milestogo/reform/historic-reform1/handbook/source/credits/index.rst

Credits
=======

:Concept, Electronics, Software, Manual, Assembly: Lukas F. Hartmann (mntmn)

:Industrial Design: Ana Beatriz Albertini Dantas

:Sleeve Design, Assembly: Greta Melnik

:Special Thanks: FabLab Berlin, Neuform, CCC Berlin/n-te, Fedevel/Voipac, etnaviv, Xorg, Mesa, wayland, Igalia, heise/Make Germany/Helga Hansen, Philip Steffan, Maker Faire Berlin, Interface Critique/Florian Hadler, Gabriel Yoran, JD Music Labs, Crowd Supply, malcolmputer, zakx, darthrake, erlehmann, plomlompom, scallo, dridde, grncdr, oomono, Daniel Stone, Martin Meyerhoff, Gregor May, Chris Healy, Martin Borgert, Stephan Urbach, furan, Radoslaw Kujawa, Novena, Mastodon, a1k, Disko Koenig, S.I.H., The Reform Beta Testers (you!)

:Inter UI Font: rsms

:PCB Production: PCBWay

:Aluminum Milling: Shandong Jiepurui Model Technology Co., Ltd.
                   
:3D Printer: BCN3D Sigma R17

:Reflow Oven: ReflowR

:Stereolitography: Formlabs Form2

:Lab Tools: Rigol DS1054Z, Fluke 117. Weller WD-1, Toolcraft SMD Rework Station
            
:Parts Suppliers: Mouser, DigiKey, Conrad, Voelkner (Fans), GMK Electronic Design (Switches), Schraubenhandel Machholz (Screws), Smooth Group (Hinges), Palm Stream International (Displays), HereWin (Batteries)
                  
:Chips Used: NXP (MCIMX6Q5EYM10AC, SGTL5000XNAA3), Micron (MT41K512M16HA-125), Texas Instruments (BQ24650RVAT, INA260AIPW, TPS61235RWLR, TUSB4041IPAPR, TPS2044BDR, TLV70012, TLV1117-15, LP3962EMP-2.5), ON Semiconductor (CM2020-00TR), Microchip (KSZ9031RNXIA, ATTINY841-SSU, ATMEGA32U4), Diodes Inc. (AP1501A-33K5G-13), Rohm (BR24L02NUX-WTR)
             
:Software Used: Debian GNU/Linux, KiCAD, Inkscape, GIMP, Emacs, Vim, Git, Arduino, LUFA, Blender, Cura, slic3r, Solidworks, FreeCAD, OpenSCAD, Sphinx

Web: https://mntmn.com/reform 
Email: lukas@mntmn.com
Copyright 2018 MNT Media and Technology UG (haftungsbeschränkt), Bluecherstr. 32C, 10961 Berlin
Managing Director: Lukas F. Hartmann
Registergericht: Amtsgericht Charlottenburg
Aktenzeichen: HRB 136605 B
VAT ID: DE278908891
WEEE: DE 33315564 

This book is licensed under GPLv3 or newer.
