milestogo/reform/historic-reform1/handbook/source/motherboard/reform-motherboard-page-1b.pdf

1 2 3 4 5 6

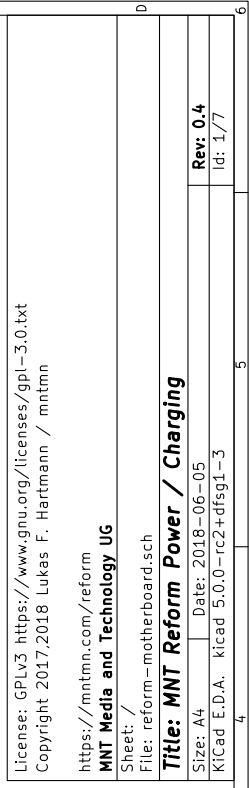
[picture p17: figure]

1 2 3 4 5 6

A

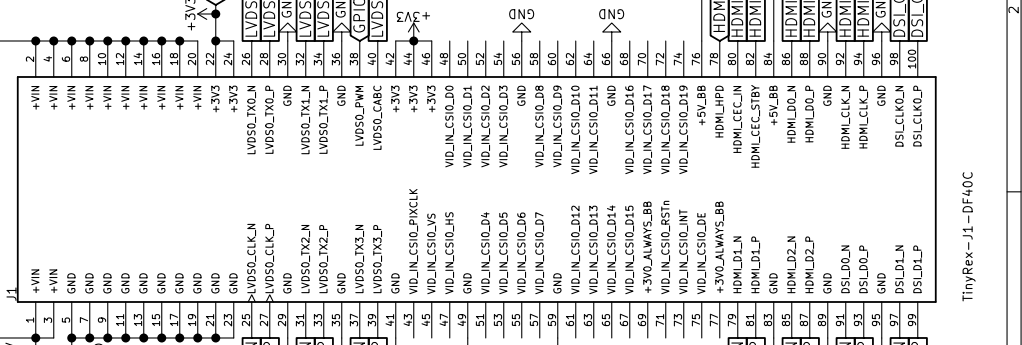
[picture p18: figure]
1 +VIN; 2 +VIN; 3 +VIN; 4 GND; 5 +VIN; 6 GND; 7 +VIN; 8 GND

BC

D

A

BC

D Date: 2018-06-05 KiCad E.D.A. kicad 5.0.0-rc2+dfsg1-3 Rev: 0.4 Size: A4 Id: 1/7 License: GPLv3 https://www.gnu.org/licenses/gpl-3.0.txt Copyright 2017,2018 Lukas F. Hartmann / mntmn https://mntmn.com/reform MNT Media and Technology UG Sheet: / File: reform-motherboard.sch Title: MNT Reform Power / Charging +VIN

9 +VIN 10 +VIN 20 GND 30 LVDS0_CABC 40 VID_IN_CSI0_D1 50 VID_IN_CSI0_D9 60 VID_IN_CSI0_D17 70 HDMI_CEC_IN 80 GND 90 GND 11 GND 21 LVDS0_TX2_N 31 GND 41 VID_IN_CSI0_D4 51 VID_IN_CSI0_D12 61 VID_IN_CSI0_RSTn 71 HDMI_D1_P 81 DSI_D0_N 91 +VIN 12 +3V3 22 LVDS0_TX1_N 32 +3V3 42 VID_IN_CSI0_D2 52 VID_IN_CSI0_D10 62 VID_IN_CSI0_D18 72 HDMI_CEC_STBY 82 HDMI_CLK_N 92 GND 13 GND 23 LVDS0_TX2_P 33 VID_IN_CSI0_PIXCLK 43 VID_IN_CSI0_D5 53 VID_IN_CSI0_D13 63 VID_IN_CSI0_INT 73 GND 83 DSI_D0_P 93 +VIN 14 +3V3 24 LVDS0_TX1_P 34 +3V3 44 VID_IN_CSI0_D3 54 VID_IN_CSI0_D11 64 VID_IN_CSI0_D19 74 +5V_BB 84 HDMI_CLK_P 94 GND 15 LVDS0_CLK_N 25 GND 35 VID_IN_CSI0_VS 45 VID_IN_CSI0_D6 55 VID_IN_CSI0_D14 65 VID_IN_CSI0_DE 75 HDMI_D2_N 85 GND 95 +VIN 16 LVDS0_TX0_N 26 GND 36 +3V3 46 GND 56 GND 66 +5V_BB 76 HDMI_D0_N 86 GND 96 GND 17 LVDS0_CLK_P 27 LVDS0_TX3_N 37 VID_IN_CSI0_HS 47 VID_IN_CSI0_D7 57 VID_IN_CSI0_D15 67 +3V0_ALWAYS_BB 77 HDMI_D2_P 87 DSI_D1_N 97 +VIN 18 LVDS0_TX0_P 28 LVDS0_PWM 38 VID_IN_CSI0_D0 48 VID_IN_CSI0_D8 58 VID_IN_CSI0_D16 68 HDMI_HPD 78 HDMI_D0_P 88 DSI_CLK0_N 98 GND 19 GND 29 LVDS0_TX3_P 39 GND 49 GND 59 +3V0_ALWAYS_BB 69 HDMI_D1_N 79 GND 89 DSI_D1_P 99 DSI_CLK0_P 100 J1TinyRex-J1-DF40C BOOT_MODE1_CON

# 1 RSTINn

# 2 BOOT_MODE0_CON

# 3 RSTOUTn

# 4 POK_1V5

# 5 PMIC_ON_REQ

# 6 POK_5V_BB

# 7 ON_OFF

# 8 POK_3V3_BB

9 USER_BUTTON 10 AUD4_TXD 20 FLEXCAN1_TX 30 GND 40 I2C2_SDA 50 UART4_RXD 60 USB_OC 70 PCIE_CLK_N 80 GND 90 GND 11 GND 21 GND 31 GND 41 GND 51 UART2_TXD 61 GND 71 PCIE_TX_P 81 CSI_D2_N 91 GND 12 AUD4_RXD 22 FLEXCAN1_RX 32 SATA_TX_N 42 I2C3_SDA 52 UART5_TXD 62 USB1_PWR_EN 72 PCIE_CLK_P 82 CSI_D0_N 92 CPU_GPIO0 13 CSPI1_CLK 23 SD3_CD 33 SD3_DATA0 43 UART1_TXD 53 UART2_RXD 63 USB0_N 73 GND 83 CSI_D2_P 93 AUD4_CLK 14 GND 24 GND 34 SATA_TX_P 44 I2C3_SCL 54 UART5_RXD 64 USB0_PWR_EN 74 GND 84 CSI_D0_P 94 CPU_GPIO1 15 CSPI1_MOSI 25 SD3_WP 35 SD3_DATA1 45 UART1_RXD 55 GND 65 USB0_P 75 PCIE_RX_N 85 GND 95 AUD4_TXC 16 I2C1_SCL 26 SATA_RX_N 36 GND 46 GND 56 GND 66 PCIE_WAKE 76 CSI_CLK0_N 86 GND 96 GPIO_OR_PWM_1 17 CSPI1_MISO 27 SD3_CLK 37 SD3_DATA2 47 UART1_RTS 57 USB1_N 67 GND 77 PCIE_RX_P 87 CSI_D3_N 97 AUD4_TXFS 18 I2C1_SDA 28 SATA_RX_P 38 I2C2_SCL 48 UART4_TXD 58 USB0_ID 68 GND 78 CSI_CLK_P 88 CSI_D1_N 98 GPIO_OR_PWM_2 19 CSPI1_CS0 29 SD3_CMD 39 SD3_DATA3 49 UART1_CTS 59 USB1_P 69 PCIE_TX_N 79 GND 89 CSI_D3_P 99 CSI_D1_P 100 J2TinyRex-J2-DF40C TRD0_N

# 1 TRD2_N

# 2 TRD0_P

# 3 TRD2_P

# 4 GND

# 5 +1V2_BB

# 6 TRD1_N

# 7 TRD3_N

# 8 TRD1_P

9 TRD3_P 10 +1V2_BB 20 DISP1_D4 30 DISP1_D12 40 SD4_DATA0 50 SD4_DATA4 60 CSPI2_CLK 70 GND 80 SD1_CMD 90 GND 11 DISP1_RDX 21 DISP1_D2 31 DISP1_D10 41 DISP1_D18 51 SD4_WP 61 UART3_TXD 71 SD1_DATA4 81 GND 91 +1V2_BB 12 DISP1_PIXCLK 22 DISP1_D5 32 DISP1_D13 42 SD4_DATA1 52 SD4_DATA5 62 CSPI2_MOSI 72 SD1_DATA0 82 GND 92 DISP1_INT 13 DISP1_WRX 23 DISP1_D3 33 DISP1_D11 43 DISP1_D19 53 SD4_CD 63 UART3_RXD 73 SD1_DATA5 83 NANDF_D4 93 ENET_LED_LINK 14 DISP1_VSYNCH 24 DISP1_D6 34 DISP1_D14 44 SD4_DATA2 54 SD4_DATA6 64 CSPI2_MISO 74 SD1_DATA1 84 NANDF_ALE 94 DISP1_CS1 15 GND 25 GND 35 GND 45 GND 55 SD1_WP 65 UART3_RTS 75 SD1_DATA6 85 NANDF_D5 95 ENET_LED_RX 16 DISP1_HSYNCH 26 DISP1_D7 36 DISP1_D15 46 SD4_DATA3 56 SD4_DATA7 66 CSPI2_CS0 76 SD1_DATA2 86 NANDF_CLE 96 DISP1_CS0 17 DISP1_D0 27 DISP1_D8 37 DISP1_D16 47 SD4_CLK 57 SD1_CD 67 UART3_CTS 77 SD1_DATA7 87 NANDF_D6 97 DISP1_RSTn 18 GND 28 GND 38 +2V5_BB 48 +2V5_BB 58 GND 68 CSPI2_CS1 78 SD1_DATA3 88 NANDF_RB0 98 DISP1_D/CX 19 DISP1_D1 29 DISP1_D9 39 DISP1_D17 49 SD4_CMD 59 GND 69 GND 79 SD1_CLK 89 NANDF_D7 99 NANDF_WPn 100 J3TinyRex-J3-DF40C ReformPower reform-power.sch +5V GND +5V GND +3V3 +3V3 POK_1V5_MODULE POK_5V POK_3V3USB1_N USB1_P USB0_N USB0_P RSTINn RSTOUTn HDMI_HPD HDMI_CLK_N HDMI_CLK_P HDMI_D1_N HDMI_D1_P HDMI_D2_N HDMI_D2_P HDMI_D0_N HDMI_D0_P UART1_TXD UART1_RTS UART1_RXD UART1_CTS SD1_DATA0 SD1_DATA1 SD1_DATA2 SD1_DATA3 SD1_CMD SD1_WP SD1_CD SD1_CLK +2V5 SATA_RX_N SATA_RX_P SATA_TX_N SATA_TX_P USB_OC HDMI_CEC_IN HDMI_CEC_STBY ReformSATA_SD reform-sata-sd.sch SD3_DATA0 SD3_DATA1 SD3_DATA2 SD3_DATA3 GND GND GND SD3_CD SD3_WP SD3_CMD SD3_CLK ReformPCIe reform-pcie.sch PCIE_TX_N PCIE_TX_P PCIE_RX_N PCIE_RX_P PCIE_WAKE PCIE_CLK_N PCIE_CLK_P reform-eth-usb reform-eth-usb.sch ReformDisplay reform-display.sch

0 GND MH1 BoardMount MH2 BoardMount MH3 BoardMount MH4 BoardMount GND GND GND GND MH5 ModuleMount MH6 ModuleMount TP13 TEST_1V2 1

4

3

2

# 1 J20 Conn_GPIO1

6

5

4

3

2

1 J35 Conn_SPI1 +3V3 +3V3 GND CSI_D2_N CSI_D2_P CSI_D3_N CSI_D3_P CSI_D0_N CSI_D0_P CSI_D1_N CSI_D1_P GND GND CSI_CLK0_N CSI_CLK0_P DSI_D0_N DSI_D0_P DSI_D1_N DSI_D1_P DSI_CLK0_N DSI_CLK0_P J8 TEST_BM0
