milestogo/reform/historic-reform1/handbook/source/index.rst

.. Reform documentation master file, created by
   sphinx-quickstart on Thu Jun  7 14:01:00 2018.
   You can adapt this file completely to your liking, but it should at least
   contain the root `toctree` directive.
   
MNT Reform Operator Handbook
============================

.. toctree::
   :maxdepth: 3

   quickstart/index
   case/index
   motherboard/index
   motherboard/attiny
   keyboard/index
   trackball/index
   thermal/index
   boot/index
   debug/index
   credits/index

.. raw:: latex

    \clearpage
