milestogo/reform/historic-reform1/handbook/source/motherboard/index.rst

The Motherboard
===============


            
Schematics
----------



Power
-----



Storage
-------



Display
-------


           
PCIe
----



Ethernet, USB
-------------


            
Audio
-----
