milestogo/reform/reform2-handbook/misc-content/old-reform1-handbook/reform-handbook.pdf

## CONTENTS

1 Quick Start | 1
2 The Case | 3
3 The Motherboard | 9
4 The Battery/Lid Controller | 19
5 The Keyboard | 21
6 The Trackball | 25

i

7 Thermal | 29
8 System Boot Details | 31
9 Debugging | 33
10 Credits | 35

ii

CHAPTER

## ONE

## QUICK START

Thank you for acquiring MNT Reform, a portable open-source computer system. Reform can be powered either by the internal LiFePo4 battery or by the 5V wall adapter. The wall adapter will automatically charge the battery if present. For safety reasons, the battery cable is not connected by default. To use the battery, unscrew the bottom lid and plug the white battery cable plug into the battery connector on the motherboard. Then reattach the bottom lid.
To switch the system on, push the power switch (located on the front of the device) to the right. The i.MX6 QuadPlus (https://www.nxp.com/products/processors-and-microcontrollers/arm-based-processors-and-mcus/i.mx-applications-processors/i.mx-6-processors/i.mx-6quadplus-proce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) System-on-Chip will try to boot from the internal SD card. You should be greeted by U-Boot and the MNT logo in the upper right corner of the display. If not interrupted by a keypress, Reform will boot into the Debian GNU/Linux operating system that is preinstalled on the SD card. The kernel will show diagnostic information as it activates all the devices in the system, and you’ll end up at the login prompt if everything is OK.
To log in, enter root as the username. There is no default password, so you should secure the root account by setting a password. After completing the setup process, you can do this by executing:

passwd

After the first login, the setup script will run and guide you through a few steps like setting the timezone, keyboard layout, network settings and so on.
From the console environment, you can:
- Format an mSATA SSD drive (if you put one in the mSATA slot) and install an OS to it
- Create standard user accounts
- Inspect or repair the system
To start the X windowing system, type:

xinit

By default, when using the root account, this will start the OpenBox window manager. You can change this by editing the file /root/.xinitrc.
You can install additional software and desktop environments by using apt, for example apt install firefox. You can find more information about using apt by reading its manual page. Manual pages are accessed by executing man programname, for example:

1

MNT Reform Operator Handbook

man apt

Enjoy your Reform computer!

### 2 Chapter 1. Quick Start

## TWO

## THE CASE

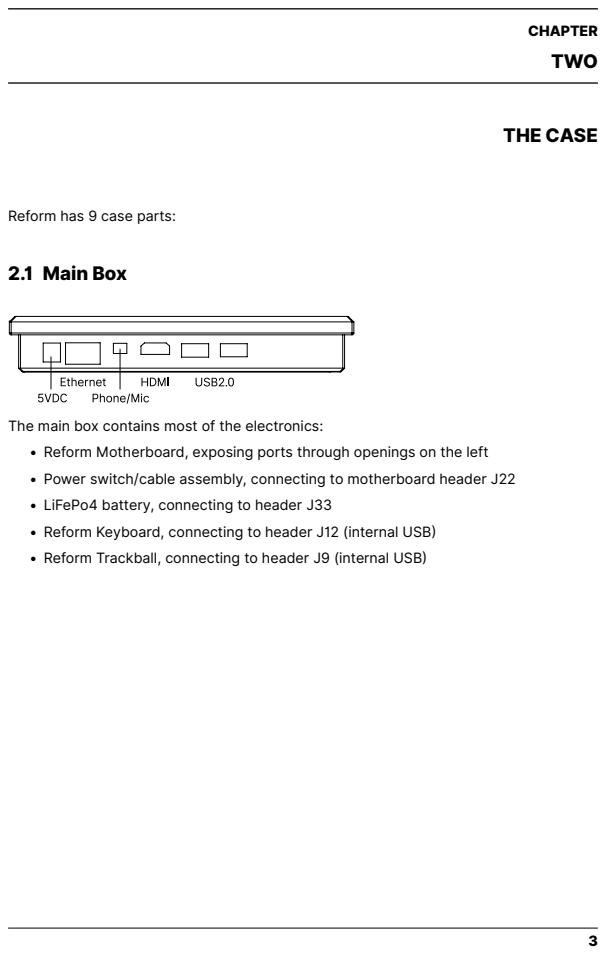
[picture p20: page 7]
CHAPTER; 2.1 Main Box

Reform has 9 case parts:

The main box contains most of the electronics:
• Reform Motherboard, exposing ports through openings on the left
• Power switch/cable assembly, connecting to motherboard header J22
• LiFePo4 battery, connecting to header J33
• Reform Keyboard, connecting to header J12 (internal USB)
• Reform Trackball, connecting to header J9 (internal USB)

## 2.2 Main Box Top

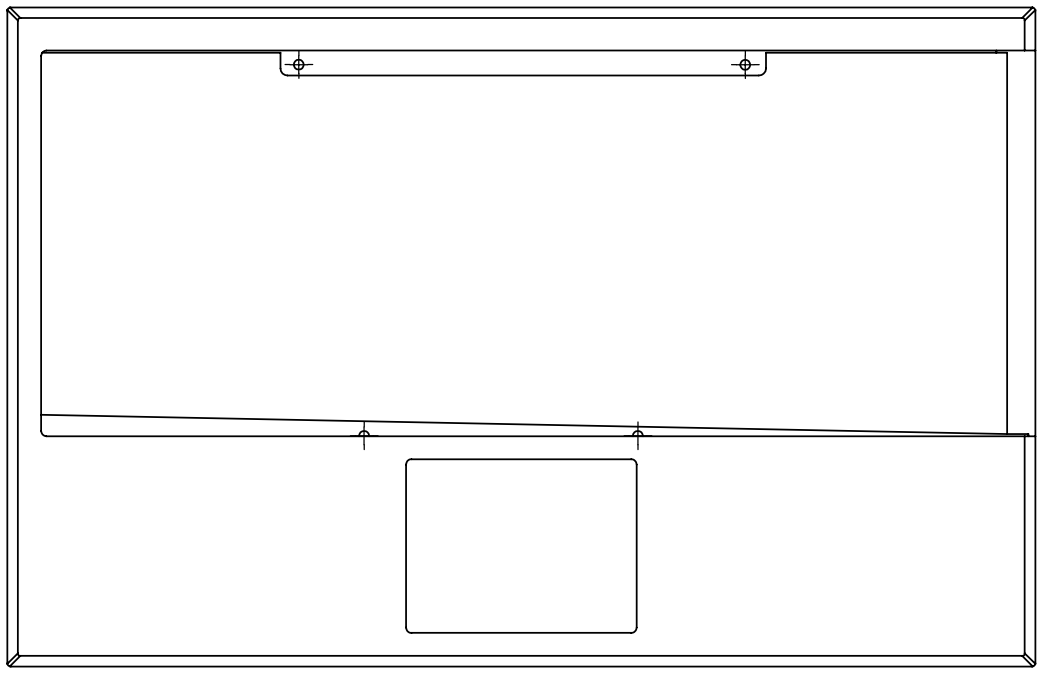
[picture p21: figure]

The main box top is pressed onto the main box to close it from the top. It acts as a palm rest and bezel for the keyboard and trackball. The keyboard is slided into this part’s keyboard slot from the right.

### 4 Chapter 2. The Case

## 2.3 Screen Back

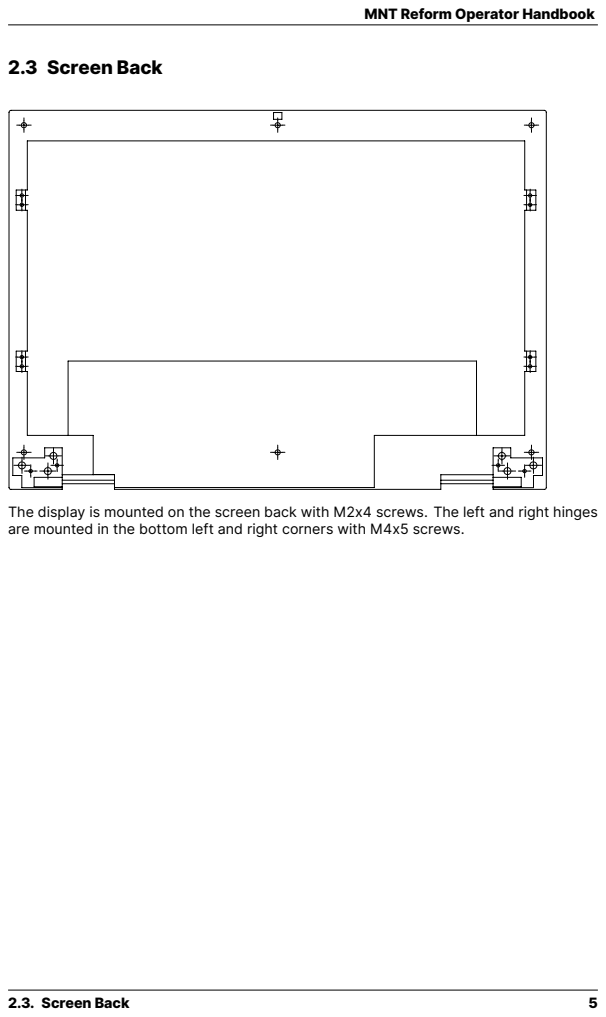
[picture p22: page 9]
2.3. Screen Back

The display is mounted on the screen back with M2x4 screws. The left and right hinges
are mounted in the bottom left and right corners with M4x5 screws.

## 2.4 Screen Front

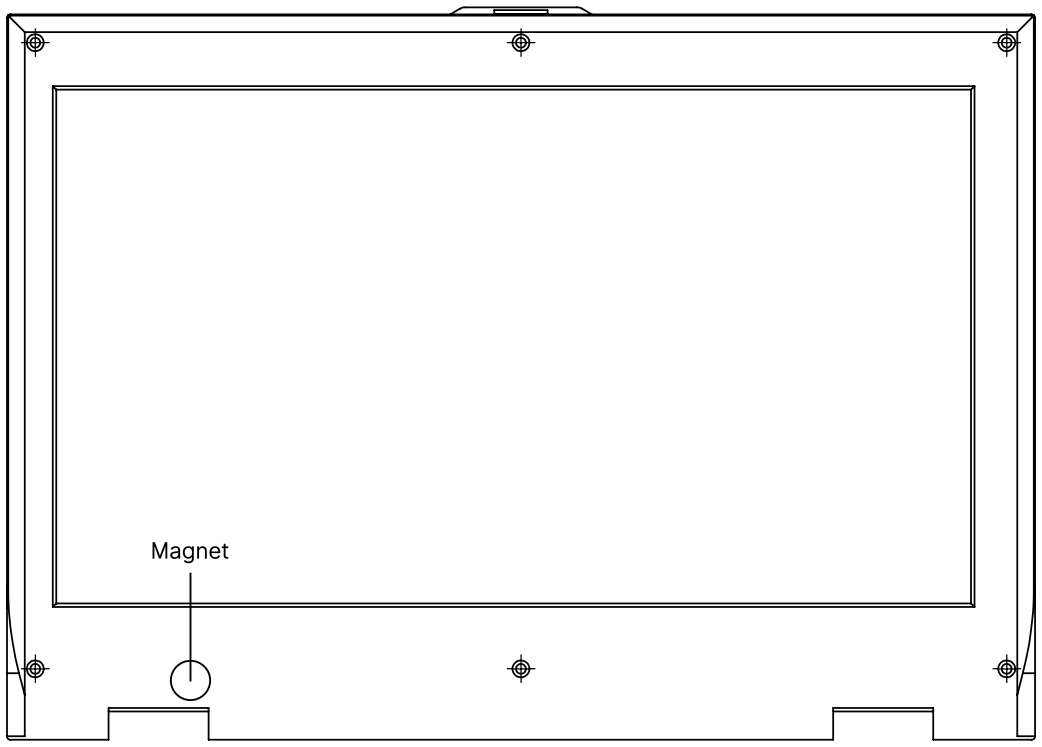
[picture p23: figure]

This part serves as a bezel for the display and holds the case closing strap. It also has a magnet attached to it on the lower left that is sensed by the lid sensor. The screen front is mounted to the back with M3x6 screws.

## 2.5 Screen Support

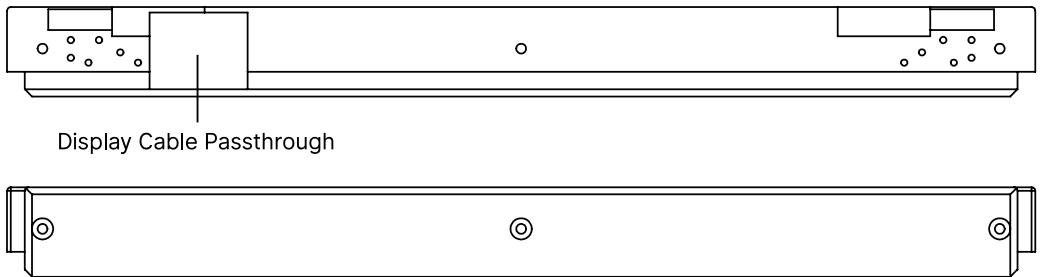
[picture p24: figure]

The screen support connects the main box to the screen via the hinges. The display’s LVDS (motherboard header J14) and power cable (motherboard header J26) is passed through this part, as well as the lid sensor cable (J34).

### 6 Chapter 2. The Case

## 2.6 Screen Support Lid

This is a thin part covering the screen support’s top. On the left, it contains a pocket for the hall effect sensor that detects the magnet on the screen front. The sensor signals opening and closing of the lid.

## 2.7 Keyboard Closure

This part is inserted into the main box top after the keyboard to secure it in place.

## 2.8 Grid Plate

This lasercut acrylic part is sandwiched between the main box’ inner top and the motherboard. It has the mounting holes for the motherboard and other internal devices and isolates the motherboard from the keyboard.

## 2.9 Bottom Plate

The bottom plate closes the main box from the bottom. It contains mounting holes for the fan and vent holes for the fan’s air intake. The fan is connected to motherboard header J15 before screwing in the plate.

2.6. Screen Support Lid | 7

### 8 Chapter 2. The Case

9

## THREE

## THE MOTHERBOARD

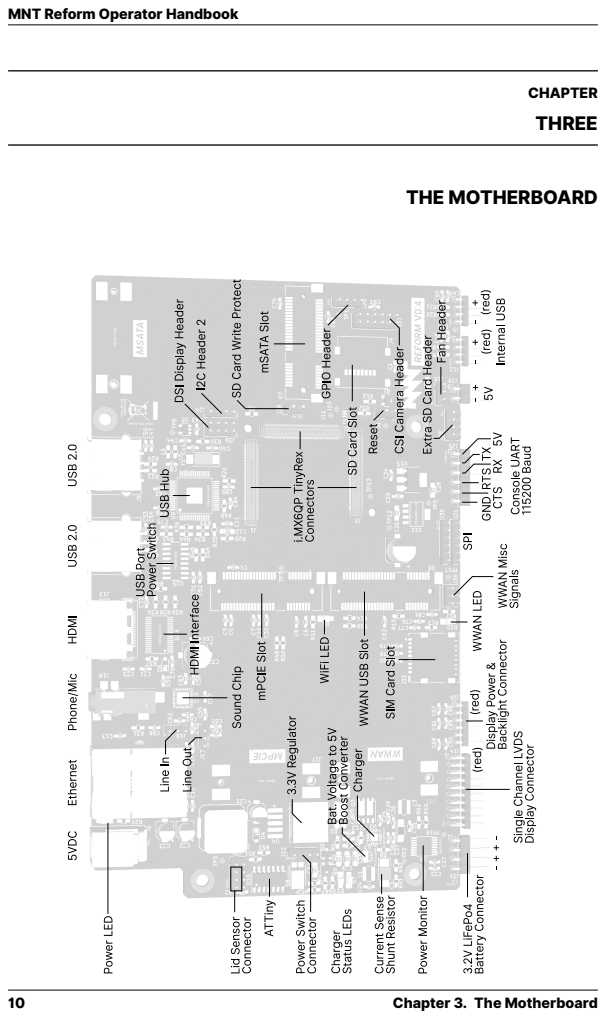
[picture p25: page 14]
CHAPTER

10 Chapter 3. The Motherboard

## 3.1 Schematics

1 2 3 4 5 6

1 2 3 4 5 6

A

BC

D

A

BC

D Date: 2018-06-05 KiCad E.D.A. kicad 5.0.0-rc2+dfsg1-3 Rev: 0.4 Size: A4 Id: 1/7 License: GPLv3 https://www.gnu.org/licenses/gpl-3.0.txt Copyright 2017,2018 Lukas F. Hartmann / mntmn https://mntmn.com/reform MNT Media and Technology UG Sheet: / File: reform-motherboard.sch Title: MNT Reform Power / Charging +VIN

1 +VIN

2 +VIN
3 +VIN

4 GND
5 +VIN

6 GND
7 +VIN

8 GND

9 +VIN 10 +VIN 20 GND 30 LVDS0_CABC 40 VID_IN_CSI0_D1 50 VID_IN_CSI0_D9 60 VID_IN_CSI0_D17 70 HDMI_CEC_IN 80 GND 90 GND 11 GND 21 LVDS0_TX2_N 31 GND 41 VID_IN_CSI0_D4 51 VID_IN_CSI0_D12 61 VID_IN_CSI0_RSTn 71 HDMI_D1_P 81 DSI_D0_N 91 +VIN 12 +3V3 22 LVDS0_TX1_N 32 +3V3 42 VID_IN_CSI0_D2 52 VID_IN_CSI0_D10 62 VID_IN_CSI0_D18 72 HDMI_CEC_STBY 82 HDMI_CLK_N 92 GND 13 GND 23 LVDS0_TX2_P 33 VID_IN_CSI0_PIXCLK 43 VID_IN_CSI0_D5 53 VID_IN_CSI0_D13 63 VID_IN_CSI0_INT 73 GND 83 DSI_D0_P 93 +VIN 14 +3V3 24 LVDS0_TX1_P 34 +3V3 44 VID_IN_CSI0_D3 54 VID_IN_CSI0_D11 64 VID_IN_CSI0_D19 74 +5V_BB 84 HDMI_CLK_P 94 GND 15 LVDS0_CLK_N 25 GND 35 VID_IN_CSI0_VS 45 VID_IN_CSI0_D6 55 VID_IN_CSI0_D14 65 VID_IN_CSI0_DE 75 HDMI_D2_N 85 GND 95 +VIN 16 LVDS0_TX0_N 26 GND 36 +3V3 46 GND 56 GND 66 +5V_BB 76 HDMI_D0_N 86 GND 96 GND 17 LVDS0_CLK_P 27 LVDS0_TX3_N 37 VID_IN_CSI0_HS 47 VID_IN_CSI0_D7 57 VID_IN_CSI0_D15 67 +3V0_ALWAYS_BB 77 HDMI_D2_P 87 DSI_D1_N 97 +VIN 18 LVDS0_TX0_P 28 LVDS0_PWM 38 VID_IN_CSI0_D0 48 VID_IN_CSI0_D8 58 VID_IN_CSI0_D16 68 HDMI_HPD 78 HDMI_D0_P 88 DSI_CLK0_N 98 GND 19 GND 29 LVDS0_TX3_P 39 GND 49 GND 59 +3V0_ALWAYS_BB 69 HDMI_D1_N 79 GND 89 DSI_D1_P 99 DSI_CLK0_P 100 J1TinyRex-J1-DF40C BOOT_MODE1_CON

1 RSTINn

2 BOOT_MODE0_CON
3 RSTOUTn

4 POK_1V5
5 PMIC_ON_REQ

6 POK_5V_BB
7 ON_OFF

8 POK_3V3_BB

9 USER_BUTTON 10 AUD4_TXD 20 FLEXCAN1_TX 30 GND 40 I2C2_SDA 50 UART4_RXD 60 USB_OC 70 PCIE_CLK_N 80 GND 90 GND 11 GND 21 GND 31 GND 41 GND 51 UART2_TXD 61 GND 71 PCIE_TX_P 81 CSI_D2_N 91 GND 12 AUD4_RXD 22 FLEXCAN1_RX 32 SATA_TX_N 42 I2C3_SDA 52 UART5_TXD 62 USB1_PWR_EN 72 PCIE_CLK_P 82 CSI_D0_N 92 CPU_GPIO0 13 CSPI1_CLK 23 SD3_CD 33 SD3_DATA0 43 UART1_TXD 53 UART2_RXD 63 USB0_N 73 GND 83 CSI_D2_P 93 AUD4_CLK 14 GND 24 GND 34 SATA_TX_P 44 I2C3_SCL 54 UART5_RXD 64 USB0_PWR_EN 74 GND 84 CSI_D0_P 94 CPU_GPIO1 15 CSPI1_MOSI 25 SD3_WP 35 SD3_DATA1 45 UART1_RXD 55 GND 65 USB0_P 75 PCIE_RX_N 85 GND 95 AUD4_TXC 16 I2C1_SCL 26 SATA_RX_N 36 GND 46 GND 56 GND 66 PCIE_WAKE 76 CSI_CLK0_N 86 GND 96 GPIO_OR_PWM_1 17 CSPI1_MISO 27 SD3_CLK 37 SD3_DATA2 47 UART1_RTS 57 USB1_N 67 GND 77 PCIE_RX_P 87 CSI_D3_N 97 AUD4_TXFS 18 I2C1_SDA 28 SATA_RX_P 38 I2C2_SCL 48 UART4_TXD 58 USB0_ID 68 GND 78 CSI_CLK_P 88 CSI_D1_N 98 GPIO_OR_PWM_2 19 CSPI1_CS0 29 SD3_CMD 39 SD3_DATA3 49 UART1_CTS 59 USB1_P 69 PCIE_TX_N 79 GND 89 CSI_D3_P 99 CSI_D1_P 100 J2TinyRex-J2-DF40C TRD0_N

1 TRD2_N

2 TRD0_P
3 TRD2_P

4 GND
5 +1V2_BB

6 TRD1_N
7 TRD3_N

8 TRD1_P

9 TRD3_P 10 +1V2_BB 20 DISP1_D4 30 DISP1_D12 40 SD4_DATA0 50 SD4_DATA4 60 CSPI2_CLK 70 GND 80 SD1_CMD 90 GND 11 DISP1_RDX 21 DISP1_D2 31 DISP1_D10 41 DISP1_D18 51 SD4_WP 61 UART3_TXD 71 SD1_DATA4 81 GND 91 +1V2_BB 12 DISP1_PIXCLK 22 DISP1_D5 32 DISP1_D13 42 SD4_DATA1 52 SD4_DATA5 62 CSPI2_MOSI 72 SD1_DATA0 82 GND 92 DISP1_INT 13 DISP1_WRX 23 DISP1_D3 33 DISP1_D11 43 DISP1_D19 53 SD4_CD 63 UART3_RXD 73 SD1_DATA5 83 NANDF_D4 93 ENET_LED_LINK 14 DISP1_VSYNCH 24 DISP1_D6 34 DISP1_D14 44 SD4_DATA2 54 SD4_DATA6 64 CSPI2_MISO 74 SD1_DATA1 84 NANDF_ALE 94 DISP1_CS1 15 GND 25 GND 35 GND 45 GND 55 SD1_WP 65 UART3_RTS 75 SD1_DATA6 85 NANDF_D5 95 ENET_LED_RX 16 DISP1_HSYNCH 26 DISP1_D7 36 DISP1_D15 46 SD4_DATA3 56 SD4_DATA7 66 CSPI2_CS0 76 SD1_DATA2 86 NANDF_CLE 96 DISP1_CS0 17 DISP1_D0 27 DISP1_D8 37 DISP1_D16 47 SD4_CLK 57 SD1_CD 67 UART3_CTS 77 SD1_DATA7 87 NANDF_D6 97 DISP1_RSTn 18 GND 28 GND 38 +2V5_BB 48 +2V5_BB 58 GND 68 CSPI2_CS1 78 SD1_DATA3 88 NANDF_RB0 98 DISP1_D/CX 19 DISP1_D1 29 DISP1_D9 39 DISP1_D17 49 SD4_CMD 59 GND 69 GND 79 SD1_CLK 89 NANDF_D7 99 NANDF_WPn 100 J3TinyRex-J3-DF40C ReformPower reform-power.sch +5V GND +5V GND +3V3 +3V3 POK_1V5_MODULE POK_5V POK_3V3USB1_N USB1_P USB0_N USB0_P RSTINn RSTOUTn HDMI_HPD HDMI_CLK_N HDMI_CLK_P HDMI_D1_N HDMI_D1_P HDMI_D2_N HDMI_D2_P HDMI_D0_N HDMI_D0_P UART1_TXD UART1_RTS UART1_RXD UART1_CTS SD1_DATA0 SD1_DATA1 SD1_DATA2 SD1_DATA3 SD1_CMD SD1_WP SD1_CD SD1_CLK +2V5 SATA_RX_N SATA_RX_P SATA_TX_N SATA_TX_P USB_OC HDMI_CEC_IN HDMI_CEC_STBY ReformSATA_SD reform-sata-sd.sch SD3_DATA0 SD3_DATA1 SD3_DATA2 SD3_DATA3 GND GND GND SD3_CD SD3_WP SD3_CMD SD3_CLK ReformPCIe reform-pcie.sch PCIE_TX_N PCIE_TX_P PCIE_RX_N PCIE_RX_P PCIE_WAKE PCIE_CLK_N PCIE_CLK_P reform-eth-usb reform-eth-usb.sch ReformDisplay reform-display.sch

0 GND MH1 BoardMount MH2 BoardMount MH3 BoardMount MH4 BoardMount GND GND GND GND MH5 ModuleMount MH6 ModuleMount TP13 TEST_1V2 1

4

3

2

1 J20 Conn_GPIO1

6

5

4

3

2

1 J35 Conn_SPI1 +3V3 +3V3 GND CSI_D2_N CSI_D2_P CSI_D3_N CSI_D3_P CSI_D0_N CSI_D0_P CSI_D1_N CSI_D1_P GND GND CSI_CLK0_N CSI_CLK0_P DSI_D0_N DSI_D0_P DSI_D1_N DSI_D1_P DSI_CLK0_N DSI_CLK0_P J8 TEST_BM0

3.1. Schematics | 11

## 3.2 Power

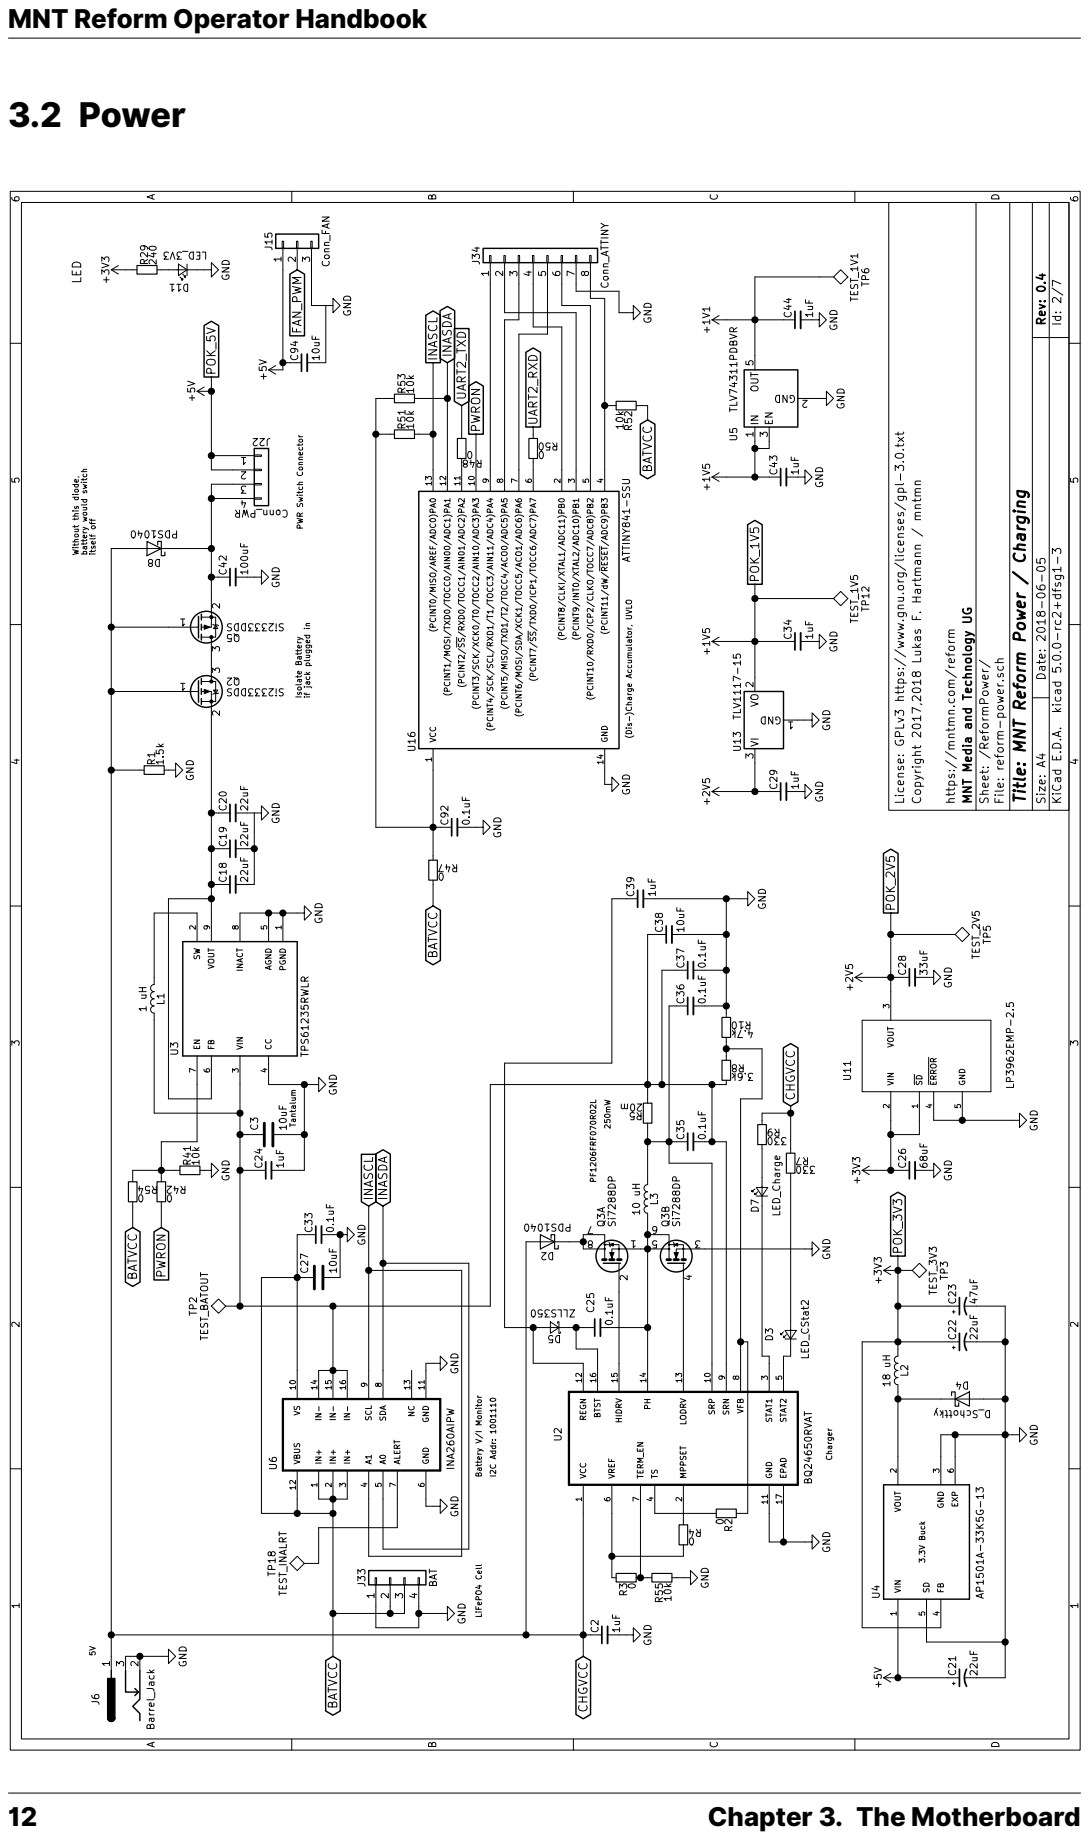
[picture p26: page 16]

D Date: 2018-06-05 KiCad E.D.A. kicad 5.0.0-rc2+dfsg1-3 Rev: 0.4 Size: A4 Id: 2/7 License: GPLv3 https://www.gnu.org/licenses/gpl-3.0.txt Copyright 2017,2018 Lukas F. Hartmann / mntmn https://mntmn.com/reform MNT Media and Technology UG Sheet: /ReformPower/ File: reform-power.sch Title: MNT Reform Power / Charging PGND

9 SRP 10 GND 11 REGN 12 LODRV 13 PH 14 HIDRV 15 BTST 16 EPAD 17 U2 BQ24650RVAT GND L3 10 uH C42 100uF GND GND C43 1uF GND C44 1uF GND TP6 TEST_1V1 GND +1V5 +1V1

4 J33 BAT INASCL INASDA INASCL INASDA BATVCC GND C92 0.1uF GND

9 VS 10 GND 11 VBUS 12 NC 13 IN- 14 IN- 15 IN- 16 U6INA260AIPW GND I2C Addr: 1001110 +5V PWRON 5V 3.3V Buck R11.5k GND +3V3 +5V

9 (PCINT3/SCK/XCK0/T0/TOCC2/AIN10/ADC3)PA3 10 (PCINT2/SS/RXD0/TOCC1/AIN01/ADC2)PA2 11 (PCINT1/MOSI/TXD0/TOCC0/AIN00/ADC1)PA1 12 (PCINT0/MISO/AREF/ADC0)PA0 13 GND 14 U16 ATTINY841-SSU R53 10k R51 10k PWRON

2 J6 Barrel_Jack GND C21 22uF L2 18 uH D4 D_Schottky C22 22uF C23 47uF +2V5 C26 68uF GND POK_2V5 C28 33uF GND TP5 TEST_2V5 TP3 TEST_3V3 GND C29 1uF GND POK_1V5 C34 1uF +1V5 GND TP12 TEST_1V5 SD

2 3Q2 Si2333DDS TP2 TEST_BATOUT Isolate Battery if jack plugged in 1

2 VI 3 U13 TLV1117-15 GND C24 1uF GND C27 10uF C33 0.1uF GND Battery V/I Monitor Tantalum IN+

6 U4AP1501A-33K5G-13 L1 1 uH C310uF GND GND C18 22uF C19 22uF C20 22uF GND GND

## 3.3 Storage

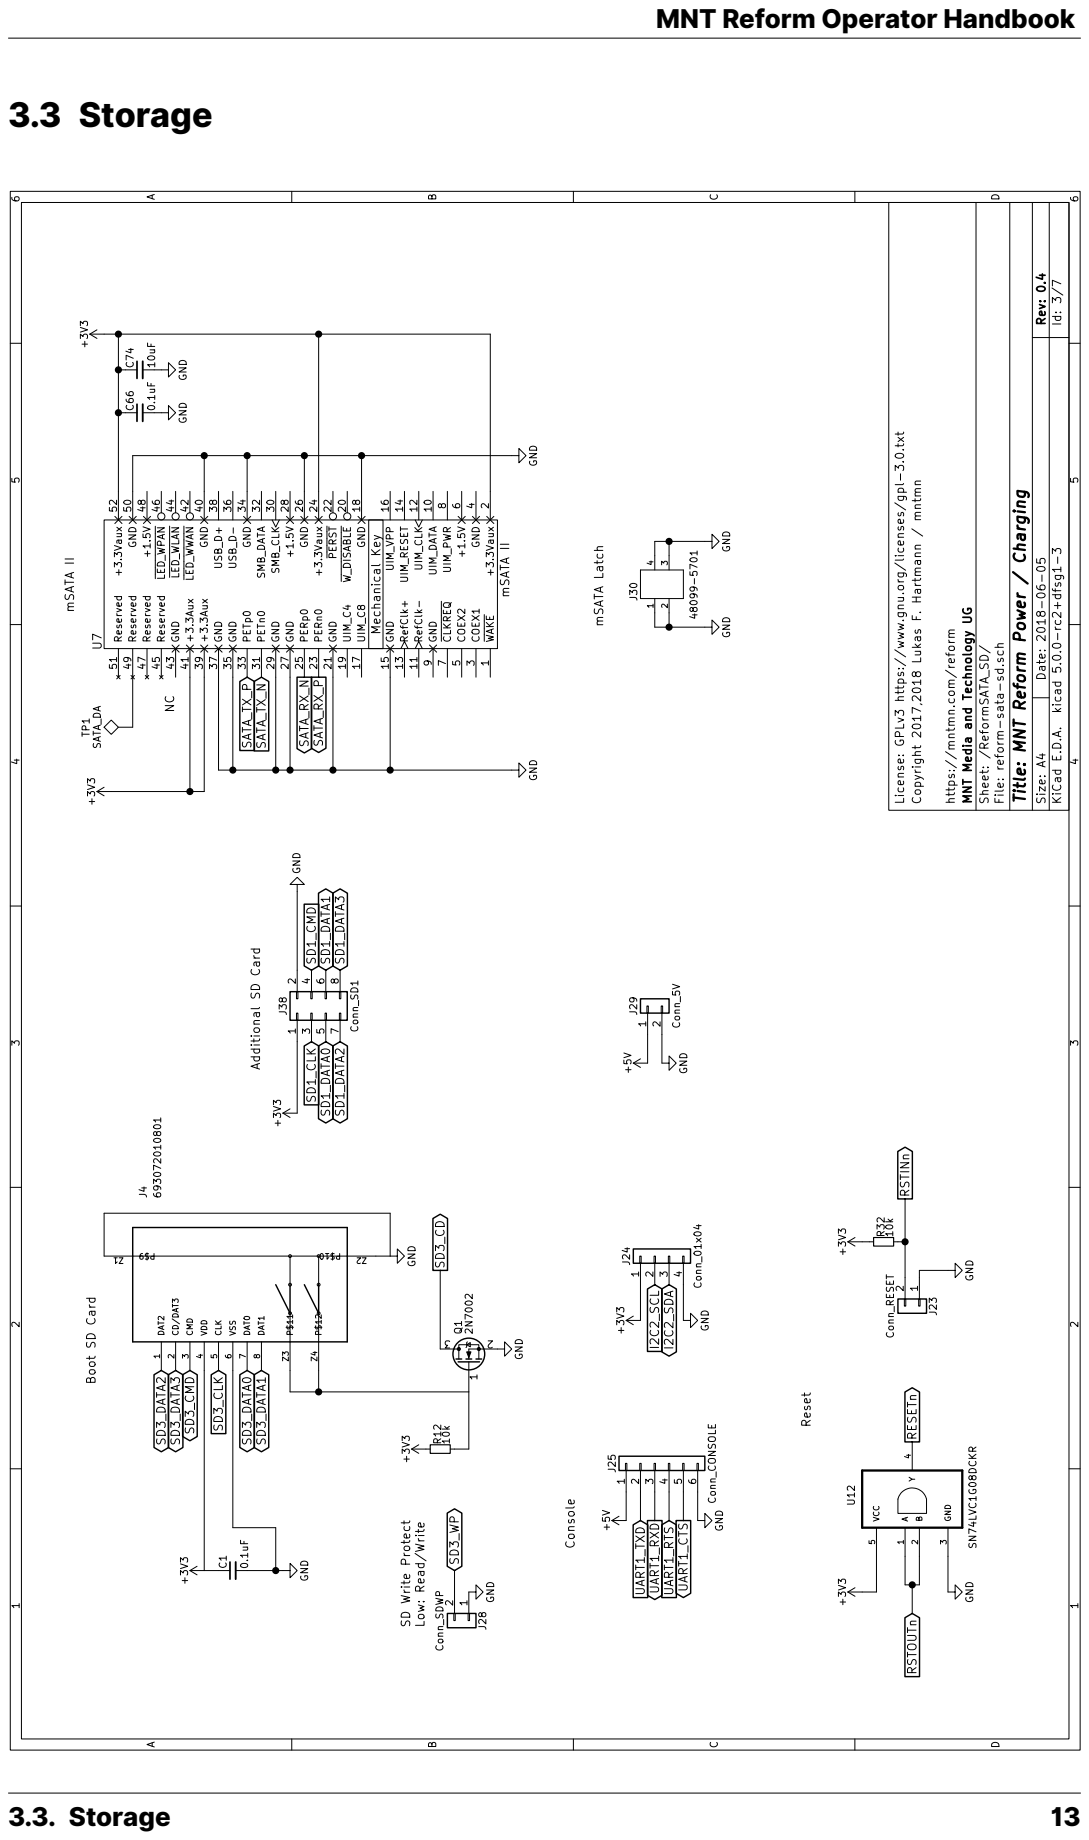
[picture p27: page 17]

D Date: 2018-06-05 KiCad E.D.A. kicad 5.0.0-rc2+dfsg1-3 Rev: 0.4 Size: A4 Id: 3/7 License: GPLv3 https://www.gnu.org/licenses/gpl-3.0.txt Copyright 2017,2018 Lukas F. Hartmann / mntmn https://mntmn.com/reform MNT Media and Technology UG Sheet: /ReformSATA_SD/ File: reform-sata-sd.sch Title: MNT Reform Power / Charging SD3_DATA2 SD3_DATA3 SD3_DATA0 SD3_DATA1 SD3_WP SD3_CD SD3_CMD SD3_CLK GND GND +3V3C10.1uF GND

9 UIM_DATA 10 W_DISABLE 20 SMB_CLK 30 GND 40 GND 50 RefClk- 11 GND 21 PETn0 31 +3.3Aux 41 Reserved 51 UIM_CLK 12 PERST 22 SMB_DATA 32 LED_WWAN 42 +3.3Vaux 52 RefClk+ 13 PERn0 23 PETp0 33 GND 43 UIM_RESET 14 +3.3Vaux 24 GND 34 LED_WLAN 44 GND 15 PERp0 25 GND 35 Reserved 45 UIM_VPP 16 GND 26 USB_D- 36 LED_WPAN 46 UIM_C8 17 GND 27 GND 37 Reserved 47 GND 18 +1.5V 28 USB_D+ 38 +1.5V 48 UIM_C4 19 GND 29 +3.3Aux 39 Reserved 49 U7 mSATA II SATA_TX_P SATA_TX_N SATA_RX_N SATA_RX_P mSATA II GND GND +3V3 +3V3 C74 10uF GND C66 0.1uF GND

3 J30 48099-5701 mSATA Latch GND GND NC TP1 SATA_DA Low: Read/Write SD1_DATA0 SD1_DATA1 SD1_DATA2 SD1_CMD SD1_DATA3 GND SD1_CLK +3V3 Additional SD Card 1 2

2 J29 Conn_5V +5V GND Mechanical Key WAKE

## 3.4 Display

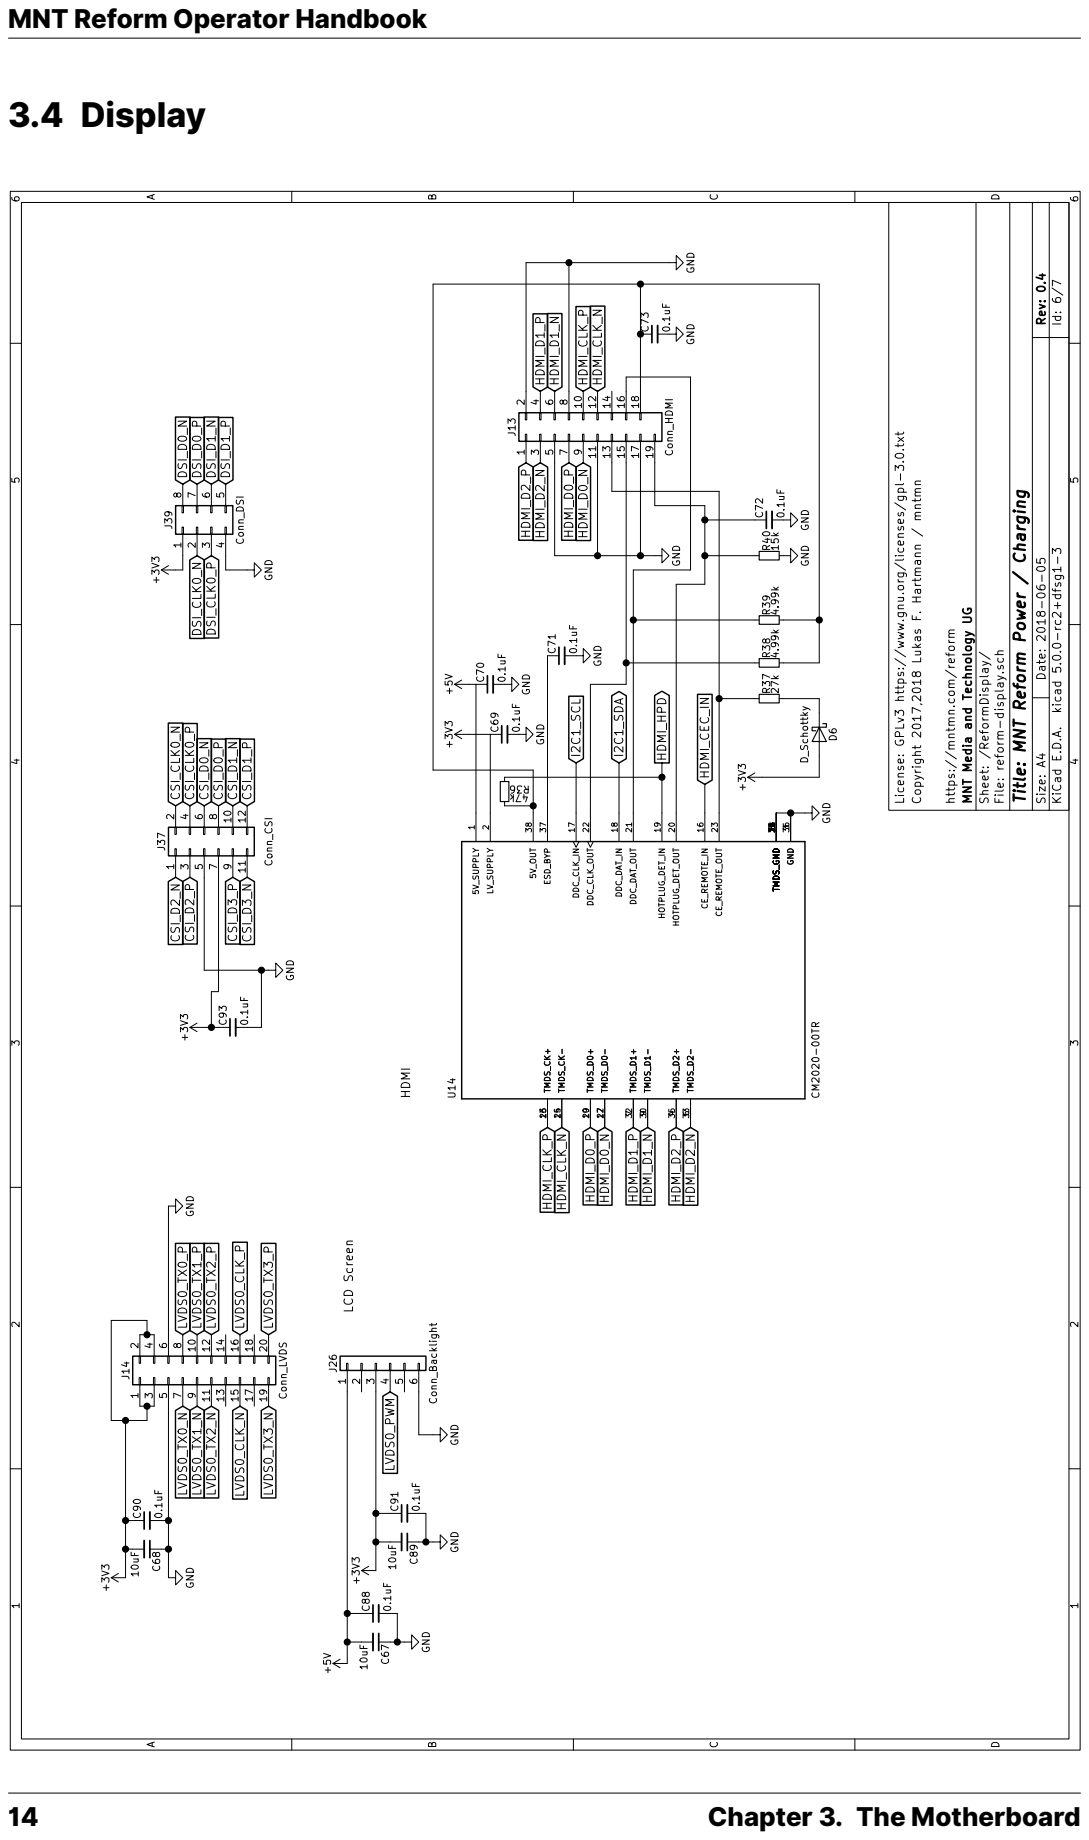
[picture p28: page 18]

D Date: 2018-06-05 KiCad E.D.A. kicad 5.0.0-rc2+dfsg1-3 Rev: 0.4 Size: A4 Id: 6/7 License: GPLv3 https://www.gnu.org/licenses/gpl-3.0.txt Copyright 2017,2018 Lukas F. Hartmann / mntmn https://mntmn.com/reform MNT Media and Technology UG Sheet: /ReformDisplay/ File: reform-display.sch Title: MNT Reform Power / Charging LVDS0_CLK_N LVDS0_CLK_P LVDS0_TX2_N LVDS0_TX2_P LVDS0_TX3_N LVDS0_TX3_P LVDS0_TX0_N LVDS0_TX0_P LVDS0_TX1_N LVDS0_TX1_P LVDS0_PWM +3V3 GND +5V HDMI_D1_P HDMI_D1_N HDMI_D2_P HDMI_D2_N HDMI_HPD HDMI_CLK_P HDMI_CLK_N HDMI_D0_P HDMI_D0_N HDMI_CEC_IN GND

8 TMDS_D1- 9 TMDS_D0+ 10 HOTPLUG_DET_OUT 20 TMDS_D1- 30 TMDS_GND 11 DDC_DAT_OUT 2131 TMDS_D0- 12 DDC_CLK_OUT 22 TMDS_D1+ 32 TMDS_CK+ 13 CE_REMOTE_OUT 23 TMDS_D2- 33 TMDS_GND 14 TMDS_CK- 24 34 15 25 TMDS_D2+ 35 CE_REMOTE_IN 16 TMDS_CK+ 26 GND 36 DDC_CLK_IN 17 TMDS_D0- 27 ESD_BYP 37 DDC_DAT_IN 18 TMDS_GND 28 5V_OUT 38 HOTPLUG_DET_IN 19 TMDS_D0+ 29 U14 CM2020-00TR HDMI_D0_P HDMI_D0_N HDMI_D1_P HDMI_D1_N HDMI_D2_P HDMI_D2_N HDMI_CLK_P HDMI_CLK_N +5V GNDC70 0.1uF C71 0.1uF GND C69 0.1uF +3V3 GND C73 0.1uF GND GND R40 15k C72 0.1uF GND GND R39 4.99k R38 4.99k D6 D_Schottky +3V3 R37 27k R36

6 J26 Conn_Backlight +3V3 GND C68 10uF C67 10uFGND LCD Screen HDMI C89 10uFGND C91 0.1uF C88 0.1uF C90 0.1uF CSI_D2_N CSI_D2_P CSI_D3_P CSI_D3_N CSI_CLK0_N CSI_CLK0_P CSI_D0_N CSI_D0_P CSI_D1_N CSI_D1_P

## 3.5 PCIe

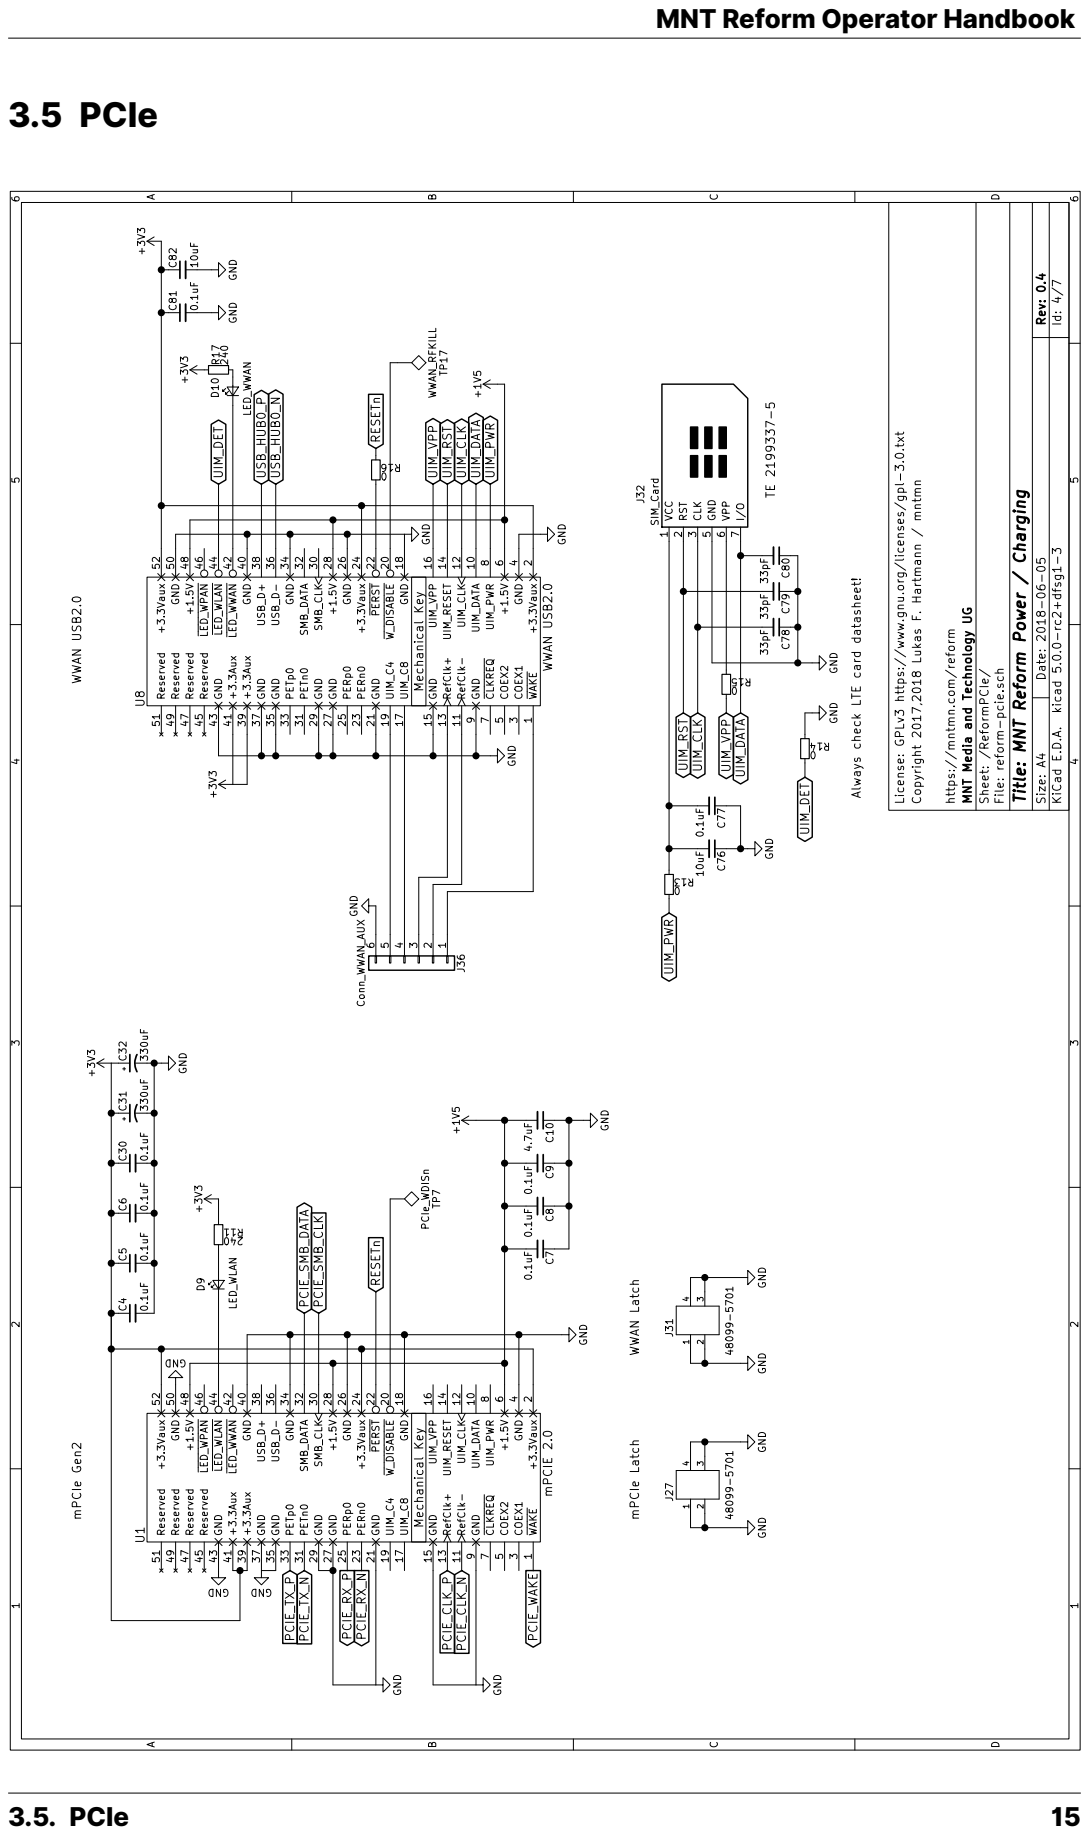
[picture p29: page 19]

D Date: 2018-06-05 KiCad E.D.A. kicad 5.0.0-rc2+dfsg1-3 Rev: 0.4 Size: A4 Id: 4/7 License: GPLv3 https://www.gnu.org/licenses/gpl-3.0.txt Copyright 2017,2018 Lukas F. Hartmann / mntmn https://mntmn.com/reform MNT Media and Technology UG Sheet: /ReformPCIe/ File: reform-pcie.sch Title: MNT Reform Power / Charging Mechanical Key WAKE

9 UIM_DATA 10 W_DISABLE 20 SMB_CLK 30 GND 40 GND 50 RefClk- 11 GND 21 PETn0 31 +3.3Aux 41 Reserved 51 UIM_CLK 12 PERST 22 SMB_DATA 32 LED_WWAN 42 +3.3Vaux 52 RefClk+ 13 PERn0 23 PETp0 33 GND 43 UIM_RESET 14 +3.3Vaux 24 GND 34 LED_WLAN 44 GND 15 PERp0 25 GND 35 Reserved 45 UIM_VPP 16 GND 26 USB_D- 36 LED_WPAN 46 UIM_C8 17 GND 27 GND 37 Reserved 47 GND 18 +1.5V 28 USB_D+ 38 +1.5V 48 UIM_C4 19 GND 29 +3.3Aux 39 Reserved 49 U8 WWAN USB2.0 GND +1V5 GND +3V3 D9 LED_WLAN

3 J31 48099-5701 WWAN Latch GND GND mPCIe Gen2 C82 10uF GND C81 0.1uF GND TE 2199337-5

3 J27 48099-5701 mPCIe Latch GND GND VCC

9 UIM_DATA 10 W_DISABLE 20 SMB_CLK 30 GND 40 GND 50 RefClk- 11 GND 21 PETn0 31 +3.3Aux 41 Reserved 51 UIM_CLK 12 PERST 22 SMB_DATA 32 LED_WWAN 42 +3.3Vaux 52 RefClk+ 13 PERn0 23 PETp0 33 GND 43 UIM_RESET 14 +3.3Vaux 24 GND 34 LED_WLAN 44 GND 15 PERp0 25 GND 35 Reserved 45 UIM_VPP 16 GND 26 USB_D- 36 LED_WPAN 46 UIM_C8 17 GND 27 GND 37 Reserved 47 GND 18 +1.5V 28 USB_D+ 38 +1.5V 48 UIM_C4 19 GND 29 +3.3Aux 39 Reserved 49 U1 mPCIE 2.0 PCIE_TX_P PCIE_TX_N PCIE_RX_P PCIE_RX_N PCIE_WAKE PCIE_CLK_P PCIE_CLK_NGND GND GND GND +1V5 C7 0.1uF C8 0.1uF C9 0.1uF C40.1uF C50.1uF C60.1uF GND C10 4.7uFGND GND GND RESETn TP7 PCIe_WDISn PCIE_SMB_DATA PCIE_SMB_CLK C30 0.1uF C31 330uF C32 330uF +3V3

## 3.6 Ethernet, USB

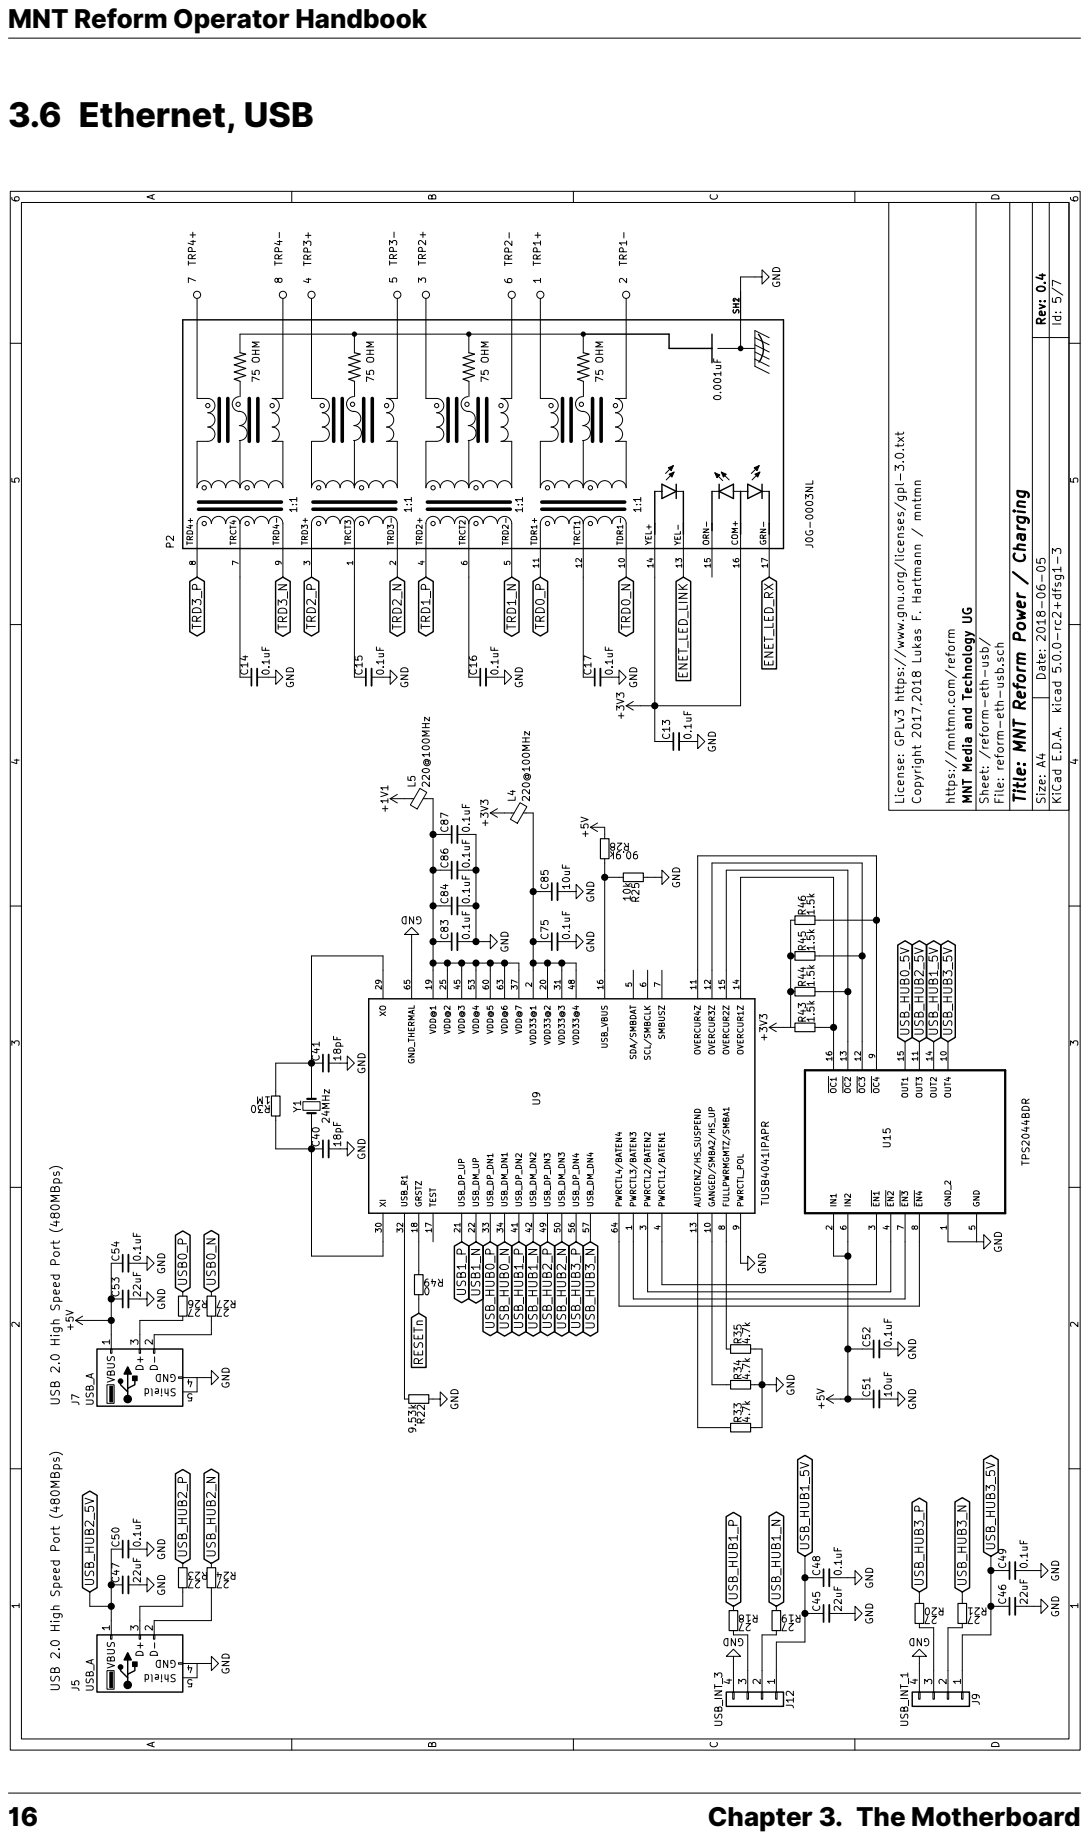
[picture p30: page 20]

D Date: 2018-06-05 KiCad E.D.A. kicad 5.0.0-rc2+dfsg1-3 Rev: 0.4 Size: A4 Id: 5/7 License: GPLv3 https://www.gnu.org/licenses/gpl-3.0.txt Copyright 2017,2018 Lukas F. Hartmann / mntmn https://mntmn.com/reform MNT Media and Technology UG Sheet: /reform-eth-usb/ File: reform-eth-usb.sch Title: MNT Reform Power / Charging VBUS

3 GND 4 Shield 5 J7USB_A 0.001uF 1 TRP1+ 1:1 1:1 1:1 1:1 7 TRP4+ 4 TRP3+ 5 TRP3- 3 TRP2+ 6 TRP2- 2 TRP1- 75 OHM 75 OHM 75 OHM 75 OHM 8 TRP4- TRD4+ TRCT4 TRD4- TRD3+ TRCT3 TRD3- TRD2+ TRCT2 TRD2- TDR1+ TRCT1 TDR1- YEL+ YEL- ORN- COM+ GRN-

1 J9 USB_INT_1 GND GND GND GND GND GND

9 GANGED/SMBA2/HS_UP 10 VDD33@2 20 XI 30 USB_DM_DN3 50 VDD@5 60 OVERCUR4Z 11 USB_DP_UP 21 VDD33@3 31 USB_DP_DN2 41 OVERCUR3Z 12 USB_DM_UP 22 USB_R1 32 USB_DM_DN2 42 AUTOENZ/HS_SUSPEND 13 USB_DP_DN1 33 VDD@4 53 VDD@6 63 OVERCUR1Z 14 USB_DM_DN1 34 PWRCTL4/BATEN4 64 OVERCUR2Z 15 VDD@2 25 VDD@3 45 GND_THERMAL 65 USB_VBUS 16 USB_DP_DN4 56 TEST 17 VDD@7 37 USB_DM_DN4 57 GRSTZ 18 VDD33@4 48 VDD@1 19 XO 29 USB_DP_DN3 49 U9 TUSB4041IPAPR GND C75 0.1uF GND +1V1 R22 9.53kGND

## 3.7 Audio

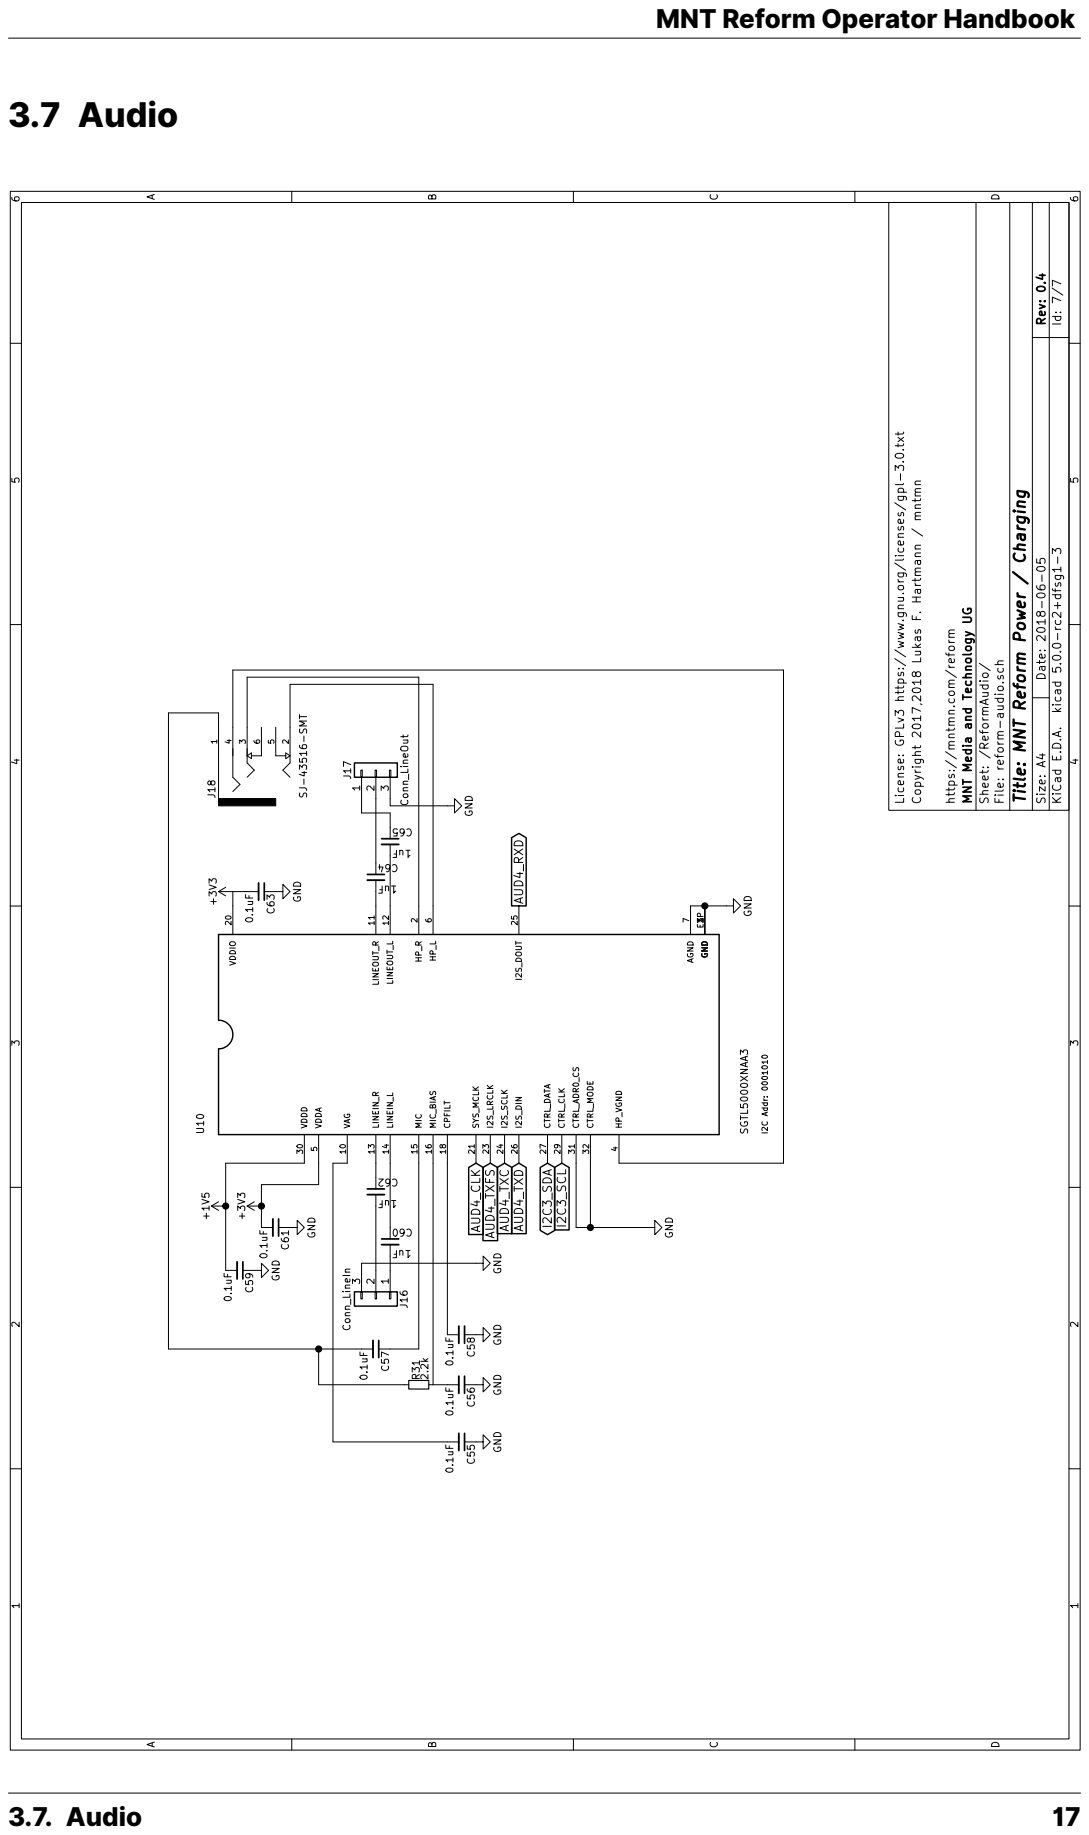
[picture p31: page 21]
3 HP_VGND; 4 VDDA; 6 AGND; 1 J16 Conn_LineIn; 2 J18SJ-43516-SMT; 3.7. Audio

D Date: 2018-06-05 KiCad E.D.A. kicad 5.0.0-rc2+dfsg1-3 Rev: 0.4 Size: A4 Id: 7/7 License: GPLv3 https://www.gnu.org/licenses/gpl-3.0.txt Copyright 2017,2018 Lukas F. Hartmann / mntmn https://mntmn.com/reform MNT Media and Technology UG Sheet: /ReformAudio/ File: reform-audio.sch Title: MNT Reform Power / Charging GND

3 J17 Conn_LineOut GND GND +1V5 +3V3 C58 0.1uF I2C Addr: 0001010

7 VAG 10 VDDIO 20 VDDD 30 LINEOUT_R 11 SYS_MCLK 21 CTRL_ADR0_CS 31 LINEOUT_L 12 CTRL_MODE 32 LINEIN_R 13 I2S_LRCLK 23 LINEIN_L 14 I2S_SCLK 24 MIC 15 I2S_DOUT 25 MIC_BIAS 16 I2S_DIN 26 CTRL_DATA 27 CPFILT 18 CTRL_CLK 29 GND EXP U10 SGTL5000XNAA3 AUD4_CLK AUD4_TXC AUD4_TXFS AUD4_TXD AUD4_RXD GND I2C3_SDA I2C3_SCL GND

### 18 Chapter 3. The Motherboard

CHAPTER

## FOUR

## THE BATTERY/LID CONTROLLER

## 4.1 Introduction

The Atmel ATTiny841 (U16) is a 8-bit microcontroller that uses very little power and is always on when there is battery power in the system. Its job is to keep track of how much current is going in and out of the battery and what voltage the battery has. It does this with the help of the voltage/current monitor chip INA260 that is connected to the ATTiny via I2C.
The ATTiny works as:
- Battery voltage and current monitor/gauge
- System current monitor
- Lid sensor

## 4.2 Communication

The ATTiny is permanently connected to the i.MX6 UART2 (/dev/ttymxc1 in Linux). If you want to interrupt this connection, you can desolder resistors R48 and R50.
The ATTiny firmware configures its serial port to 9600 baud 8N1. You can talk to it using the program screen (or another serial terminal):

screen /dev/ttymxc1 2400

It accepts commands in the form of a single letter followed by return. The current commands are:
- p: Get battery power information (estimated capacity in amp hours, voltage, current)
- l: Get lid state (0: open, 1: closed)
- h: Get hall sensor raw analog value
In addition, these commands can be prefixed with a decimal number (up to four digits):
- 600c: Reset the battery capacity counter to 10Ah (600 Amp minutes)
- 500t: Set the lid sensor open/closed threshold to the value 500
- 10w: Set the lid sensor open/closed hysteresis to 10

19

## 4.3 Undervoltage Protection (UVLO)

The microcontroller is supposed to detect a dangerously low voltage on the battery and switch the 5V boost converter off via its PWRON output when the voltage is below 2.8V. This way, the system will not draw power from the battery until it is charged to a reasonable level again. This functionality is still being tested and not activated in the beta boards.

## 4.4 Lid Sensor

The ATTiny senses if the lid is open or closed using the hall effect sensor (Honeywell SS495A). The lid is considered closed when a magnet is close to the sensor. The ATTiny outputs the string “wake” via its serial port which can wake the i.MX6 up from sleep.

## 4.5 Flashing the Firmware

You can find the source code of the firmware (https://github.com/mntmn/reform/reform-attiny-fw) in the folder “reform-attiny-fw” of the Reform source repository.
To change (flash) the firmware of the ATTiny, you need an Atmel ISP (In System Programmer) compatible programmer/cable. An easy way is to use an Arduino to emulate (https://www.arduino.cc/en/Tutorial/ArduinoISP) an ISP.
The relevant pins of J34 on the Reform motherboard for connecting the ISP cable are as follows:
Upper row (left to right):
7 | 5 | 3 | 1
GND | MOSI | MISO | SCK

Lower row (left to right):

8 | 6 | 4 | 2
RESET | None | None | None

### 20 Chapter 4. The Battery/Lid Controller

CHAPTER

## FIVE

## THE KEYBOARD

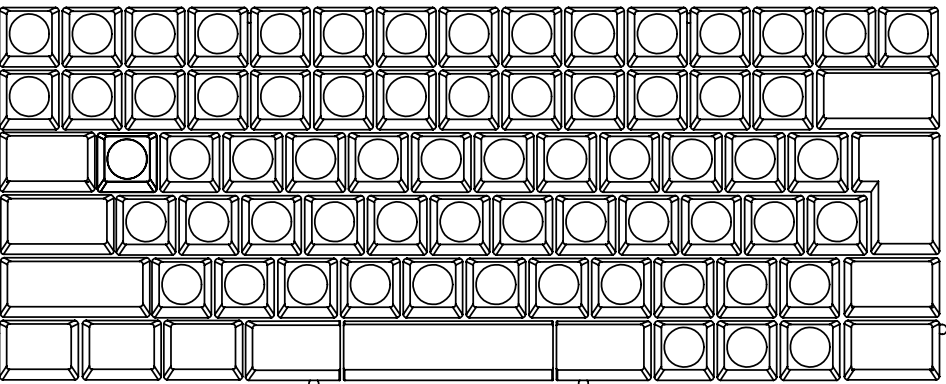
[picture p32: figure]

The keyboard is a row/column matrix scanner with anti-ghosting diodes on each switch. Each row and column is connected to one pin of the ATMega32U4 (http://ww1.microchip.com/downloads/en/DeviceDoc/Atmel-7766-8-bit-AVR-ATmega16U4-32U4_Datasheet.pdf) 8-bit microcontroller. This microcontroller runs a firmware based on LUFA. (http://www.fourwalledcubicle.com/files/LUFA/Doc/170418/html/) This converts the scanned out keycodes to the USB HID protocol.

## 5.1 Firmware

You can find the Reform keyboard firmware (https://github.com/mntmn/reform/reform-keyboard-fw) in the source folder “reform-keyboard-fw”. To modify the scancodes of the keyboard matrix, edit the file Keyboard.c and rebuild the firmware by typing the following command in a terminal:

make

To be able to flash the firmware to the keyboard, the ATMega has to be in a special mode where it identifies as an “Atmega DFU bootloader” USB device. This is achieved by shorting the pins HWB and GND with a jumper and then briefly shorting the RESET pin to ground.
The RESET pin is pin 2 of J1, pin 1 is GND.
HWB and GND are pins 3 and 4 of J3, respectively. Start counting at the “J3” label. The keyboard will reappear as a Atmel DFU bootloader USB device. You can then upload your new firmware by executing:

21

./flash.sh

## 5.2 Replacing a Keycap

The keycaps of the Reform beta units are printed with Clear Resin on Formlabs Form2 printers and then sanded by hand. Small irregularities are normal and a result of this process. The stems of the square 1x1 keycaps are slightly wider than the stems of other keycaps to make them more stable. This makes them harder to remove without breaking a stem. If a stem breaks inside of the keyswitch, you’ll have to replace the keyswitch (see the following section).
To pull out bigger keycaps, use pincers and try to push them between the top of the switch and the cap and wiggle very carefully and evenly until you can pull out the cap. There are some companies who produce “standard” Cherry ML keycaps, such as GMK. (https://www.gmk-electronic-design.de/en.html)

## 5.3 Replacing a Keyswitch

Only 2 of the 4 Cherry ML switch pins are soldered in to make it easier to swap switches with just a soldering iron. Set your iron/station to 380 degrees and dissolve the solder of one pin. Try to pull out the corresponding side of the switch from the top while continuing to heat the pin. Repeat the same for the other pin and go back and forth until you can remove the switch.
Replace with model Cherry ML1A-11JW.

### 22 Chapter 5. The Keyboard

## 5.4 Keyboard Schematics (Matrix)

1 2 3 4 5 6 7 8

1 2 3 4 5 6 7 8

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
F Date: 2018-11-11 KiCad E.D.A. kicad 5.0.0-rc2+dfsg1-3 Rev: 0.4 Size: A3 Id: 1/2 https://mntmn.com/reform Copyright 2017,2018 Lukas F. Hartmann / mntmn License: GPLv3+ https://www.gnu.org/licenses/gpl-3.0.en.html MNT Media and Technology UG Sheet: / File: mntcomp-keyboard.sch Title: Reform Keyboard SW1 ML SW2 ML D1D_Small D2D_Small SW3 ML SW4 ML D3D_Small D4D_Small SW5 ML SW6 ML D5D_Small D6D_Small SW7 ML SW8 ML D7D_Small D8D_Small SW9 ML SW10 ML D9D_Small D10 D_Small SW11 ML SW12 ML D11 D_Small D12 D_Small SW13 ML SW14 ML D13 D_Small D14 D_Small SW16 ML SW17 ML D16 D_Small D17 D_Small SW18 ML SW19 ML D18 D_Small D19 D_Small SW20 ML SW21 ML D20 D_Small D21 D_Small SW22 ML SW23 ML D22 D_Small D23 D_Small SW24 ML SW25 ML D24 D_Small D25 D_Small SW26 ML SW27 ML D26 D_Small D27 D_Small SW28 ML D28 D_Small SW30 ML SW31 ML D30 D_Small D31 D_Small SW32 ML SW33 ML D32 D_Small D33 D_Small SW34 ML SW35 ML D34 D_Small D35 D_Small SW36 ML SW37 ML D36 D_Small D37 D_Small SW38 ML SW39 ML D38 D_Small D39 D_Small SW40 ML SW41 ML D40 D_Small D41 D_Small SW42 ML SW43 ML D42 D_Small D43 D_Small SW44 ML SW45 ML D44 D_Small D45 D_Small SW46 ML SW47 ML D46 D_Small D47 D_Small SW48 ML SW49 ML D48 D_Small D49 D_Small SW50 ML SW51 ML D50 D_Small D51 D_Small SW52 ML SW53 ML D52 D_Small D53 D_Small SW54 ML SW55 ML D54 D_Small D55 D_Small SW56 ML D56 D_Small SW57 ML SW58 ML D57 D_Small D58 D_Small SW59 ML SW60 ML D59 D_Small D60 D_Small SW61 ML SW62 ML D61 D_Small D62 D_Small SW63 ML SW64 ML D63 D_Small D64 D_Small SW65 ML SW66 ML D65 D_Small D66 D_Small SW67 ML SW68 ML D67 D_Small D68 D_Small SW69 ML D69 D_Small SW70 ML SW71 ML D70 D_Small D71 D_Small SW72 ML SW73 ML D72 D_Small D73 D_Small SW74 ML SW75 ML D74 D_Small D75 D_Small SW76 ML SW77 ML D76 D_Small D77 D_Small D29 D_Small SW29 ML SW15 ML D15 D_Small Reform KBD MCU reform-kbd-mcu.sch ROW1 ROW2 ROW3 ROW4 ROW5 ROW6
5.4. Keyboard Schematics (Matrix) | 23

## 5.5 Keyboard Schematics (Controller)

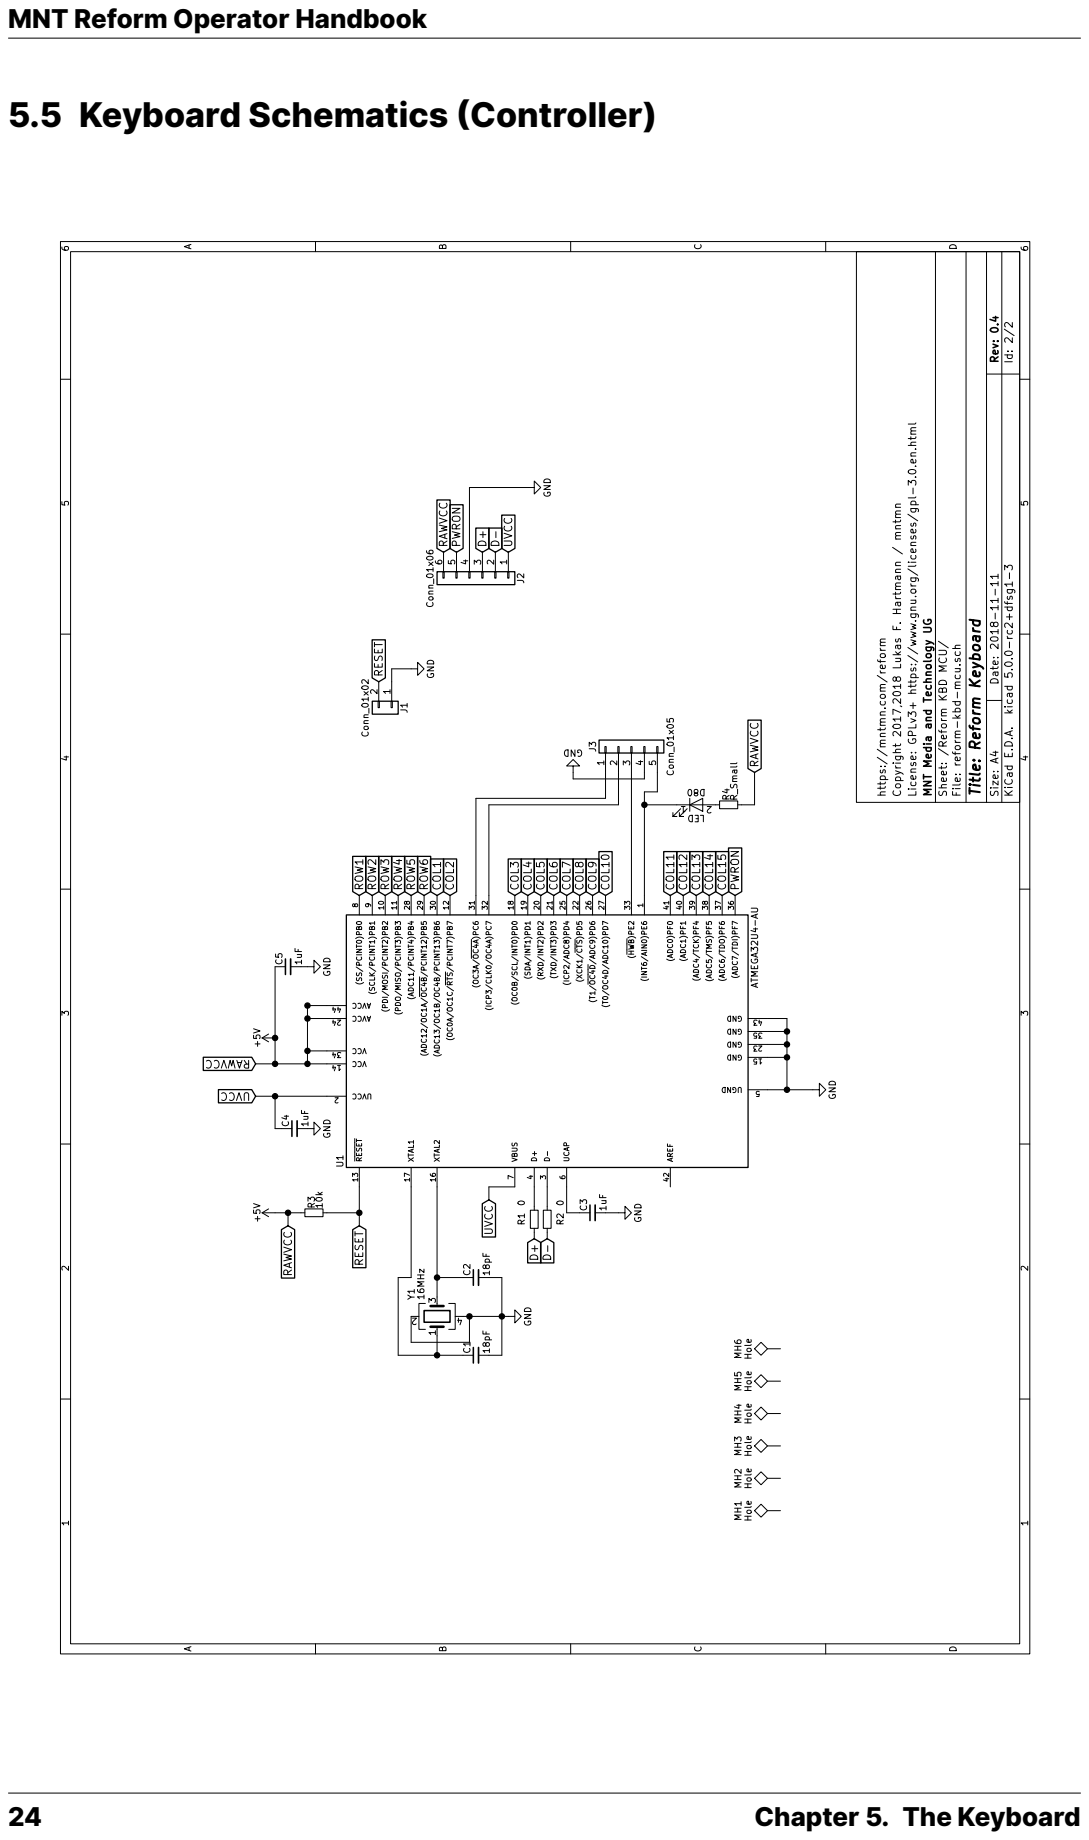
[picture p33: page 28]

D Date: 2018-11-11 KiCad E.D.A. kicad 5.0.0-rc2+dfsg1-3 Rev: 0.4 Size: A4 Id: 2/2 https://mntmn.com/reform Copyright 2017,2018 Lukas F. Hartmann / mntmn License: GPLv3+ https://www.gnu.org/licenses/gpl-3.0.en.html MNT Media and Technology UG Sheet: /Reform KBD MCU/ File: reform-kbd-mcu.sch Title: Reform Keyboard GND C118pF C218pF GND C3 1uF UVCC GND PWRON D+D- UVCC D+D-

1 J2 Conn_01x06 RAWVCC R2 0 R1 0 RAWVCC C4 1uF C5 1uF GND GND MH1 Hole MH2 Hole MH3 Hole MH4 Hole +5V +5VR310k 1

9 (PDI/MOSI/PCINT2)PB2 10 (RXD/INT2)PD2 20 (ADC13/OC1B/OC4B/PCINT13)PB6 30 (ADC1)PF1 40 (PDO/MISO/PCINT3)PB3 11 (TXD/INT3)PD3 21 (OC3A/OC4A)PC6 31 (ADC0)PF0 41 (OC0A/OC1C/RTS/PCINT7)PB7 12 (XCK1/CTS)PD5 22 (ICP3/CLK0/OC4A)PC7 32 AREF 42 RESET 13 GND 23 (HWB)PE2 33 GND 43 VCC 14 AVCC 24 VCC 34 AVCC 44 GND 15 (ICP2/ADC8)PD4 25 GND 35 XTAL2 16 (T1/OC4D/ADC9)PD6 26 (ADC7/TDI)PF7 36 XTAL1 17 (T0/OC4D/ADC10)PD7 27 (ADC6/TDO)PF6 37 (OC0B/SCL/INT0)PD0 18 (ADC11/PCINT4)PB4 28 (ADC5/TMS)PF5 38 (SDA/INT1)PD1 19 (ADC12/OC1A/OC4B/PCINT12)PB5 29 (ADC4/TCK)PF4 39 U1 ATMEGA32U4-AU PWRON RAWVCC

CHAPTER

## SIX

## THE TRACKBALL

The trackball uses the same microcontroller and LUFA framework as the keyboard, but instead of scanning a matrix of switches, it gets X and Y movement coordinates from the PMW3360DM-T2QU optical sensor that is connected via SPI.

## 6.1 Wheel Mode, Middle Click

The trackball firmware has a special “wheel mode” that allows you to use it like a mouse wheel for scrolling or to perform a middle mouse click.
You can enter wheel mode by pressing the left button and then pressing the right button while keeping the left button pressed. Release both buttons. Rolling the ball up and down will send wheel up/down commands. Clicking the right button will perform a middle click. Clicking the left button will exit wheel mode.

25

## 6.2 Firmware

You can find the Reform trackball firmware (https://github.com/mntmn/reform/reform-trackball-fw) in the source folder “reform-trackball-fw”. The trackball firmware is based on the LUFA USB device library and implements a USB HID Mouse. To modify the behaviour of the trackball, edit the file Mouse.c and rebuild the firmware by typing the following command in a terminal:

make

As with the keyboard, the trackball’s MCU has to be in “Atmega DFU bootloader” USB mode. This is achieved by shorting the pins HWB and GND with a jumper and then briefly shorting the RESET pin to ground. The pins are marked on the silkscreen of the main trackball PCB.
After a reset with HWB pulled to ground, The trackball will reappear as a Atmel DFU bootloader USB device. You can then upload your new firmware by executing:

./flash.sh

### 26 Chapter 6. The Trackball

## 6.3 Schematics

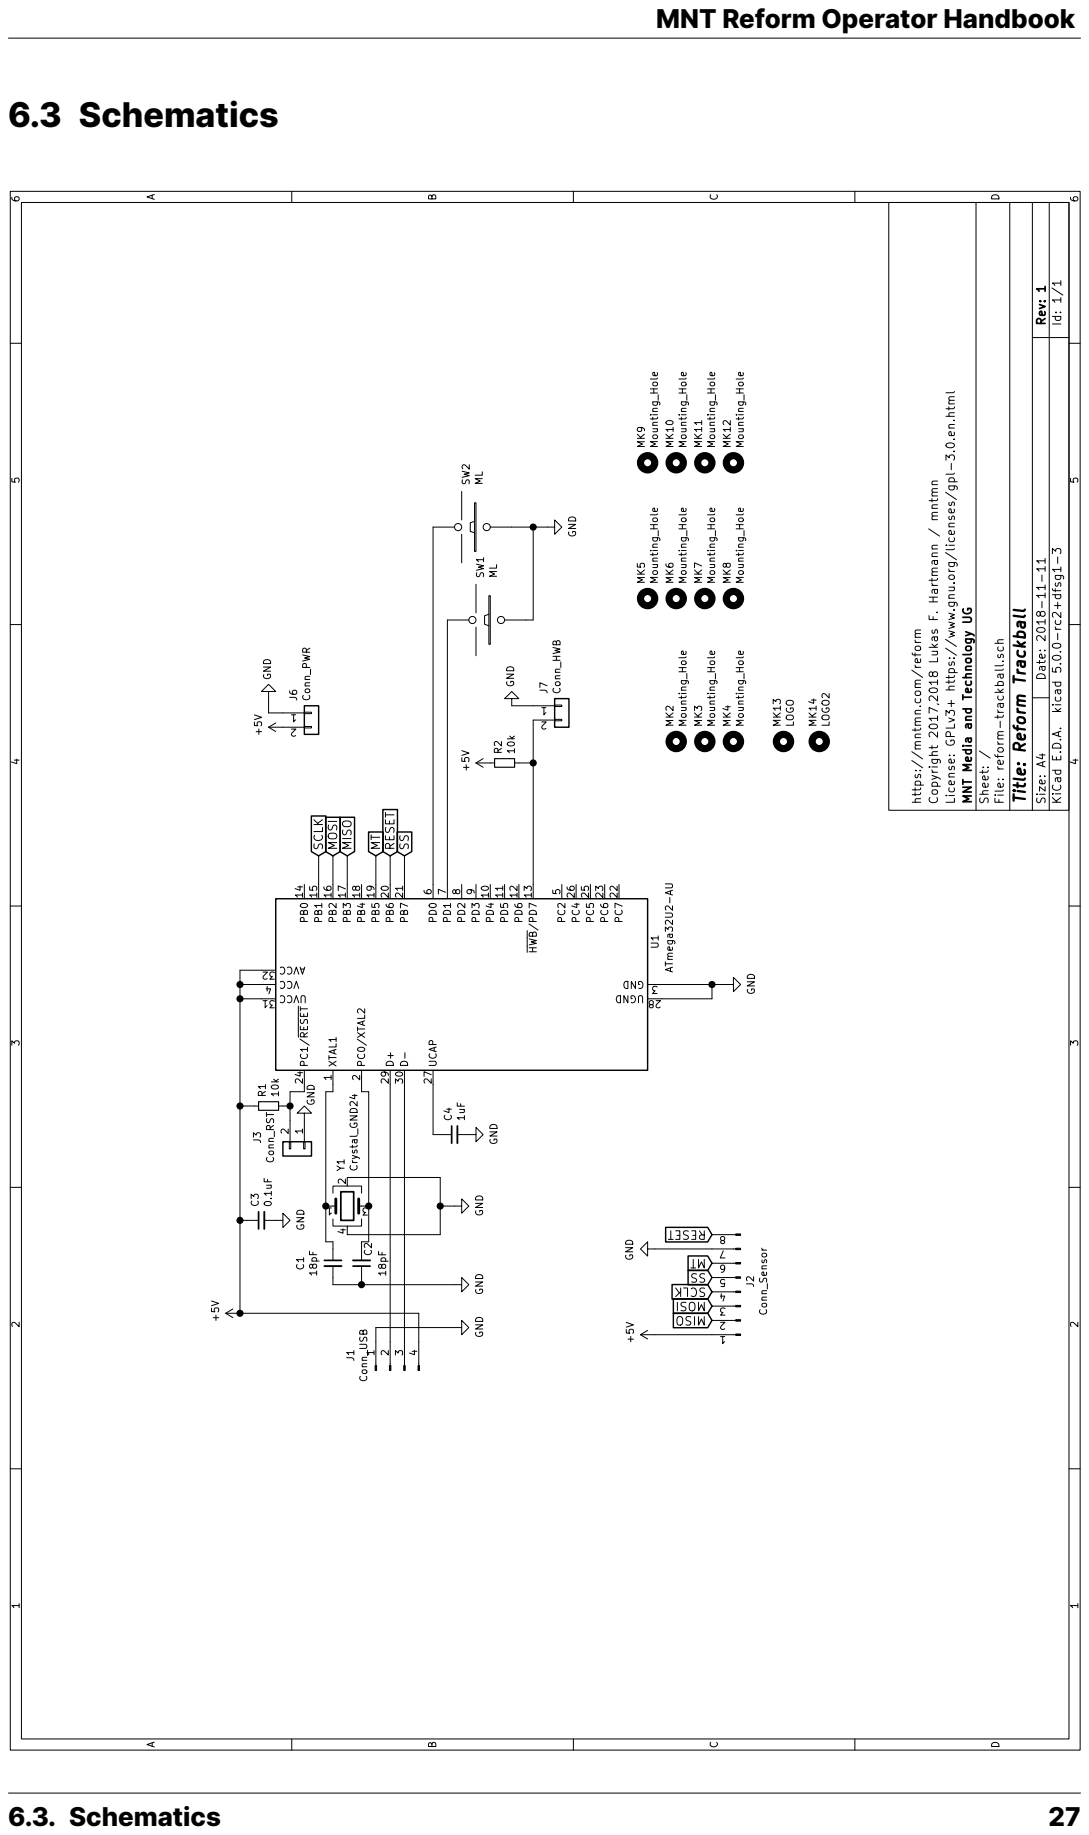
[picture p34: page 31]
1 PD4 10 PD5 11 PD6 12 HWB/PD7 13 PB0 14 PB1 15 PB2 16 PB3 17 PB4 18 PB5 19 PC0/XTAL2 5 PD0; 4J1 Conn_USBGND 1; 1 J3 Conn_RST GNDR110k 1; 4 Y1Crystal_GND24 GND MK13 LOGO MK14 LOGO2; 6.3. Schematics

D Date: 2018-11-11 KiCad E.D.A. kicad 5.0.0-rc2+dfsg1-3 Rev: 1 Size: A4 Id: 1/1 https://mntmn.com/reform Copyright 2017,2018 Lukas F. Hartmann / mntmn License: GPLv3+ https://www.gnu.org/licenses/gpl-3.0.en.html MNT Media and Technology UG Sheet: / File: reform-trackball.sch Title: Reform Trackball XTAL1

9 U1 ATmega32U2-AU SW1 ML SW2 ML GND GND

2 PB6 20 PB7 21 PC7 22 PC6 23 PC1/RESET 24 PC5 25 PC4 26 UCAP 27 UGND 28 D+ 29 GND 3 D- 30 UVCC 31 AVCC 32 VCC 4 PC2

### 28 Chapter 6. The Trackball

CHAPTER

## SEVEN

## THERMAL

The main source of heat inside Reform is the i.MX6 SoC and its memory chips. Most of the heat goes into the blue passive heatsink that is glued to it. A fan which is mounted to the bottom plate then blows air over the heatsink into the direction of the ports, where it can escape through gaps in the case.
The fan is needed to push hot air out of the case, preventing overheating of the system. Normally, its full power is only needed when the system is under heavy load, for example when the GPU (3D graphics processor) is very active or all 4 cores are busy compiling code. The fan should turn on to full power when the SoC temperature is over 65 degrees celcius.
One of the three fan cables (orange) connects to the PWM1 pin of the i.MX6. The fan’s speed can be controlled via pulse width modulation. This is usually the job of the reformd script, which monitors the core temperature and sets the fan to full power when the temperature is over 65 degrees Celcius.
To check the temperature of the system, you can use the command:

cat /sys/class/thermal/thermal_zone0/temp

The following is an example of commands that reformd uses to change the fan speed (in this instance, to set it to 75%):

# make the first PWM device available

echo 0 > /sys/class/pwm/pwmchip1/export
# define what a full period is

echo 10000 > /sys/class/pwm/pwmchip1/pwm0/period
# set how much of this period should be in the "ON" state (75%) echo 7500 > /sys/class/pwm/pwmchip1/pwm0/duty_cycle

# enable the PWM output

echo 1 > /sys/class/pwm/pwmchip1/pwm0/enable

29

### 30 Chapter 7. Thermal

CHAPTER

## EIGHT

## SYSTEM BOOT DETAILS

## 8.1 Powering Up

When the power switch is turned on, the TinyRex module (the little red board that contains the i.MX6 and the memory chips) receives power. If it is happy with the applied voltages (POWEROK signals are present), the green LED on the TinyRex module will light up. If only the red LED lights up, there is a problem with the power supply.
Next, the i.MX6 chip will jump to internal boot ROM code at memory address 0x00000000. The boot ROM looks for an SD card on port SD1 and reads the DCD (Device Configuration Data) table from physical address 0x400 (1024 decimal, or the second physical block) on the SD card. This means that you can only use the MBR partition scheme on the boot disk, as it only occupies the first disk block. The more modern GPT partition format could work in theory, but most GPT tools and parsers do not understand GPT structures where the second block is in an alternative location.
We recommend to use the SD card as a boot and rescue disk, and set up an mSATA SSD disk with your actual operating system and data. You can then use alternative partition schemes and encryption.
Reform ships with U-Boot. It is installed onto the SD card and includes the DCD block that configures the DDR memory parameters and clocks.

## 8.2 U-Boot

U-Boot is a mini operating system and shell that allows you to inspect parts of the system (like PCIe, USB devices and Harddisks) and set up parameters to be passed to a “big” operating system kernel such as Linux, and start such an operating system.
U-Boot itself has to be compiled with the board support files for Reform. This is done by mkuboot.sh. The resulting file is u-boot.imx.
U-Boot is installed to the second block of the SD card using the “dd” utility by mkreform.sh.
U-Boot needs 2 files to boot Linux:
- The Linux kernel itself, normally called “zImage”.

31

- The device tree blob (DTB), normally called “imx6qp-mntreform.dtb”. It is a data structure that lists the addresses of and parameters for all the devices in the system that Linux needs to drive.
Both files are created when building Linux from source with the “imx6qp-mntreform.dts” source file included in the kernel tree. The helper script mkkernel.sh from https://github.com/mntmn/reform-bootstrap (https://github.com/mntmn/reform-bootstrap) does it for you.

## 8.3 Booting the Linux Kernel

Theoretically, you could boot other operating systems besides Linux, such as FreeBSD, NetBSD, OpenBSD or anything else that supports the i.MX6QP SoC. So far, we didn’t have the time to test them, though. We’ll happily expand this guide with your contributions if you’ve managed to run an alternative OS on Reform.
The default boot commands for U-Boot are specified at https://github.com/mntmn/u-boot/blob/mntreform/include/configs/mntreform.h#L104 (https://github.com/mntmn/u-boot/blob/mntreform/include/configs/mntreform.h#L104)
If you want to boot manually, these are the steps.
1. Configure the kernel command line to use no initial ram disk, use the first partition of the first SD card as the root volume (read/write), and wait for the root device. Also, set the continuous memory allocation (CMA) pool to 256MB and disable message signaled interrupts (MSI) for PCI express. The CMA pool is needed by the etnaviv GPU drivers. MSI has to be disabled for some expansions like ath9k-based WiFi cards.

setenv bootargs noinitrd root=/dev/mmcblk0p1 rw rootwait cma=256M pci=nomsi no_ ,→console_suspend=1

2. Set the maximum address/size for the device tree structure (called FDT in U-Boot, DTS/DTB in Linux). The kernel can fail to start without this.

setenv fdt_high 0xffffffff

3. Load the Kernel (zImage) to address 0x10008000 from the SD card (also called “MMC”) device 0, partition 1 (there is no partition 0, 1 is the first). ext4load works for ext4 formatted partitions. For FAT, you would use fatload.

ext4load mmc 0:1 0x10008000 zImage

4. Load the device tree (FDT/DTB) to address 0x18000000 from the same partition.

ext4load mmc 0:1 0x18000000 imx6qp-mntreform.dtb

5. Tell U-Boot where you just loaded the FDT and to please resize it.

fdt addr 0x18000000
fdt resize
6. Start Linux from the load address and pass the FDT address to it.

bootz 0x10008000 - 0x18000000

### 32 Chapter 8. System Boot Details

CHAPTER

## NINE

## DEBUGGING

## 9.1 Power

The TinyRex module has a red and a green LED. Both have to light up to signal good power.
To troubleshoot power, disconnect the internal battery and all internal and external peripherals, connect the 5V wall adapter. If you want to unplug the TinyRex module, you should take the motherboard out of the case first.
Turn the power switch on. Get a multimeter and find the following voltages in the system:
- 5V The main input rail. Can be found on pin 1 of J25 or J29.
- 3.3V The big regulator U4 (AP1501A-33) turns 5V into 3.3V. Check test point TP3 next to the big coil L2.
- 2.5V Regulated by U11 (LP3962EMP-2.5). Check TP5 next to it.
- 1.5V Regulated by U13. Check TP12. Needed for PCIe.
- 1.1V Regulated by U5 near the USB hub U9. Check TP6.
If voltages are way off, there can be a short somewhere on the board which usually generates heat.

## 9.2 Serial Console

The motherboard connector labelled CONSOLE is a serial port (UART) to which U-Boot and the Linux kernel output diagnostic information on startup. The baud rate is 115200. Wire up a generic USB-to-UART adapter to the following pins of J25 (pin 1 is next to the J25 label):
- 1 5V, don’t connect
- 2 UART1_TXD, connect to RX of your adapter
- 3 UART1_RXD, connect to TX of your adapter
- 4 UART1_RTS, don’t connect
- 5 UART1_CTS, don’t connect
- 6 GND, connect to GND of your adapter

33

Then, use a terminal program such as screen on your host computer:

screen /dev/ttyUSB0 115200

If you then switch on Reform with a prepared SD card inserted, you should see the U-Boot console in screen.

### 34 Chapter 9. Debugging

CHAPTER

## TEN

## CREDITS

Concept, Electronics, Software, Manual, Assembly Lukas F. Hartmann (mntmn)
Industrial Design Ana Beatriz Albertini Dantas
Sleeve Design, Assembly Greta Melnik
Special Thanks FabLab Berlin, Neuform, CCC Berlin/n-te, Fedevel/Voipac, etnaviv, Xorg, Mesa, wayland, Igalia, heise/Make Germany/Helga Hansen, Philip Steffan, Maker Faire Berlin, Interface Critique/Florian Hadler, Gabriel Yoran, JD Music Labs, Crowd Supply, malcolmputer, zakx, darthrake, erlehmann, plomlompom, scallo, dridde, grncdr, oomono, Daniel Stone, Martin Meyerhoff, Gregor May, Chris Healy, Martin Borgert, Stephan Urbach, furan, Radoslaw Kujawa, Novena, Mastodon, a1k, Disko Koenig, S.I.H., The Reform Beta Testers (you!)
Inter UI Font rsms
PCB Production PCBWay
Aluminum Milling Shandong Jiepurui Model Technology Co., Ltd. 3D Printer BCN3D Sigma R17
Reflow Oven ReflowR
Stereolitography Formlabs Form2
Lab Tools Rigol DS1054Z, Fluke 117. Weller WD-1, Toolcraft SMD Rework Station
Parts Suppliers Mouser, DigiKey, Conrad, Voelkner (Fans), GMK Electronic Design (Switches), Schraubenhandel Machholz (Screws), Smooth Group (Hinges), Palm Stream International (Displays), HereWin (Batteries)
Chips Used NXP | (MCIMX6Q5EYM10AC, | SGTL5000XNAA3), | Mi-
cron (MT41K512M16HA-125), Texas Instruments (BQ24650RVAT,
INA260AIPW, | TPS61235RWLR, | TUSB4041IPAPR, | TPS2044BDR,
TLV70012, TLV1117-15, LP3962EMP-2.5), ON Semiconductor (CM2020-00TR), Microchip (KSZ9031RNXIA, ATTINY841-SSU, ATMEGA32U4), Diodes Inc. (AP1501A-33K5G-13), Rohm (BR24L02NUX-WTR) Software Used Debian GNU/Linux, KiCAD, Inkscape, GIMP, Emacs, Vim, Git, Arduino, LUFA, Blender, Cura, slic3r, Solidworks, FreeCAD, OpenSCAD, Sphinx

35

Web: https://mntmn.com/reform Email: lukas@mntmn.com Copyright 2018 MNT Media and Technology UG (haftungsbeschränkt), Bluecherstr. 32C, 10961 Berlin Managing Director: Lukas F. Hartmann Registergericht: Amtsgericht Charlottenburg Aktenzeichen: HRB 136605 B VAT ID: DE278908891 WEEE: DE 33315564
This book is licensed under GPLv3 or newer.

### 36 Chapter 10. Credits
