milestogo/reform/historic-reform1/handbook/source/case/reform-caseparts.jpg

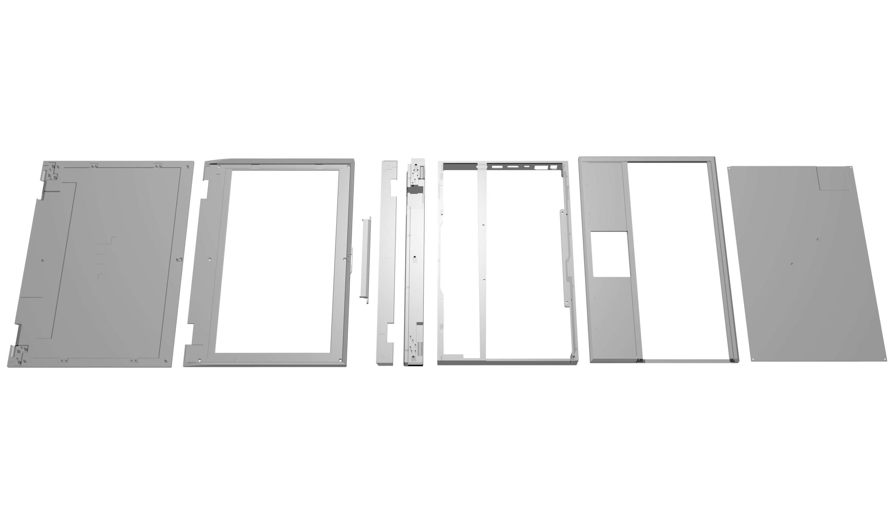
historic-reform1/handbook/source/case/reform-caseparts.jpg
