milestogo/reform/historic-reform1/handbook/source/keyboard/reform04-kbdpcb.png

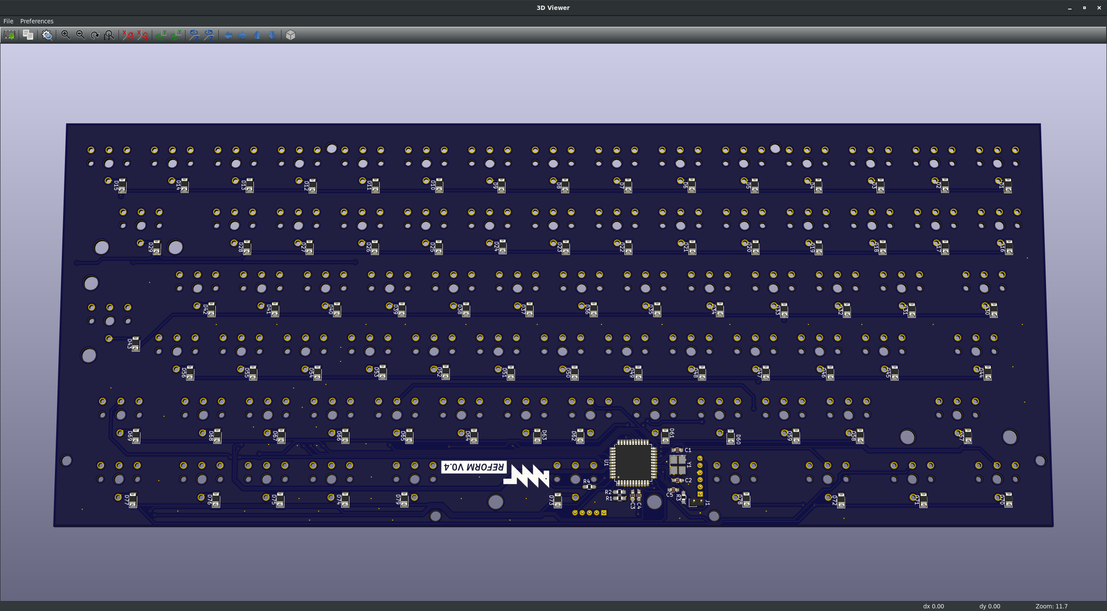
historic-reform1/handbook/source/keyboard/reform04-kbdpcb.png
