milestogo/reform/historic-reform1/handbook/source/motherboard/reform04-motherboardpcb-crop.png

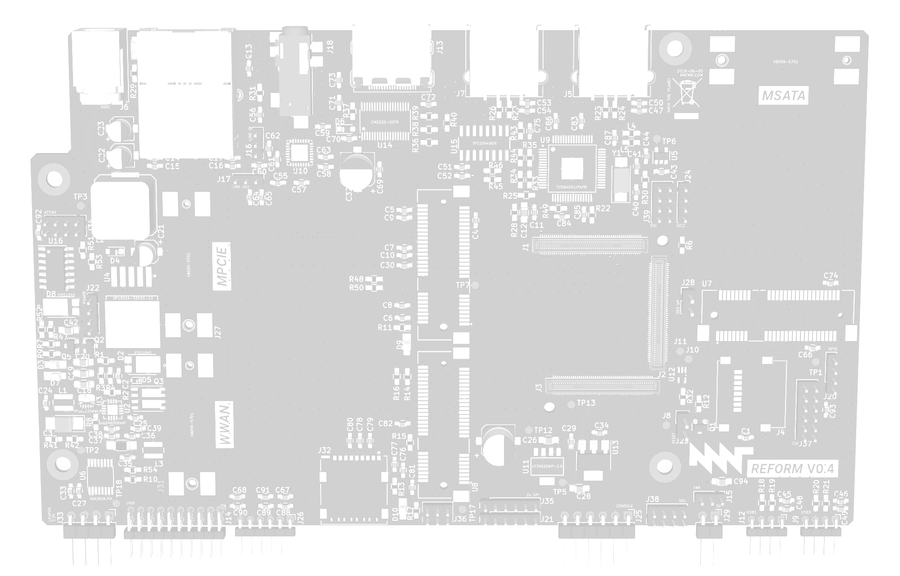
historic-reform1/handbook/source/motherboard/reform04-motherboardpcb-crop.png
