milestogo/reform/historic-reform1/handbook/source/motherboard/reform04-motherboardpcb.png

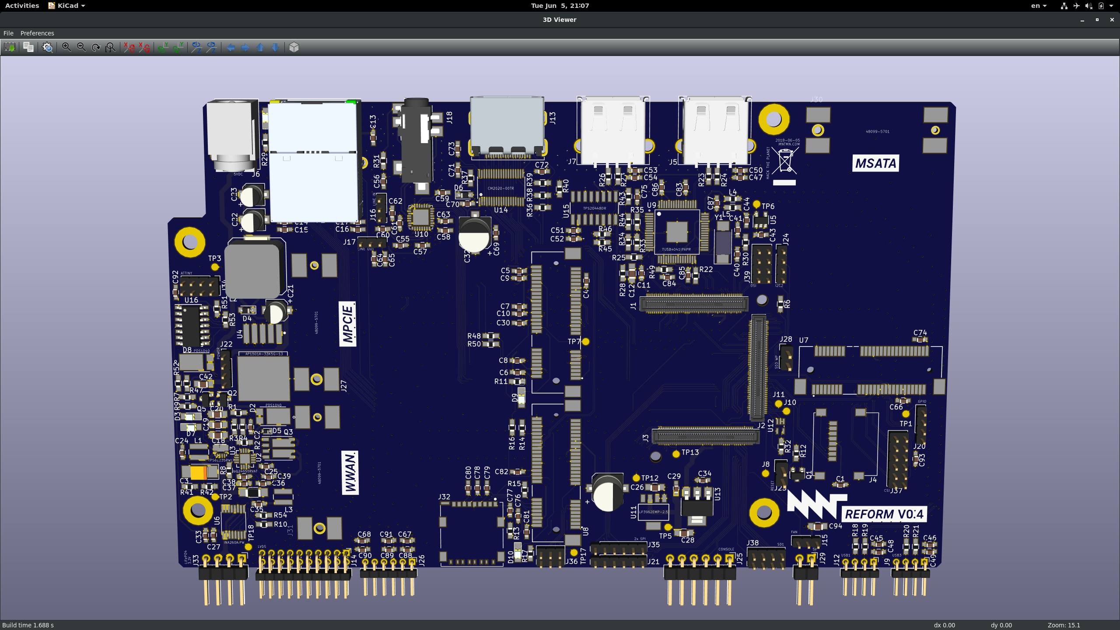
historic-reform1/handbook/source/motherboard/reform04-motherboardpcb.png
