milestogo/reform/historic-reform1/handbook/source/reform-title.png

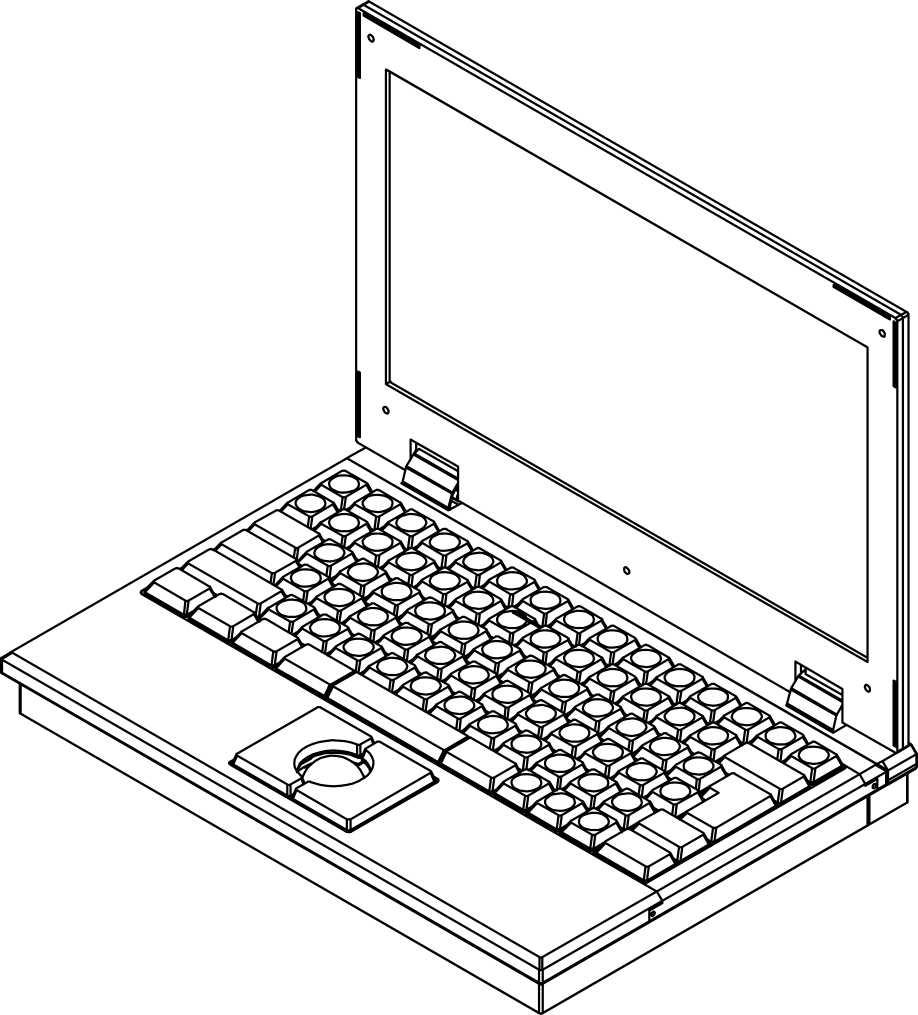
historic-reform1/handbook/source/reform-title.png
