milestogo/reform/historic-reform1/pics/reform03-laptop.jpg

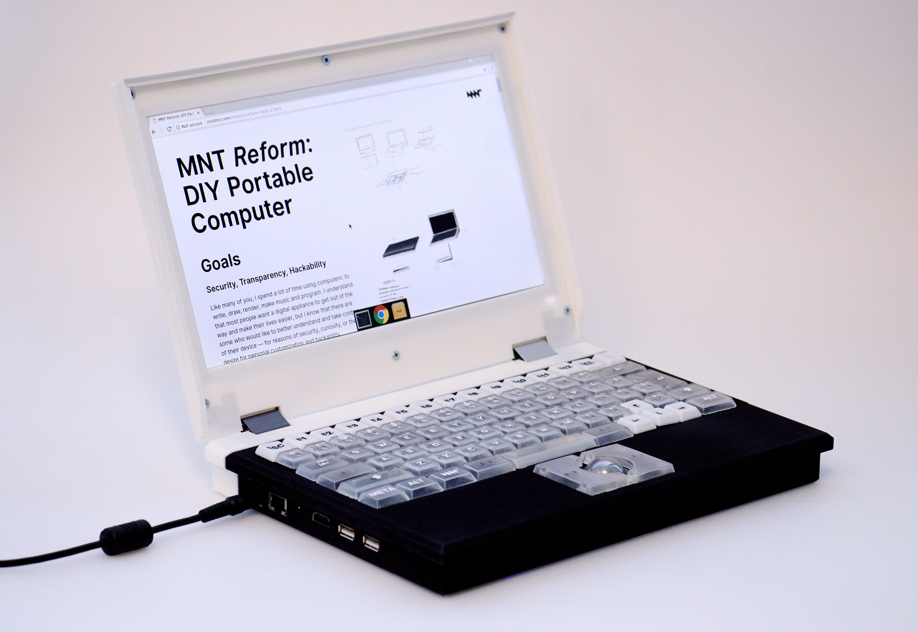
historic-reform1/pics/reform03-laptop.jpg
