milestogo/reform/reform2-3d-printed-parts/trackpad/reform2-trackpad-support-20201005.stl

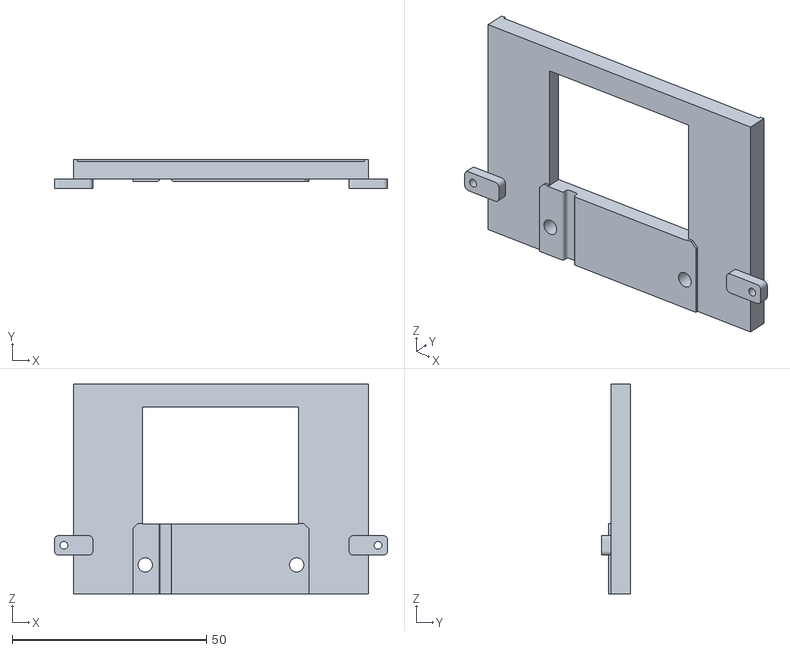
[picture p70: CAD file, 2020-10-28]
reform2-3d-printed-parts/trackpad/reform2-trackpad-support-20201005.stl
85.8 x 7.44 x 54.0
