milestogo/reform/reform2-batterypack-pcb/3d-models/KEYSTONE 54 A.step

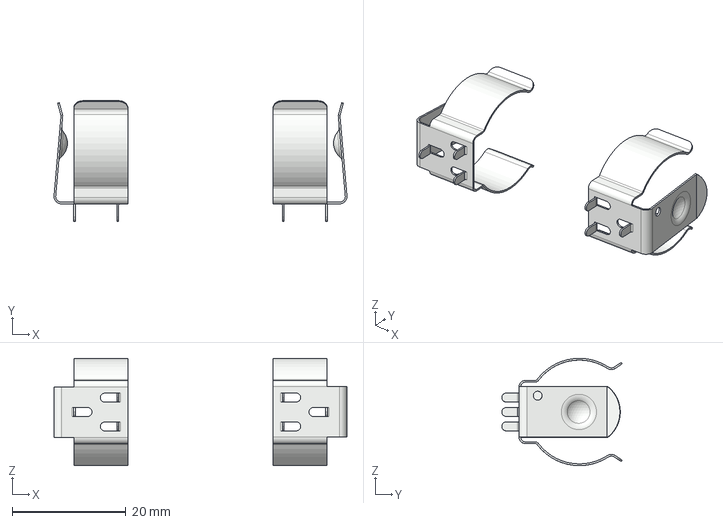
[picture p71: CAD file, 2020-04-11]
reform2-batterypack-pcb/3d-models/KEYSTONE 54 A.step
51.6 x 21.2 x 18.9 mm
KEYSTONE 54 x 2
