milestogo/reform/reform2-case-cnc/reform2-beta-2d4/bottom closing_25.02.20.step

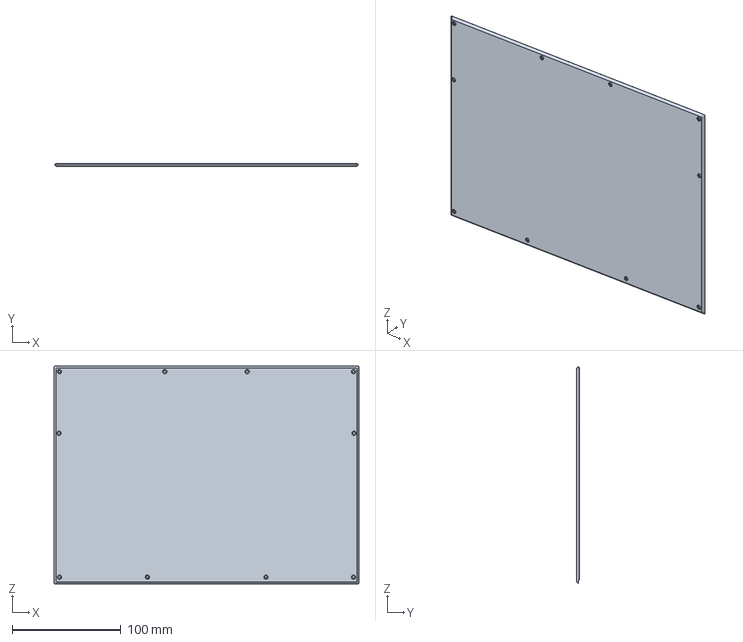
[picture p72: CAD file, 2020-04-11]
reform2-case-cnc/reform2-beta-2d4/bottom closing_25.02.20.step
280.0 x 3.00 x 200.0 mm
