milestogo/reform/reform2-keyboard-pcb/3d-models/srp4020.stp

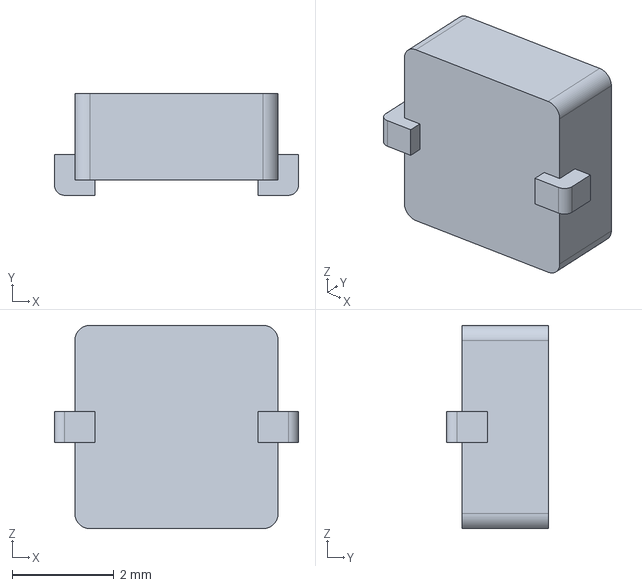
[picture p73: CAD file, 2020-08-14]
reform2-keyboard-pcb/3d-models/srp4020.stp
4.80 x 2.00 x 4.00 mm
