milestogo/reform/reform2-keyboard-pcb/reform2-kbdtest.stl

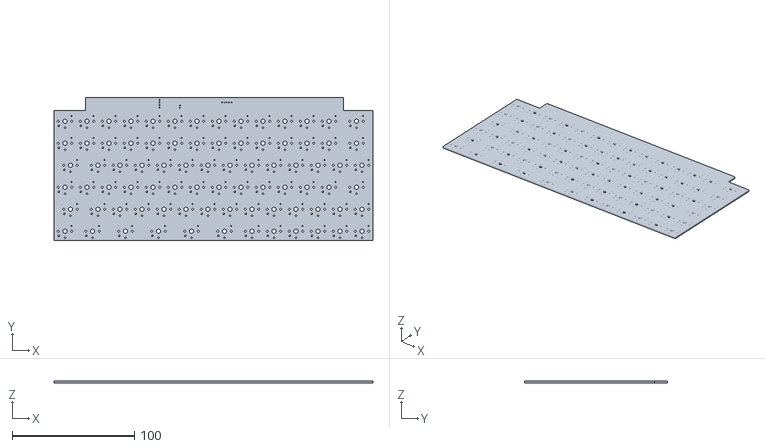
[picture p74: CAD file, 2020-04-11]
reform2-keyboard-pcb/reform2-kbdtest.stl
261.0 x 116.8 x 1.60
