milestogo/reform/reform2-motherboard-pcb/3d-models/SP3012-06UTG.stp

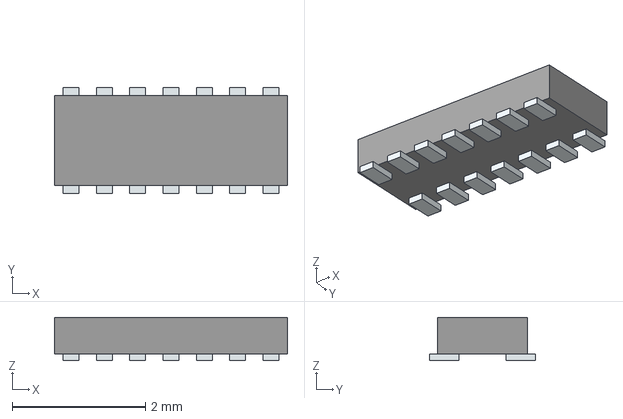
[picture p75: CAD file, 2020-10-29]
reform2-motherboard-pcb/3d-models/SP3012-06UTG.stp
3.50 x 1.59 x 0.65 mm
Pins
