milestogo/reform/reform2-oled-pcb/KiCad-SSD1306_OLED-0.91-128x32/SSD1306_OLED-0.91-128x32.step

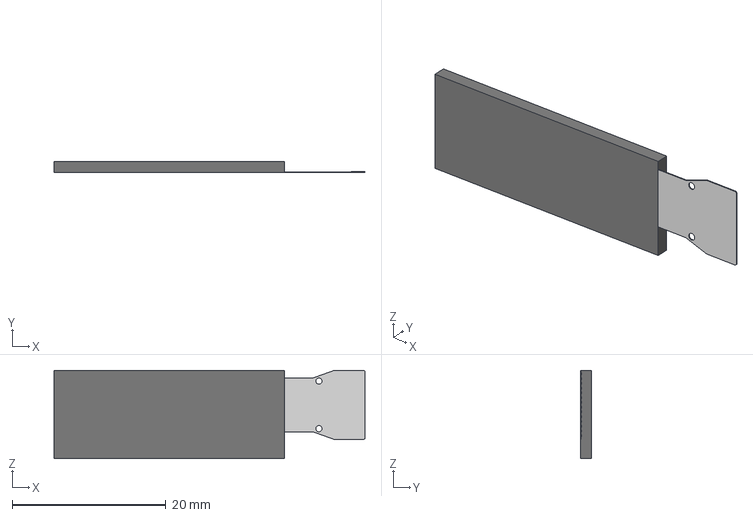
[picture p76: CAD file, 2020-11-24]
reform2-oled-pcb/KiCad-SSD1306_OLED-0.91-128x32/SSD1306_OLED-0.91-128x32.step
40.5 x 1.45 x 11.5 mm
