milestogo/reform/reform2-speakers/reform2-speaker-spacer.stl

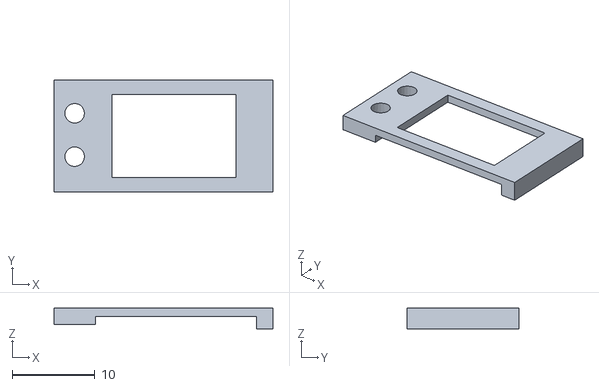
[picture p77: CAD file, 2020-05-20]
reform2-speakers/reform2-speaker-spacer.stl
26.5 x 13.5 x 2.50
