milestogo/reform/reform2-trackball-pcb/3d-models/off/Kailh_keycap-switch_system_1x1.step

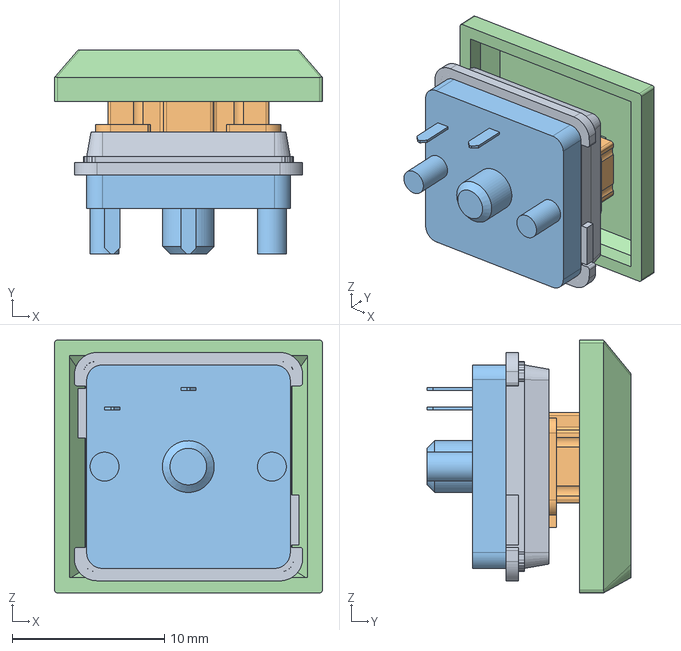
[picture p78: CAD file, 2020-04-11]
reform2-trackball-pcb/3d-models/off/Kailh_keycap-switch_system_1x1.step
17.6 x 13.4 x 16.6 mm
CPG135001D02 BROWN
Kailh_keycap
