milestogo/reform/historic-reform1/keycaps/big shift_final.STL

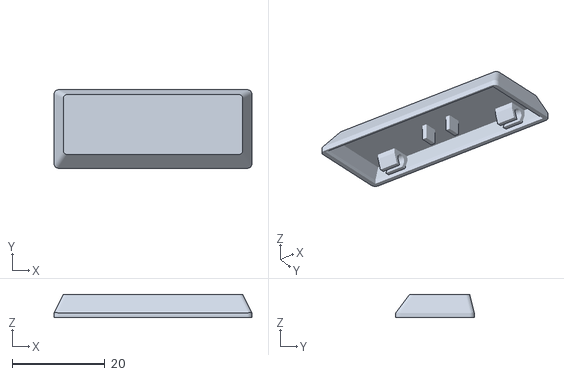
[picture p79: CAD file, 2018-11-12]
historic-reform1/keycaps/big shift_final.STL
42.8 x 17.0 x 5.00
