milestogo/reform/historic-reform1/reform-trackball-pcb/dxf/reform-trackball-F.CrtYd.dxf

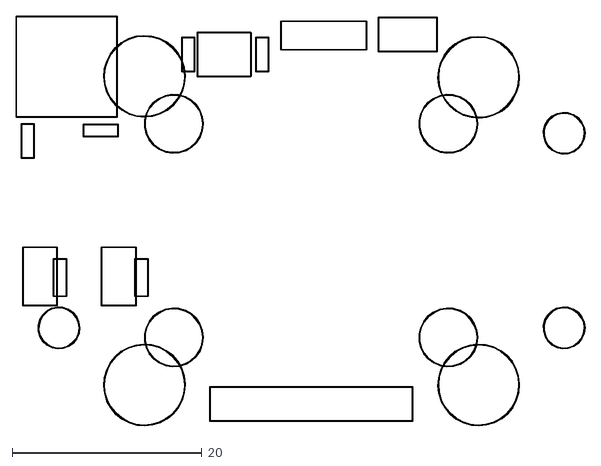
[picture p80: CAD file, 2018-11-12]
historic-reform1/reform-trackball-pcb/dxf/reform-trackball-F.CrtYd.dxf
59.9 x 43.1
