milestogo/reform/historic-reform1/reform-trackball-pcb/pcb tracking ball.DXF

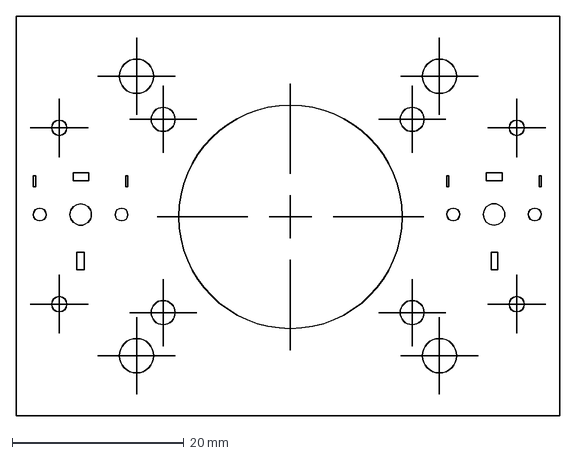
[picture p81: CAD file, 2018-11-12]
historic-reform1/reform-trackball-pcb/pcb tracking ball.DXF
63.3 x 46.5 mm
