milestogo/reform/historic-reform1/trackball-parts/trackball_right_button.STL

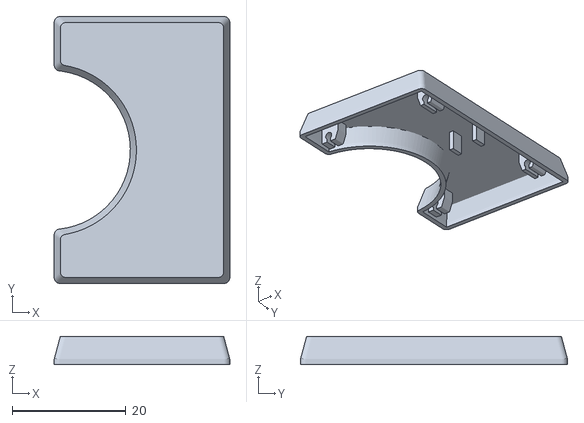
[picture p82: CAD file, 2018-11-12]
historic-reform1/trackball-parts/trackball_right_button.STL
30.9 x 47.0 x 5.00
