milestogo/reform/reform2-3d-printed-parts/historic-reform2-stl-2d4/circular round button 20200123.stl

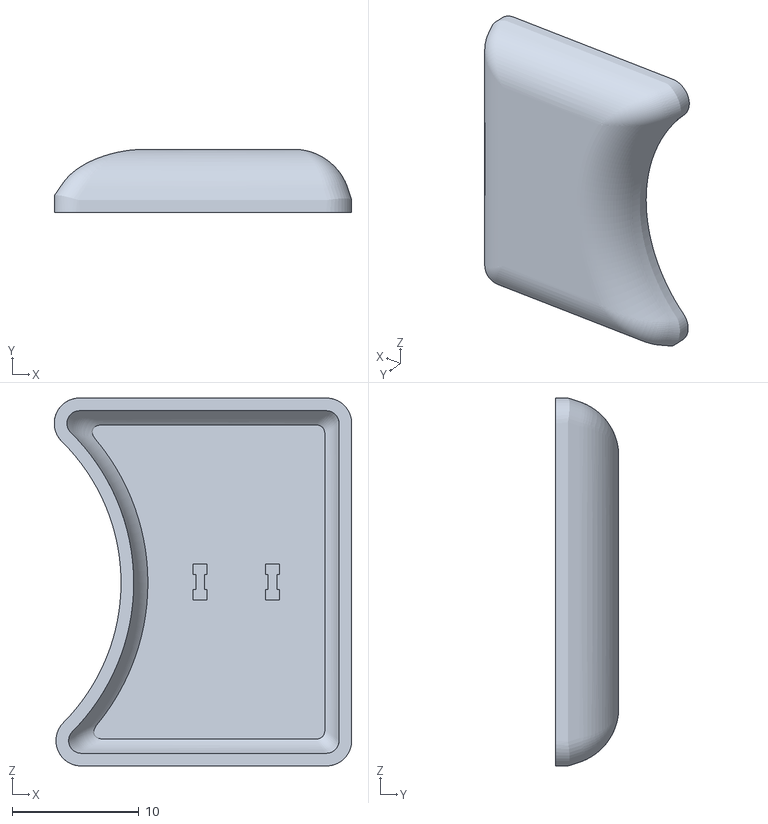
[picture p83: CAD file, 2020-05-06]
reform2-3d-printed-parts/historic-reform2-stl-2d4/circular round button 20200123.stl
23.4 x 5.00 x 29.0
