milestogo/reform/reform2-3d-printed-parts/trackball/reform2-trackball-support-20201005.stl

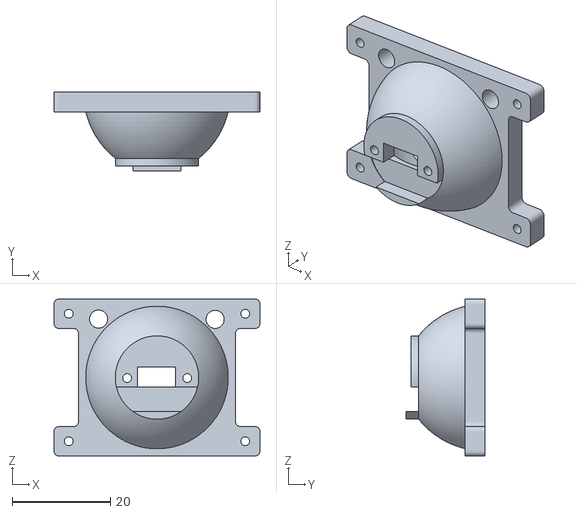
[picture p84: CAD file, 2020-10-28]
reform2-3d-printed-parts/trackball/reform2-trackball-support-20201005.stl
42.0 x 16.0 x 32.0
