milestogo/reform/reform2-batterypack-pcb/3d-models/keystone-PN54.STEP

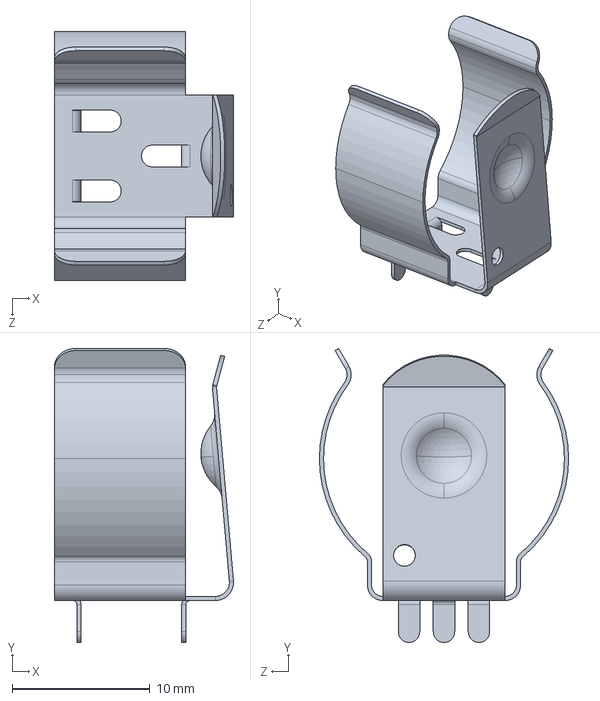
[picture p85: CAD file, 2020-04-11]
reform2-batterypack-pcb/3d-models/keystone-PN54.STEP
13.0 x 21.4 x 18.1 mm
