milestogo/reform/reform2-keyboard-pcb/3d-models/S4B-PH-SM4-TB.stp

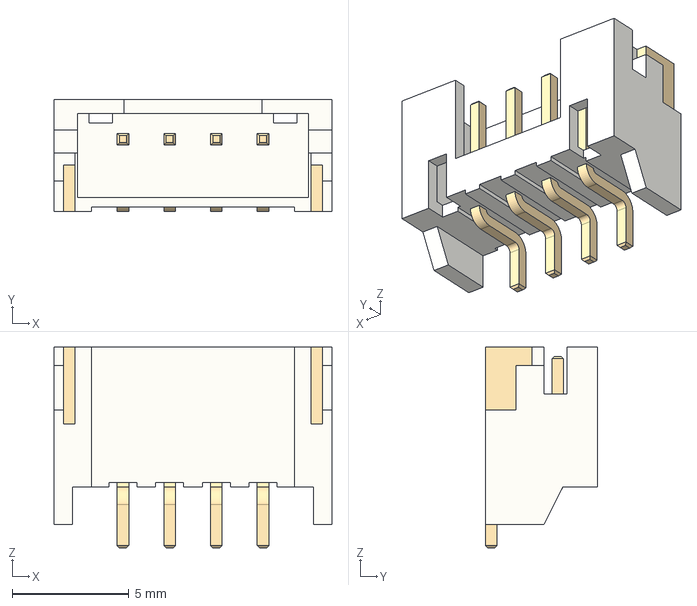
[picture p86: CAD file, 2020-04-11]
reform2-keyboard-pcb/3d-models/S4B-PH-SM4-TB.stp
11.9 x 4.80 x 8.60 mm
