milestogo/reform/reform2-trackball-pcb/3d-models/FH12-6S-0.5SH.stp

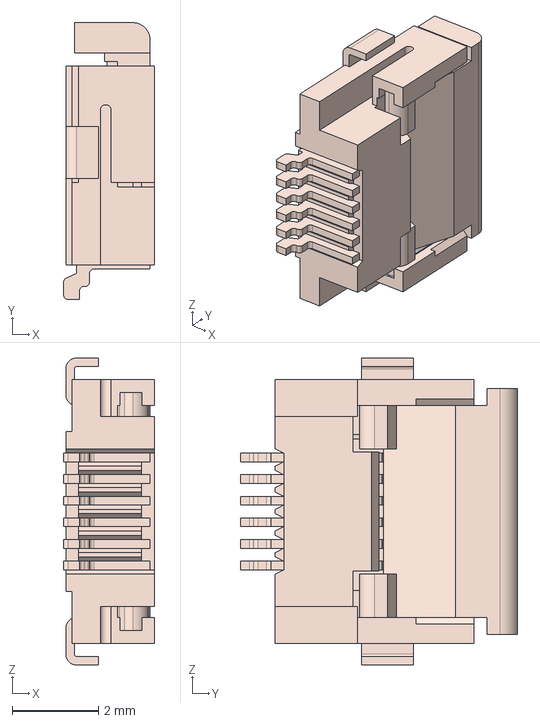
[picture p88: CAD file, 2020-04-11]
reform2-trackball-pcb/3d-models/FH12-6S-0.5SH.stp
2.10 x 6.40 x 7.10 mm
