milestogo/reform/reform2-trackball-sensor-pcb/3d-models/PAT9125Package.STEP

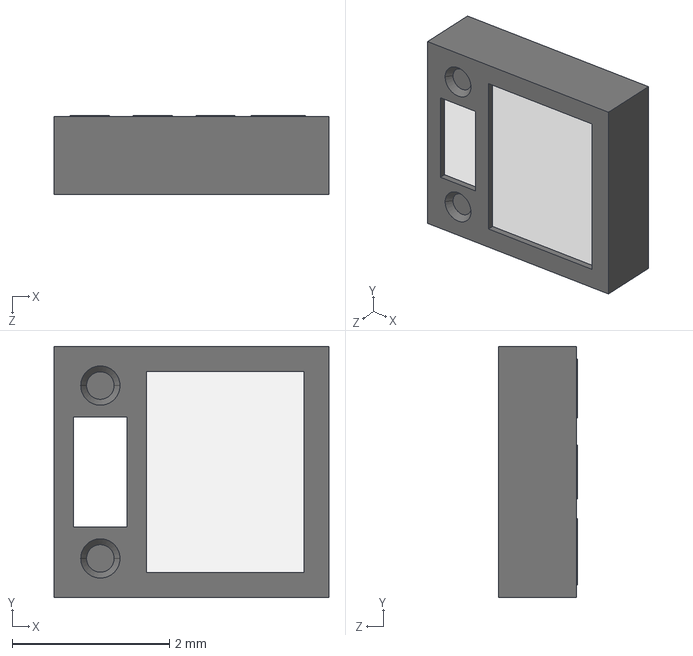
[picture p89: CAD file, 2020-04-11]
reform2-trackball-sensor-pcb/3d-models/PAT9125Package.STEP
3.50 x 3.20 x 1.00 mm
