milestogo/reform/historic-reform1/case-parts/screen_front_v3.STL

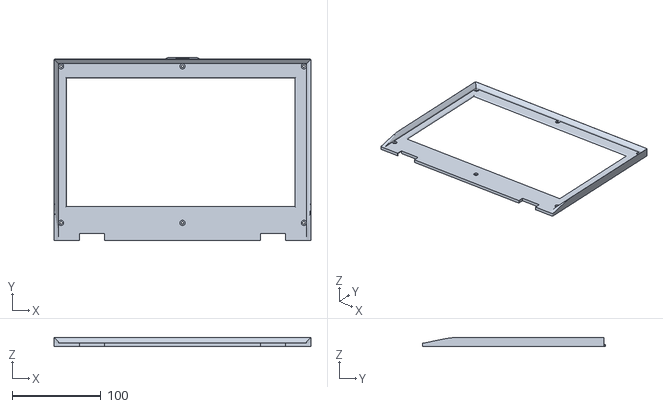
[picture p90: CAD file, 2018-11-12]
historic-reform1/case-parts/screen_front_v3.STL
290.0 x 206.7 x 10.7
