milestogo/reform/historic-reform1/keycaps/tab_final.STL

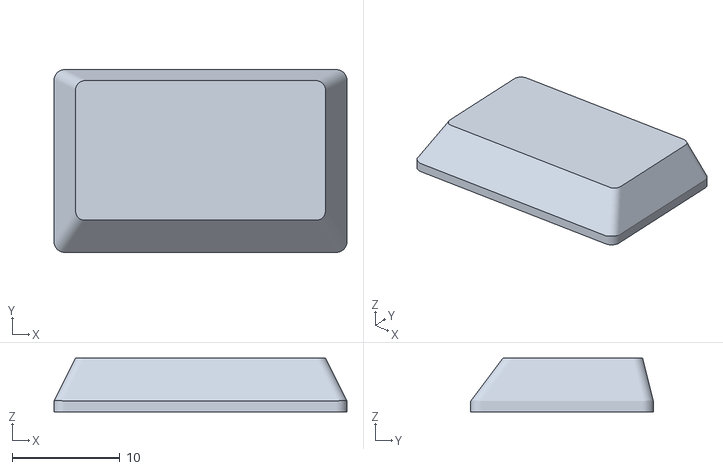
[picture p91: CAD file, 2018-11-12]
historic-reform1/keycaps/tab_final.STL
27.2 x 17.0 x 5.00
