milestogo/reform/historic-reform1/reform-trackball-pcb/dxf/reform-trackball-Edge.Cuts.dxf

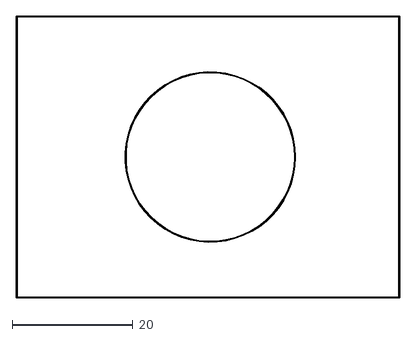
[picture p92: CAD file, 2018-11-12]
historic-reform1/reform-trackball-pcb/dxf/reform-trackball-Edge.Cuts.dxf
63.4 x 46.6
