milestogo/reform/historic-reform1/trackball-parts/trackball_cap_alt.stl

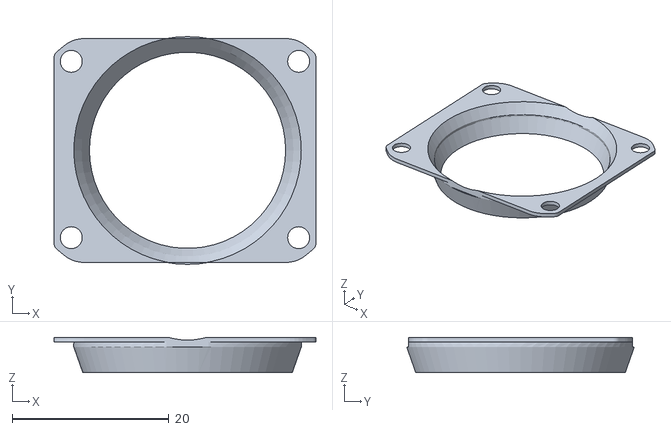
[picture p93: CAD file, 2018-11-12]
historic-reform1/trackball-parts/trackball_cap_alt.stl
33.4 x 29.0 x 4.50
