milestogo/reform/reform2-3d-printed-parts/historic-reform2-stl-2d4/trackpad support 20200225.stl

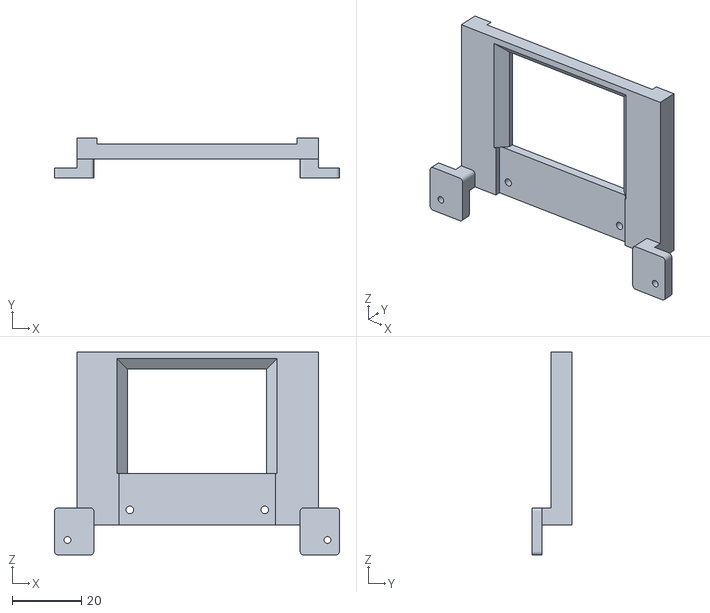
[picture p94: CAD file, 2020-05-06]
reform2-3d-printed-parts/historic-reform2-stl-2d4/trackpad support 20200225.stl
82.4 x 11.7 x 58.6
