milestogo/reform/reform2-trackball-pcb/3d-models/KMR221GLFS.step

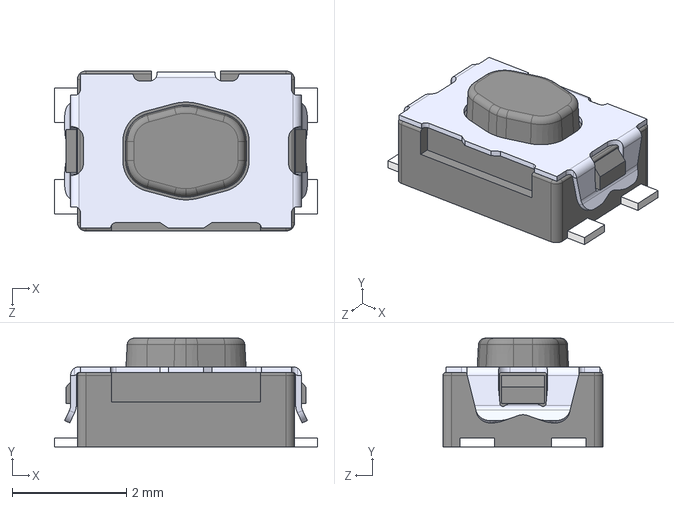
[picture p97: CAD file, 2020-04-11]
reform2-trackball-pcb/3d-models/KMR221GLFS.step
4.60 x 1.90 x 2.80 mm
