milestogo/reform/historic-reform1/case-parts/screen support bottom_v3.STL

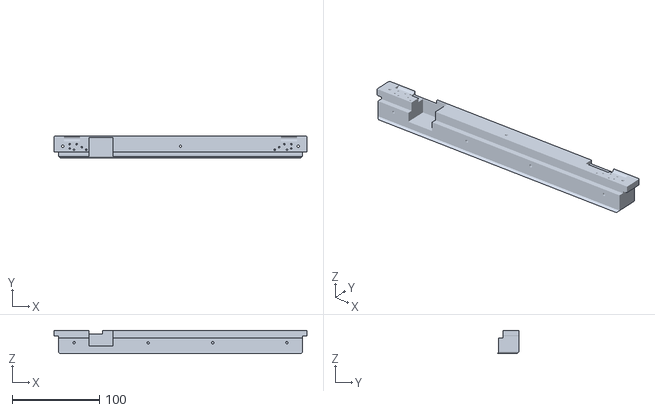
[picture p98: CAD file, 2018-11-12]
historic-reform1/case-parts/screen support bottom_v3.STL
290.0 x 25.2 x 26.7
