milestogo/reform/historic-reform1/keycaps/tab-new.stl

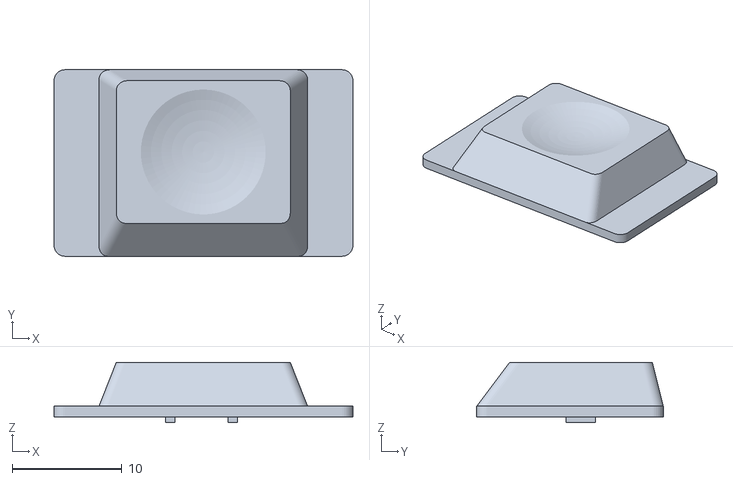
[picture p99: CAD file, 2018-11-12]
historic-reform1/keycaps/tab-new.stl
27.2 x 17.0 x 5.50
