milestogo/reform/historic-reform1/reform-trackball-pcb/dxf/#reform-trackball-B.Cu.dxf

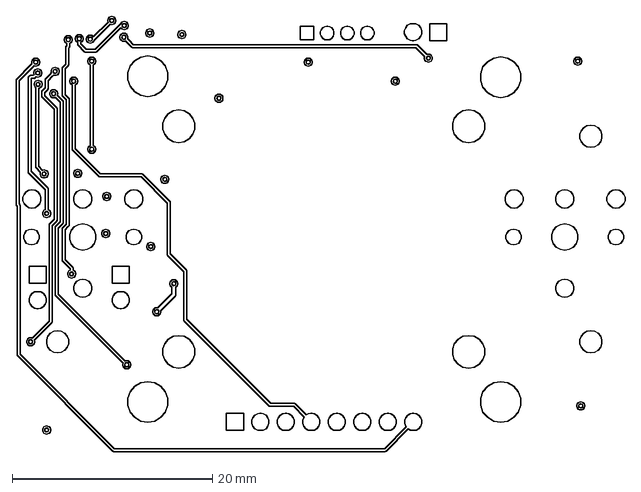
[picture p100: CAD file, 2018-11-12]
historic-reform1/reform-trackball-pcb/dxf/#reform-trackball-B.Cu.dxf
60.8 x 43.4 mm
