milestogo/reform/reform2-3d-printed-parts/historic-reform2-stl-2d4/trackball 4 small spheres 20200214.stl

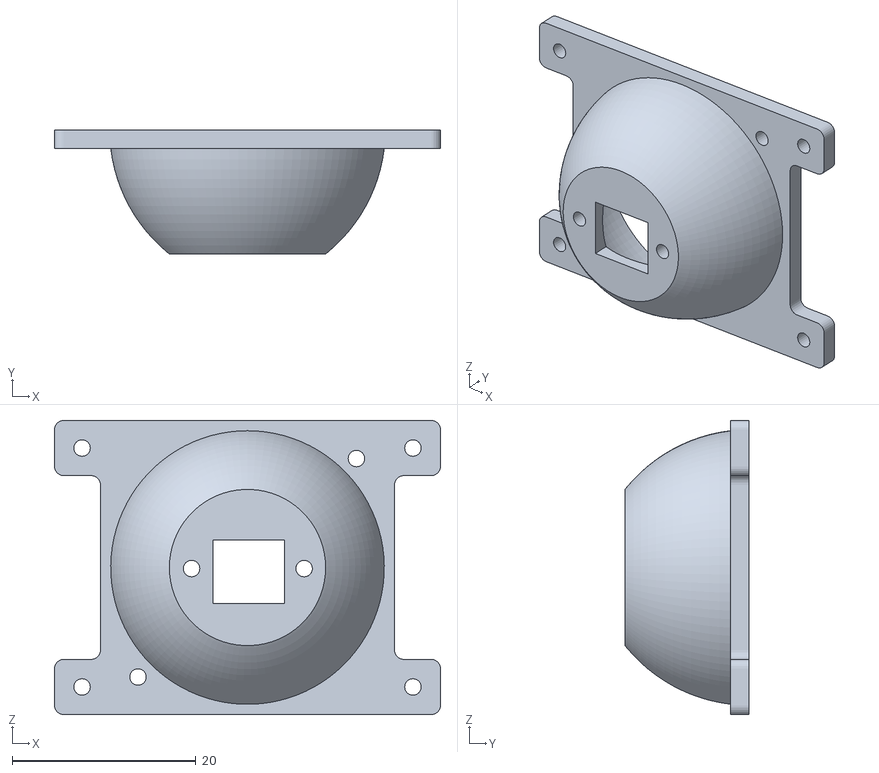
[picture p101: CAD file, 2020-05-06]
reform2-3d-printed-parts/historic-reform2-stl-2d4/trackball 4 small spheres 20200214.stl
42.0 x 13.5 x 32.0
