milestogo/reform/reform2-motherboard-pcb/3d-models/wuerth_692121030100_usb3.stp

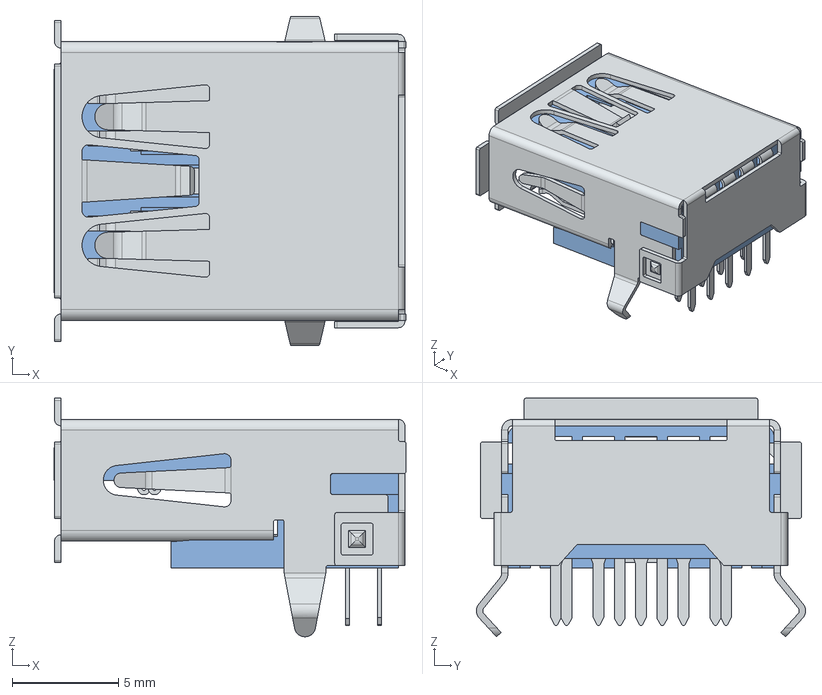
[picture p102: CAD file, 2020-10-29]
reform2-motherboard-pcb/3d-models/wuerth_692121030100_usb3.stp
16.6 x 15.5 x 11.2 mm
housing1
pin1 x 5
housing2
pin2 x 2
pin x 2
shielding
