milestogo/reform/historic-reform1/case-parts/screen_back_3dprint.STL

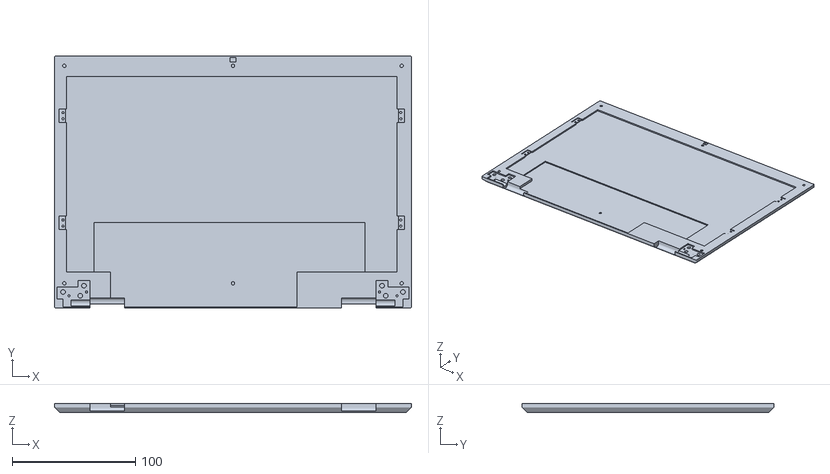
[picture p103: CAD file, 2018-11-12]
historic-reform1/case-parts/screen_back_3dprint.STL
290.0 x 204.7 x 7.00
