milestogo/reform/historic-reform1/keycaps/base keyboard stabilizer_C.STL

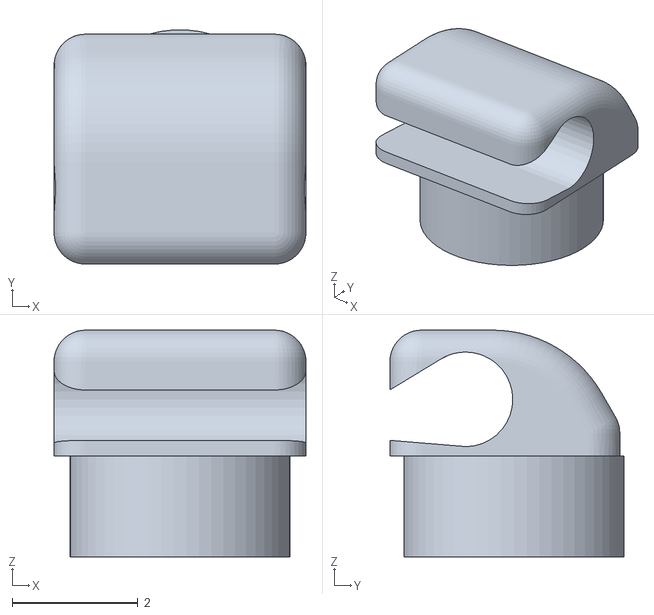
[picture p104: CAD file, 2018-11-12]
historic-reform1/keycaps/base keyboard stabilizer_C.STL
4.00 x 3.72 x 3.60
