milestogo/reform/historic-reform1/trackball-parts/trackball_support.stl

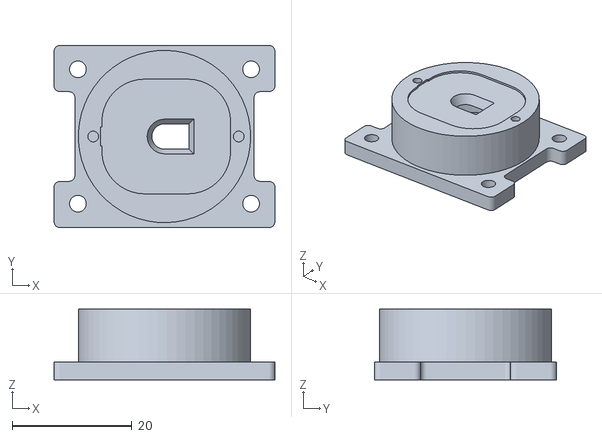
[picture p105: CAD file, 2018-11-12]
historic-reform1/trackball-parts/trackball_support.stl
37.0 x 30.5 x 11.8
