milestogo/reform/reform2-3d-printed-parts/historic-reform2-stl-2d4/rectangular round button 20200123.stl

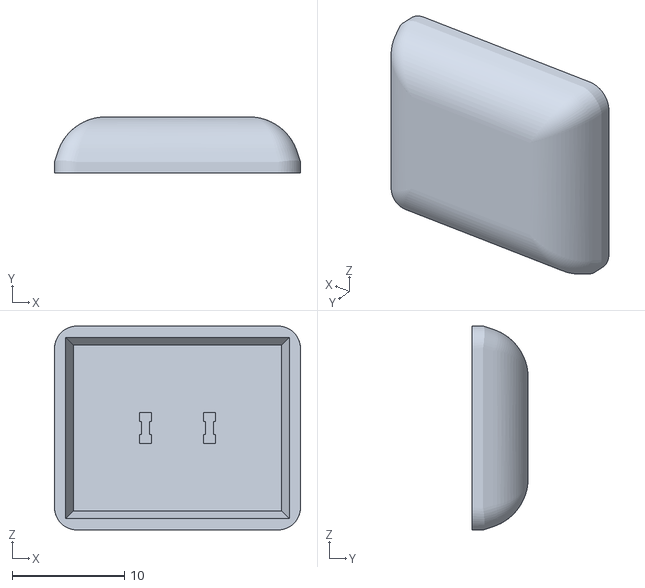
[picture p106: CAD file, 2020-05-06]
reform2-3d-printed-parts/historic-reform2-stl-2d4/rectangular round button 20200123.stl
21.9 x 5.00 x 18.1
