milestogo/reform/reform2-batterypack-pcb/3d-models/Bateria 18650 3.7 V 1300 mAh d.18 mm.STEP

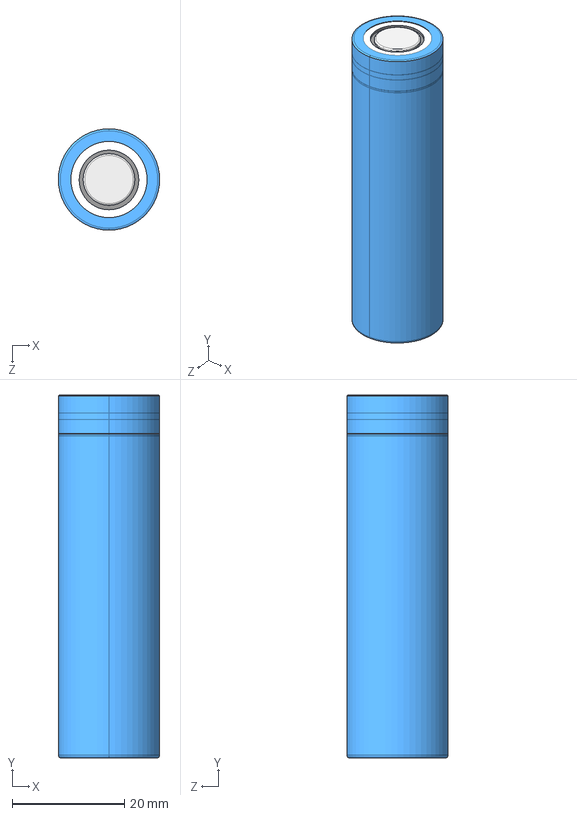
[picture p107: CAD file, 2020-04-11]
reform2-batterypack-pcb/3d-models/Bateria 18650 3.7 V 1300 mAh d.18 mm.STEP
18.1 x 64.7 x 18.1 mm
