milestogo/reform/reform2-case-cnc/reform2-beta-2d4/screen_front_25.02.20.step

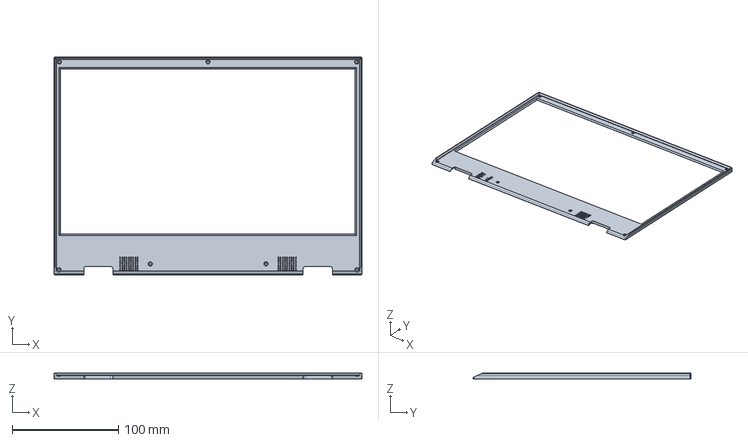
[picture p108: CAD file, 2020-04-11]
reform2-case-cnc/reform2-beta-2d4/screen_front_25.02.20.step
290.0 x 205.3 x 5.39 mm
