milestogo/reform/reform2-case-cnc/reform2-production-case-20201013/mntreform2-screen-front-20201008.step

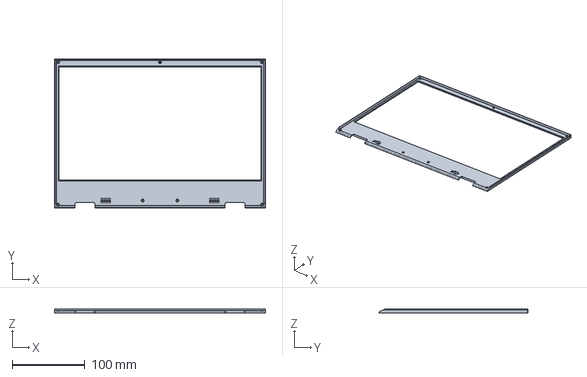
[picture p109: CAD file, 2020-10-24]
reform2-case-cnc/reform2-production-case-20201013/mntreform2-screen-front-20201008.step
290.0 x 205.3 x 5.49 mm
