milestogo/reform/reform2-keyboard-pcb/3d-models/EG1271A.step

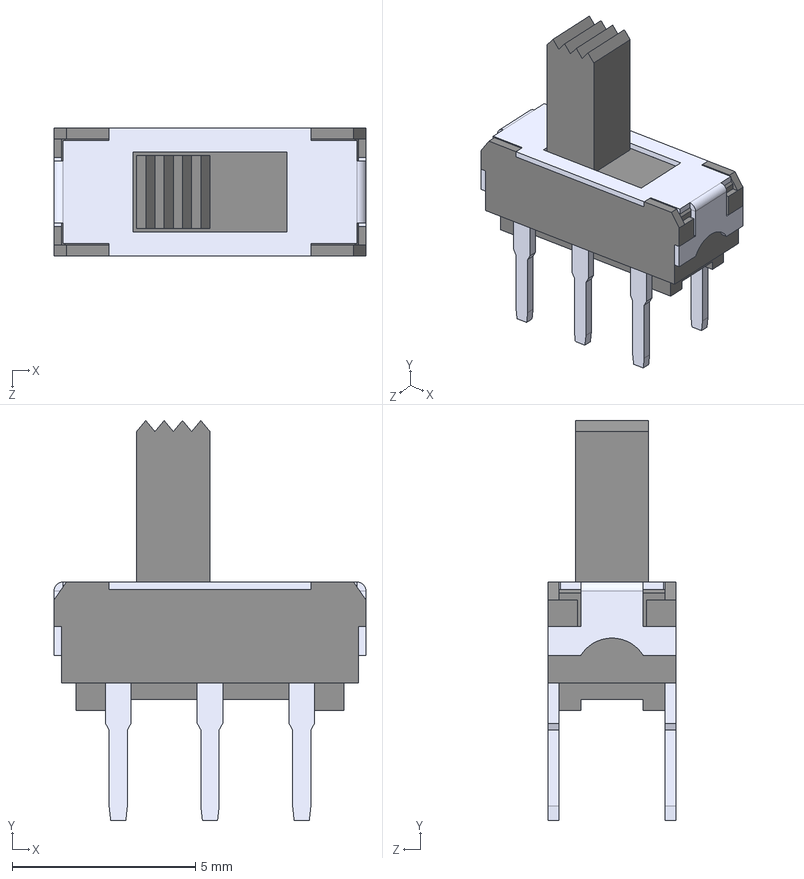
[picture p110: CAD file, 2020-04-11]
reform2-keyboard-pcb/3d-models/EG1271A.step
8.50 x 10.9 x 3.50 mm
