milestogo/reform/historic-reform1/keycaps/back space_final.STL

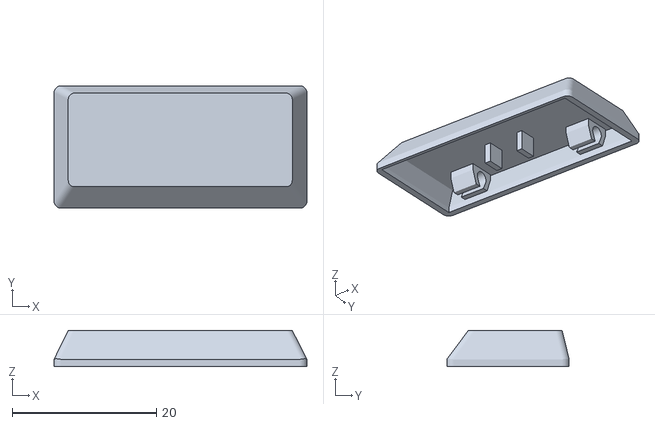
[picture p111: CAD file, 2018-11-12]
historic-reform1/keycaps/back space_final.STL
35.1 x 17.0 x 5.00
