milestogo/reform/reform2-case-cnc/reform2-beta-2d4/reform2heatsink2.step

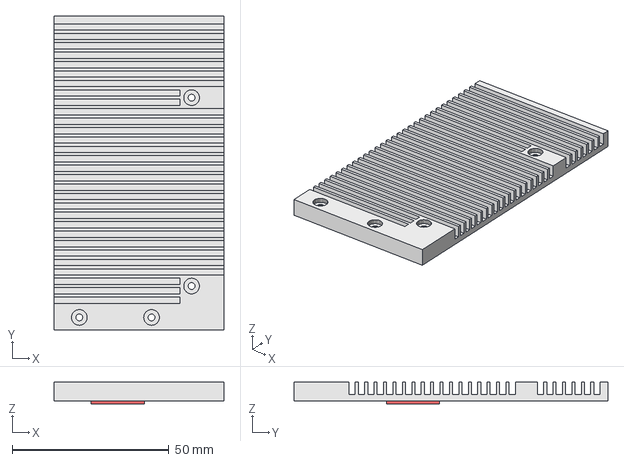
[picture p112: CAD file, 2020-04-11]
reform2-case-cnc/reform2-beta-2d4/reform2heatsink2.step
54.0 x 100.0 x 7.00 mm
