milestogo/reform/reform2-keyboard-pcb/3d-models/Kailh - keycap 1.5 v2.step

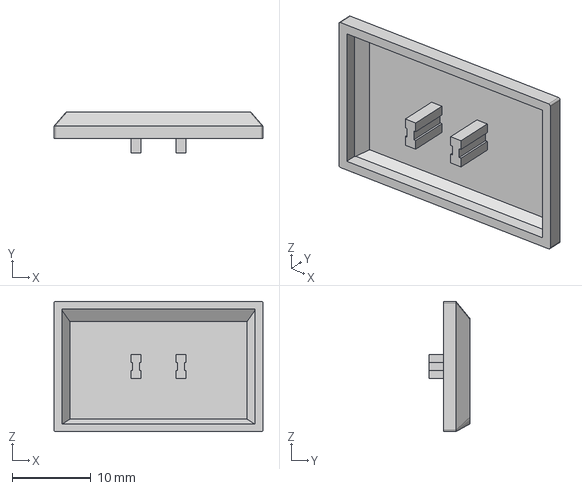
[picture p113: CAD file, 2020-04-11]
reform2-keyboard-pcb/3d-models/Kailh - keycap 1.5 v2.step
26.6 x 5.23 x 16.6 mm
