milestogo/reform/reform2-motherboard-pcb/3d-models/c-1775059-1-d-3d.stp

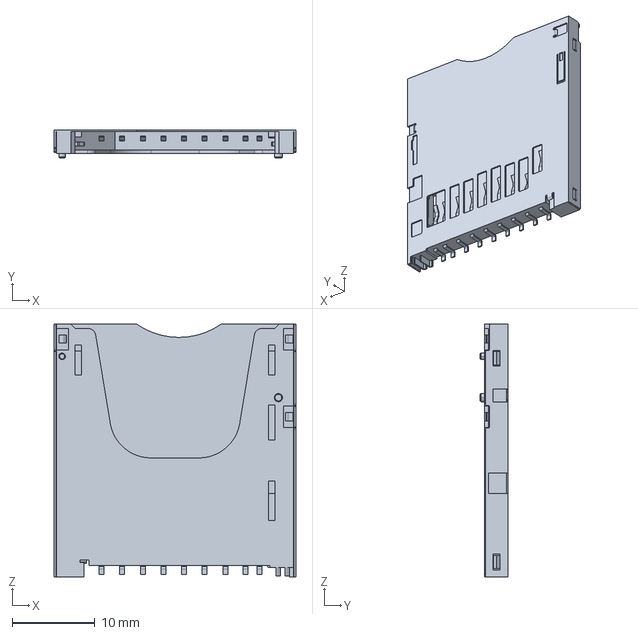
[picture p114: CAD file, 2020-04-11]
reform2-motherboard-pcb/3d-models/c-1775059-1-d-3d.stp
29.3 x 3.40 x 30.6 mm
