milestogo/reform/historic-reform1/case-parts/battery_holder_modified2.stl

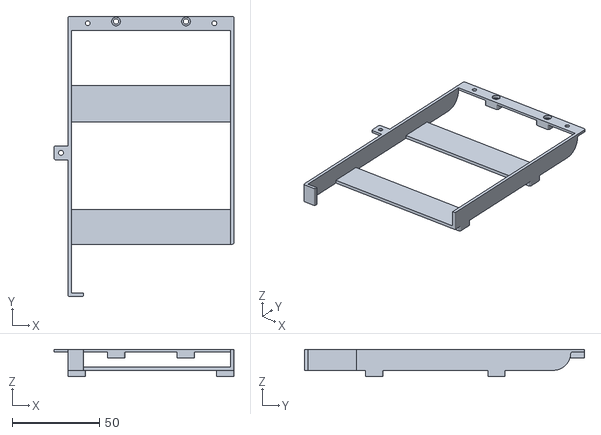
[picture p115: CAD file, 2018-11-12]
historic-reform1/case-parts/battery_holder_modified2.stl
103.0 x 160.5 x 15.5
