milestogo/reform/historic-reform1/keycaps/space bar_final.STL

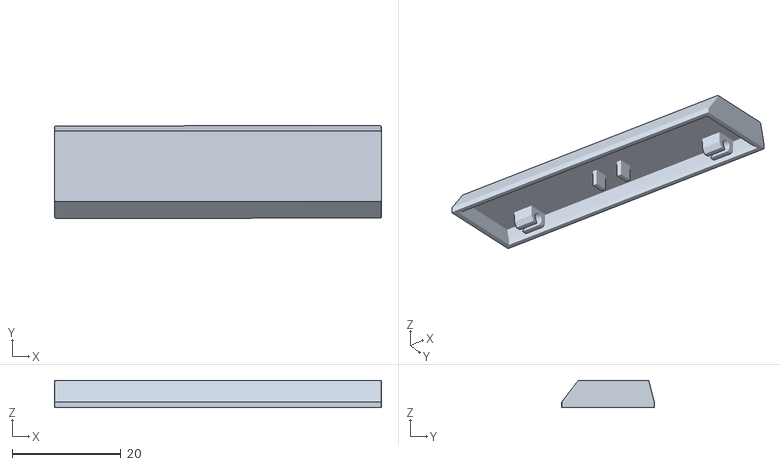
[picture p116: CAD file, 2018-11-12]
historic-reform1/keycaps/space bar_final.STL
60.0 x 17.0 x 5.00
