milestogo/reform/historic-reform1/case-parts/screen support closing.STL

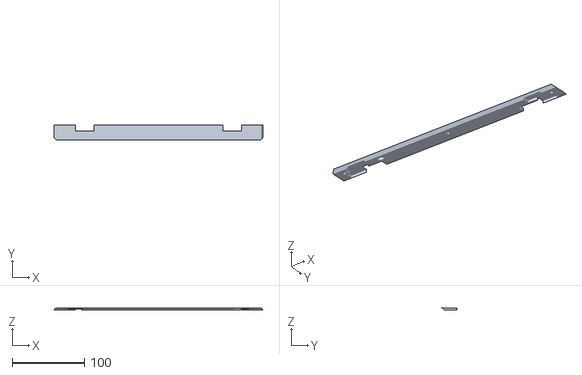
[picture p117: CAD file, 2018-11-12]
historic-reform1/case-parts/screen support closing.STL
290.0 x 21.2 x 3.30
