milestogo/reform/historic-reform1/keycaps/base keyboard stabilizer_U.STL

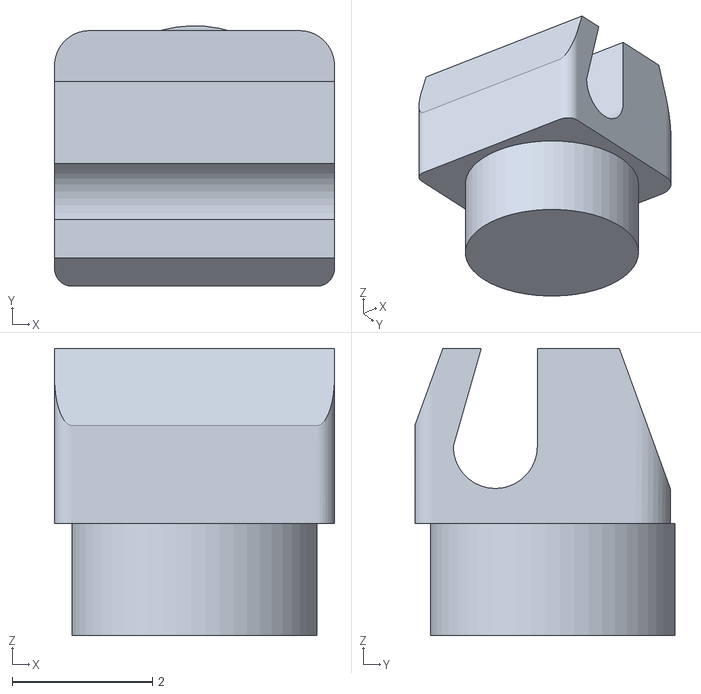
[picture p118: CAD file, 2018-11-12]
historic-reform1/keycaps/base keyboard stabilizer_U.STL
4.00 x 3.72 x 4.10
