milestogo/reform/historic-reform1/keycaps/enter_final.STL

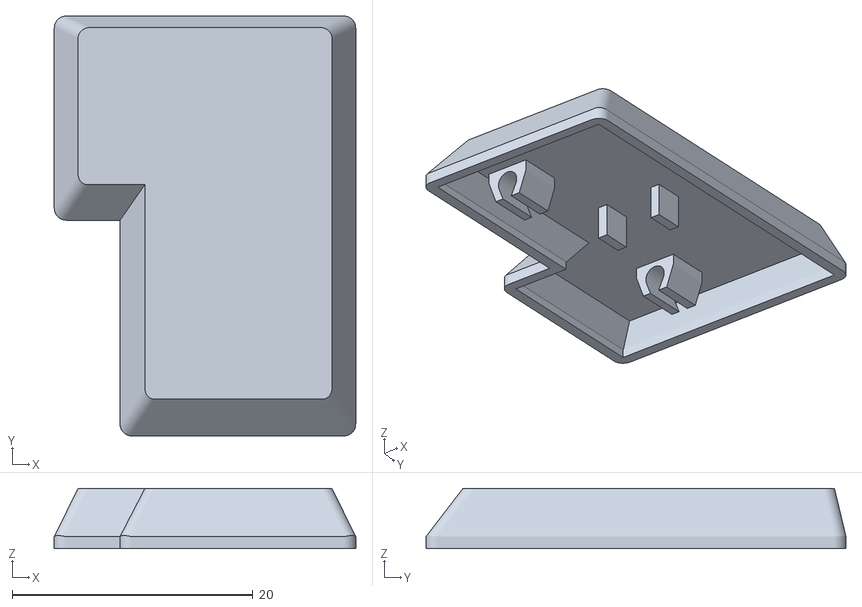
[picture p119: CAD file, 2018-11-12]
historic-reform1/keycaps/enter_final.STL
25.0 x 34.9 x 5.00
