milestogo/reform/historic-reform1/keycaps/tbleft_button_final.STL

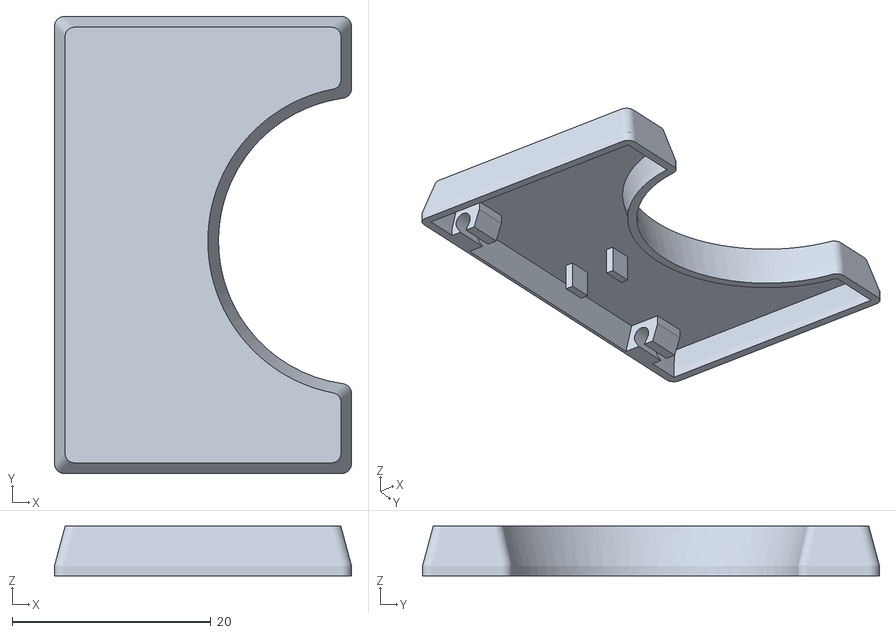
[picture p120: CAD file, 2018-11-12]
historic-reform1/keycaps/tbleft_button_final.STL
29.9 x 46.0 x 5.00
