milestogo/reform/reform2-keyboard-pcb/3d-models/500SSPxS2M2xEA.stp

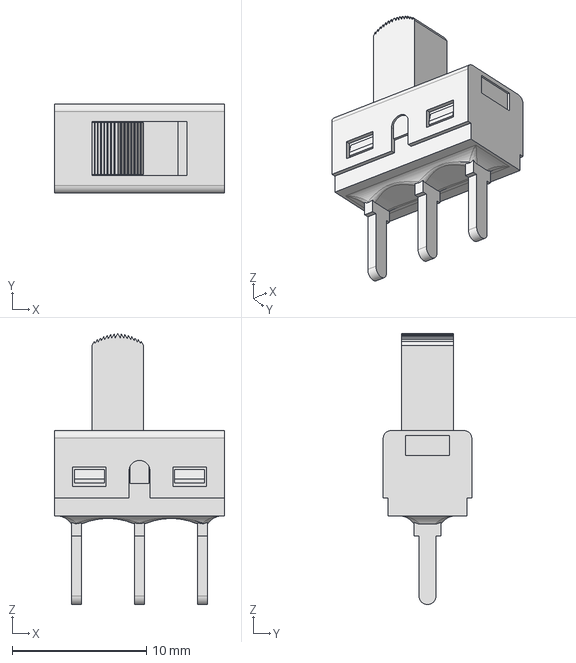
[picture p121: CAD file, 2020-04-11]
reform2-keyboard-pcb/3d-models/500SSPxS2M2xEA.stp
12.7 x 6.60 x 20.2 mm
