milestogo/reform/reform2-motherboard-pcb/3d-models/21-0140L_T1655-2.step

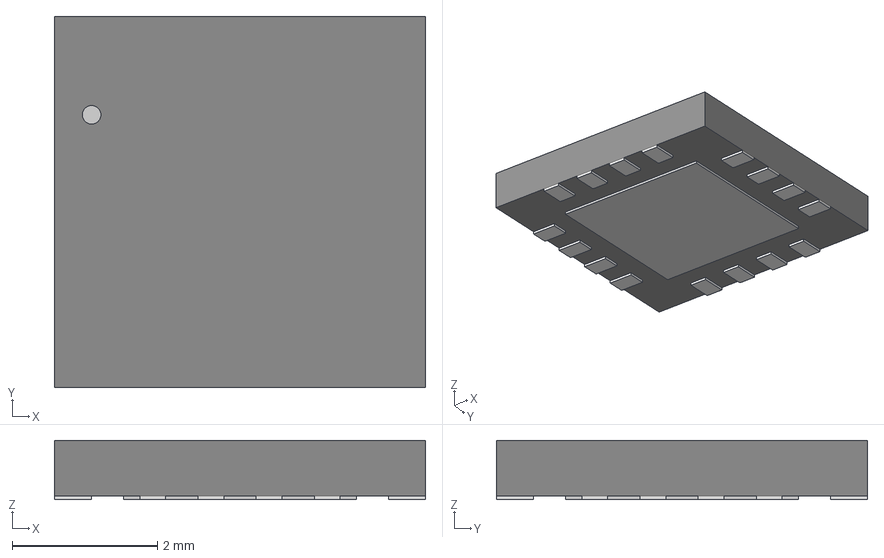
[picture p122: CAD file, 2020-04-11]
reform2-motherboard-pcb/3d-models/21-0140L_T1655-2.step
5.11 x 5.11 x 0.815 mm
