milestogo/reform/reform2-keyboard-pcb/3d-models/Kailh_keycap-switch_system_1.5x1.step

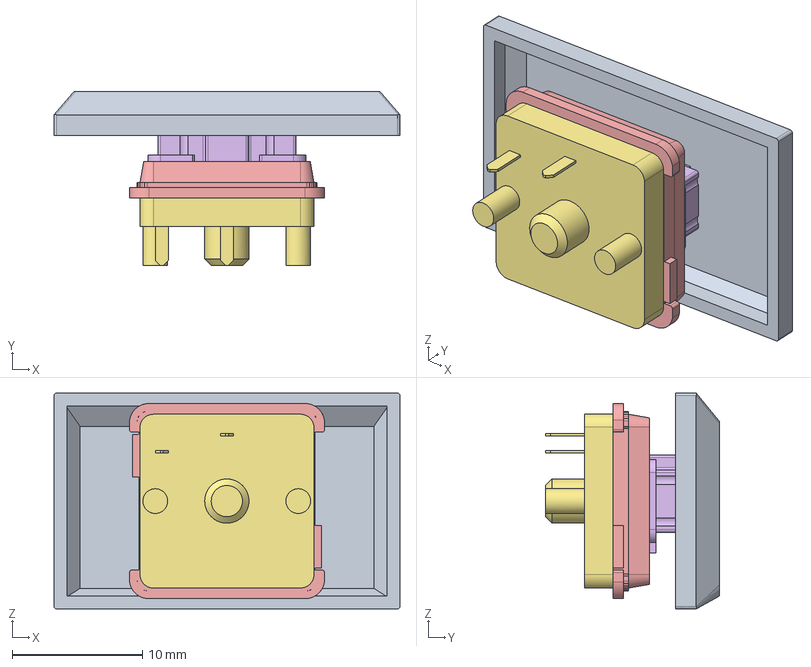
[picture p123: CAD file, 2020-04-11]
reform2-keyboard-pcb/3d-models/Kailh_keycap-switch_system_1.5x1.step
26.6 x 13.4 x 16.6 mm
