milestogo/reform/reform2-motherboard-pcb/3d-models/FH12-33S-0.5SH.stp

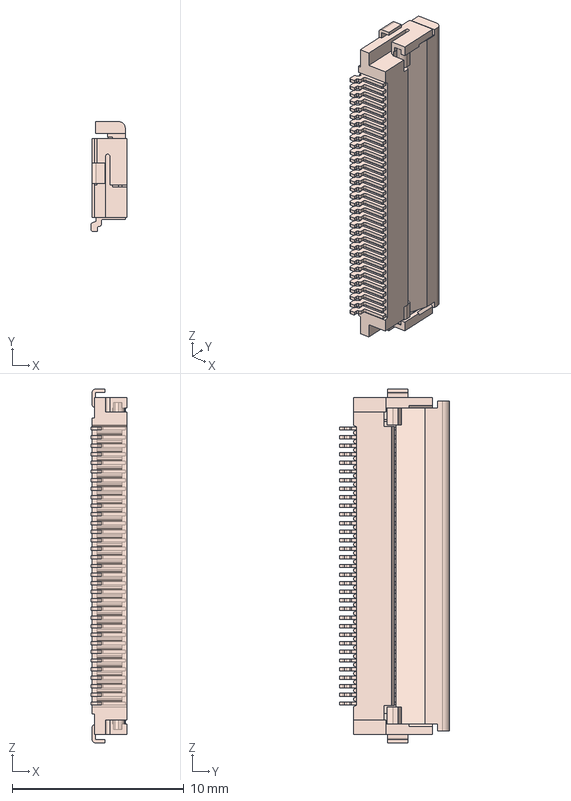
[picture p124: CAD file, 2020-04-11]
reform2-motherboard-pcb/3d-models/FH12-33S-0.5SH.stp
2.10 x 6.40 x 20.6 mm
