milestogo/reform/reform2-motherboard-pcb/3d-models/SMD_Polyfuse_2920.stp

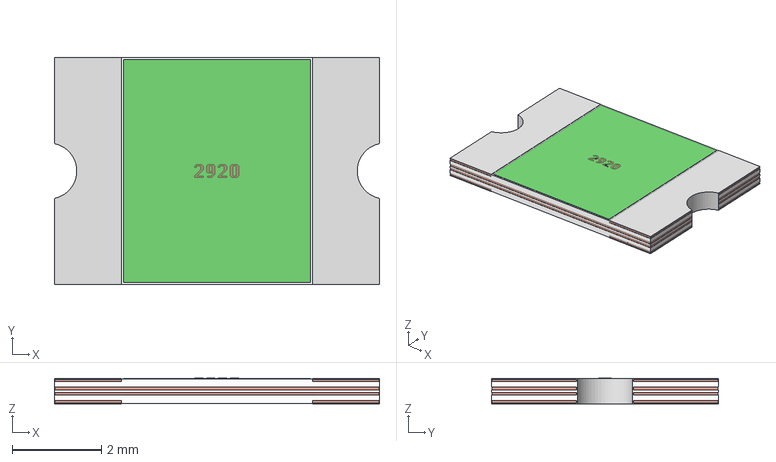
[picture p125: CAD file, 2020-04-11]
reform2-motherboard-pcb/3d-models/SMD_Polyfuse_2920.stp
7.30 x 5.10 x 0.575 mm
