milestogo/reform/reform2-motherboard-pcb/3d-models/c-1-2199230-5-b2-3d.stp

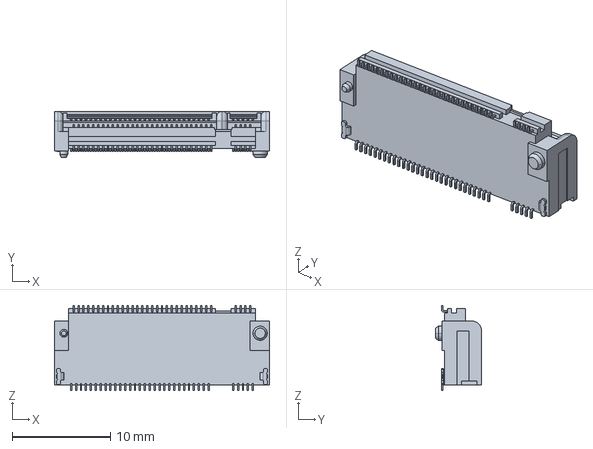
[picture p126: CAD file, 2020-04-11]
reform2-motherboard-pcb/3d-models/c-1-2199230-5-b2-3d.stp
21.9 x 4.70 x 8.70 mm
