milestogo/reform/reform2-motherboard-pcb/3d-models/PowerPAK SO-8.stp

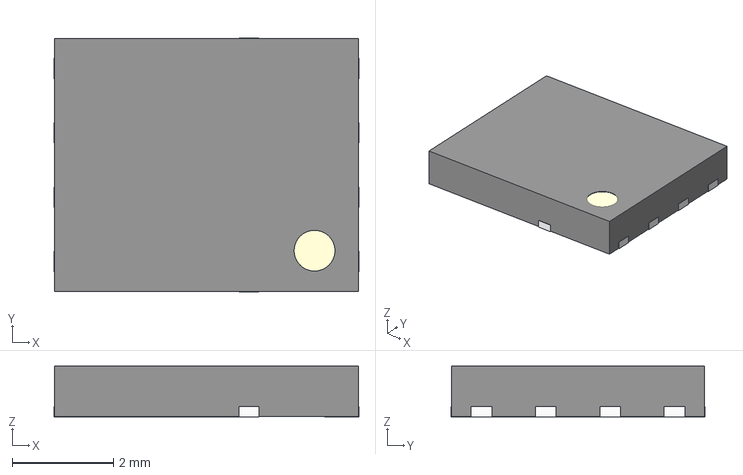
[picture p127: CAD file, 2020-04-11]
reform2-motherboard-pcb/3d-models/PowerPAK SO-8.stp
6.02 x 5.02 x 1.00 mm
pins
