milestogo/reform/reform2-motherboard-pcb/3d-models/sj-43516-smt.step

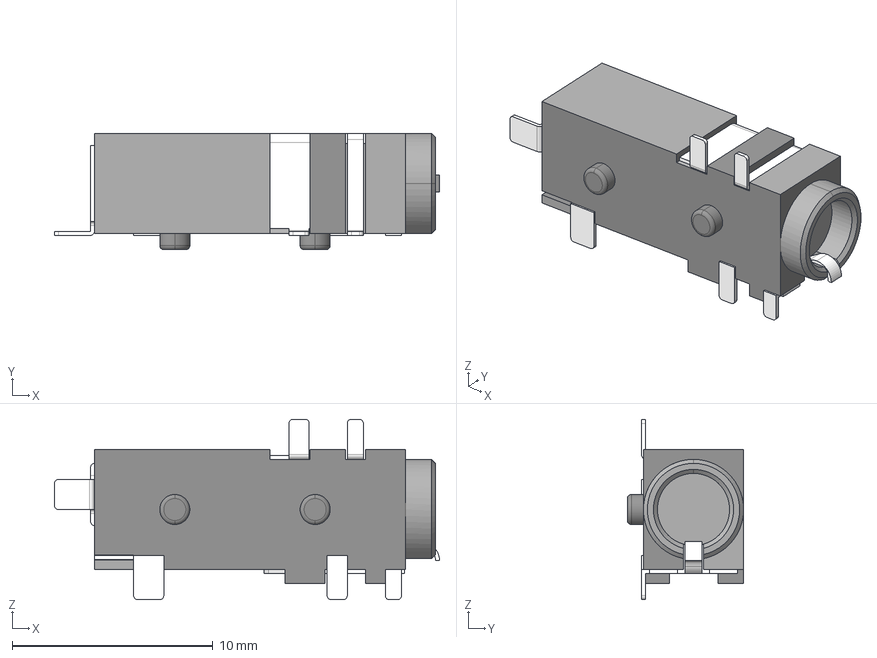
[picture p128: CAD file, 2020-04-11]
reform2-motherboard-pcb/3d-models/sj-43516-smt.step
19.2 x 5.80 x 9.00 mm
