milestogo/reform/reform2-motherboard-pcb/3d-models/KMR243GLFG.stp

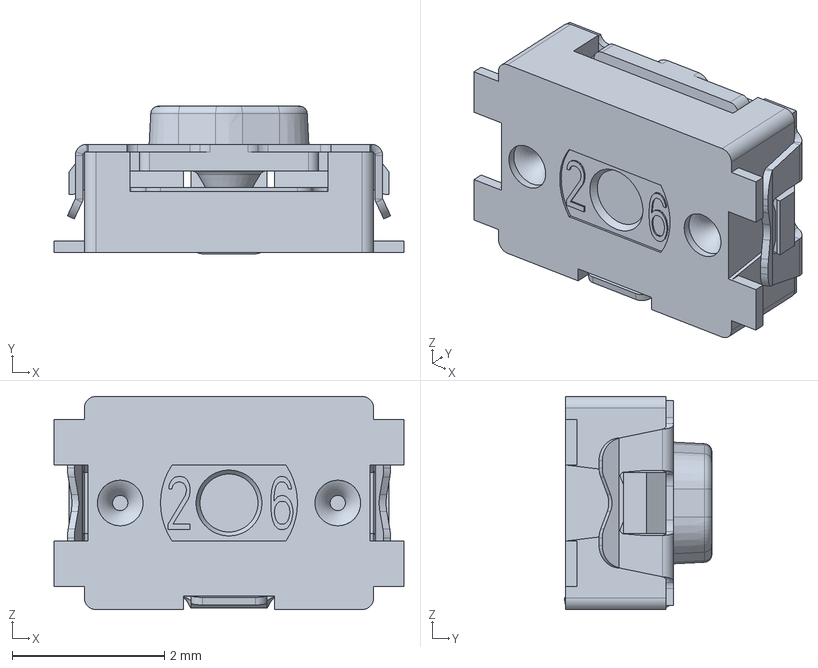
[picture p129: CAD file, 2020-04-11]
reform2-motherboard-pcb/3d-models/KMR243GLFG.stp
4.60 x 1.94 x 2.80 mm
