milestogo/reform/reform2-motherboard-pcb/3d-models/CM2020-00TR--3DModel-STEP-56544.STEP

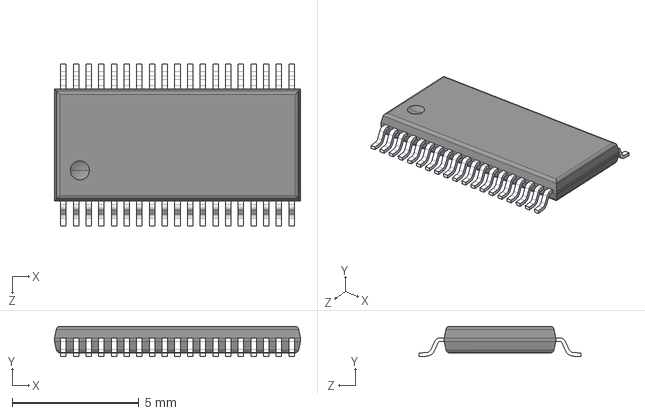
[picture p130: CAD file, 2020-04-11]
reform2-motherboard-pcb/3d-models/CM2020-00TR--3DModel-STEP-56544.STEP
9.70 x 1.20 x 6.40 mm
