milestogo/reform/reform2-motherboard-pcb/3d-models/uj3-ah-4-th.step

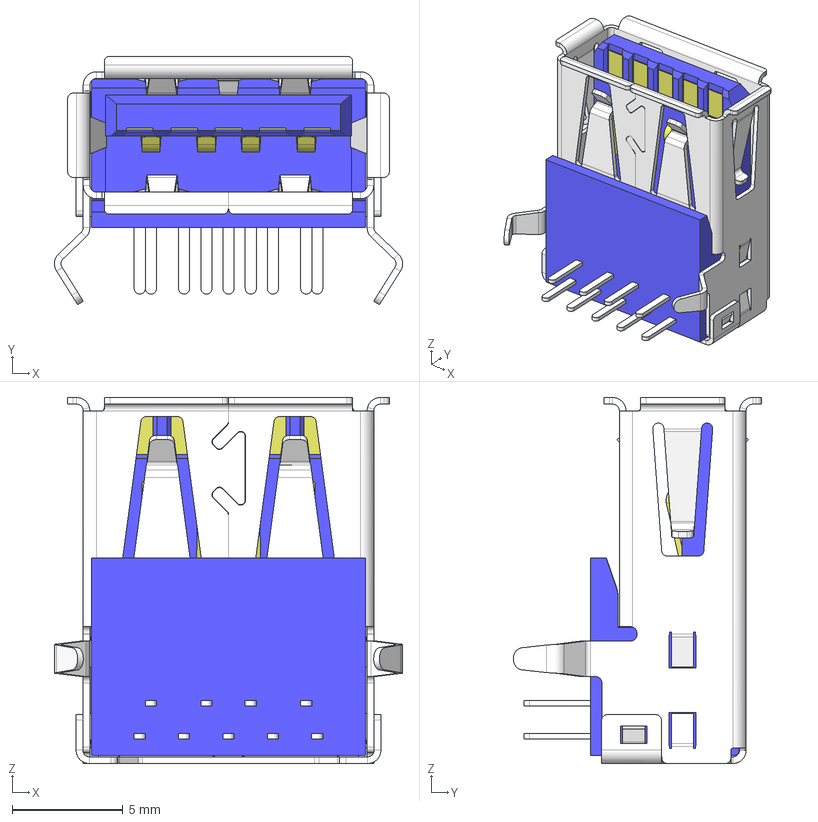
[picture p131: CAD file, 2020-04-11]
reform2-motherboard-pcb/3d-models/uj3-ah-4-th.step
15.7 x 11.2 x 16.5 mm
