milestogo/reform/reform2-motherboard-pcb/3d-models/L8BE-1G1T-BFH--3DModel-STEP-56544.STEP

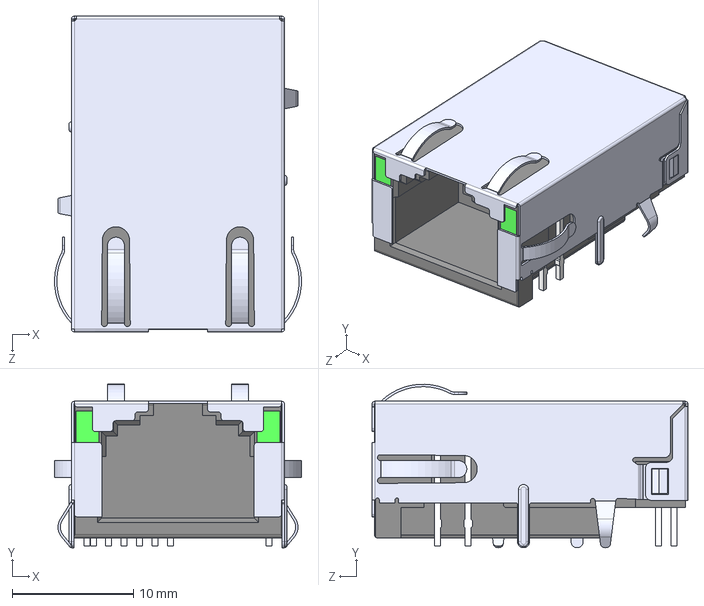
[picture p132: CAD file, 2020-04-11]
reform2-motherboard-pcb/3d-models/L8BE-1G1T-BFH--3DModel-STEP-56544.STEP
20.4 x 13.5 x 26.1 mm
