milestogo/reform/reform2-motherboard-pcb/3d-models/srr1210.stp

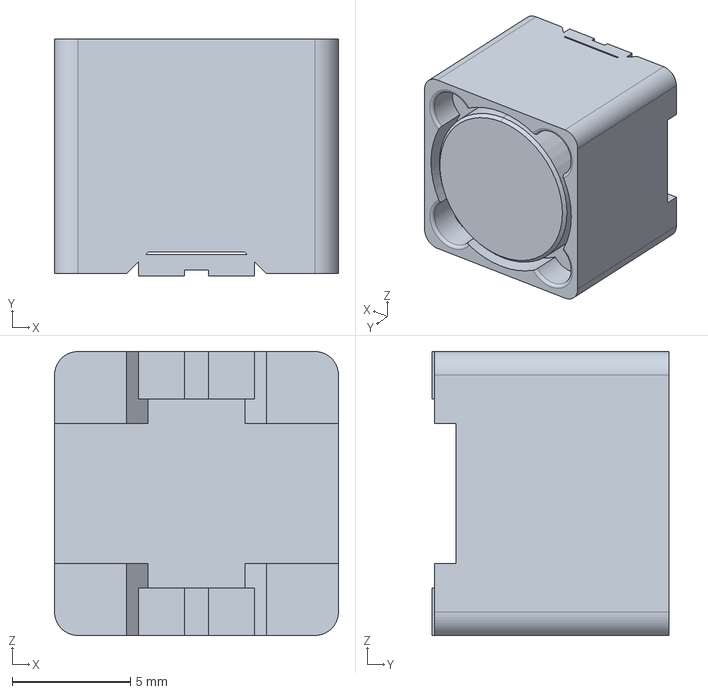
[picture p133: CAD file, 2020-04-11]
reform2-motherboard-pcb/3d-models/srr1210.stp
12.0 x 10.0 x 12.0 mm
