milestogo/reform/reform2-motherboard-pcb/3d-models/J0G-0003NL.step

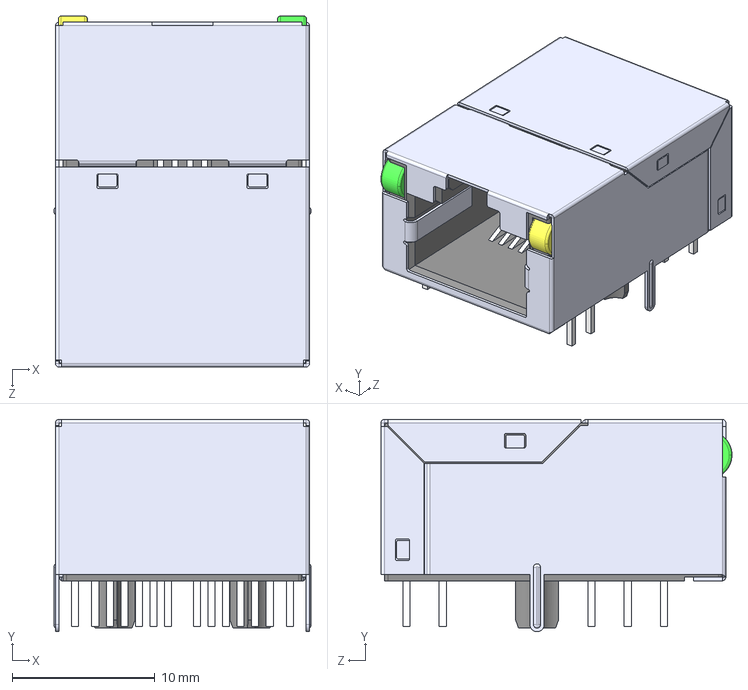
[picture p134: CAD file, 2020-04-11]
reform2-motherboard-pcb/3d-models/J0G-0003NL.step
18.0 x 14.9 x 24.6 mm
