milestogo/reform/reform2-motherboard-pcb/3d-models/c-5-2069716-2-c-3d.stp

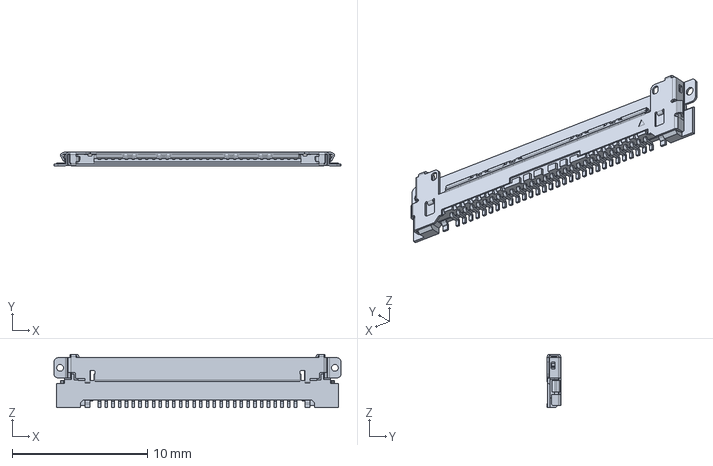
[picture p135: CAD file, 2020-04-11]
reform2-motherboard-pcb/3d-models/c-5-2069716-2-c-3d.stp
21.2 x 1.00 x 3.95 mm
