milestogo/reform/historic-reform1/case-parts/trackball-spacer.scad

difference() {
  cylinder(4.9, 6/2, 6/2, true, $fn=60);
  cylinder(6, 2.5/2, 2.5/2, true, $fn=60);
}
