milestogo/reform/historic-reform1/keycaps/wirejig.scad

cube(size=[11,25,15]);
translate([-1,-1,0]) cube(size=[13,27,3]);
translate([-1,-1,4]) cube(size=[13,27,3]);
