milestogo/reform/historic-reform1/handbook/source/keyboard/reform-keyboard-page-2b.pdf

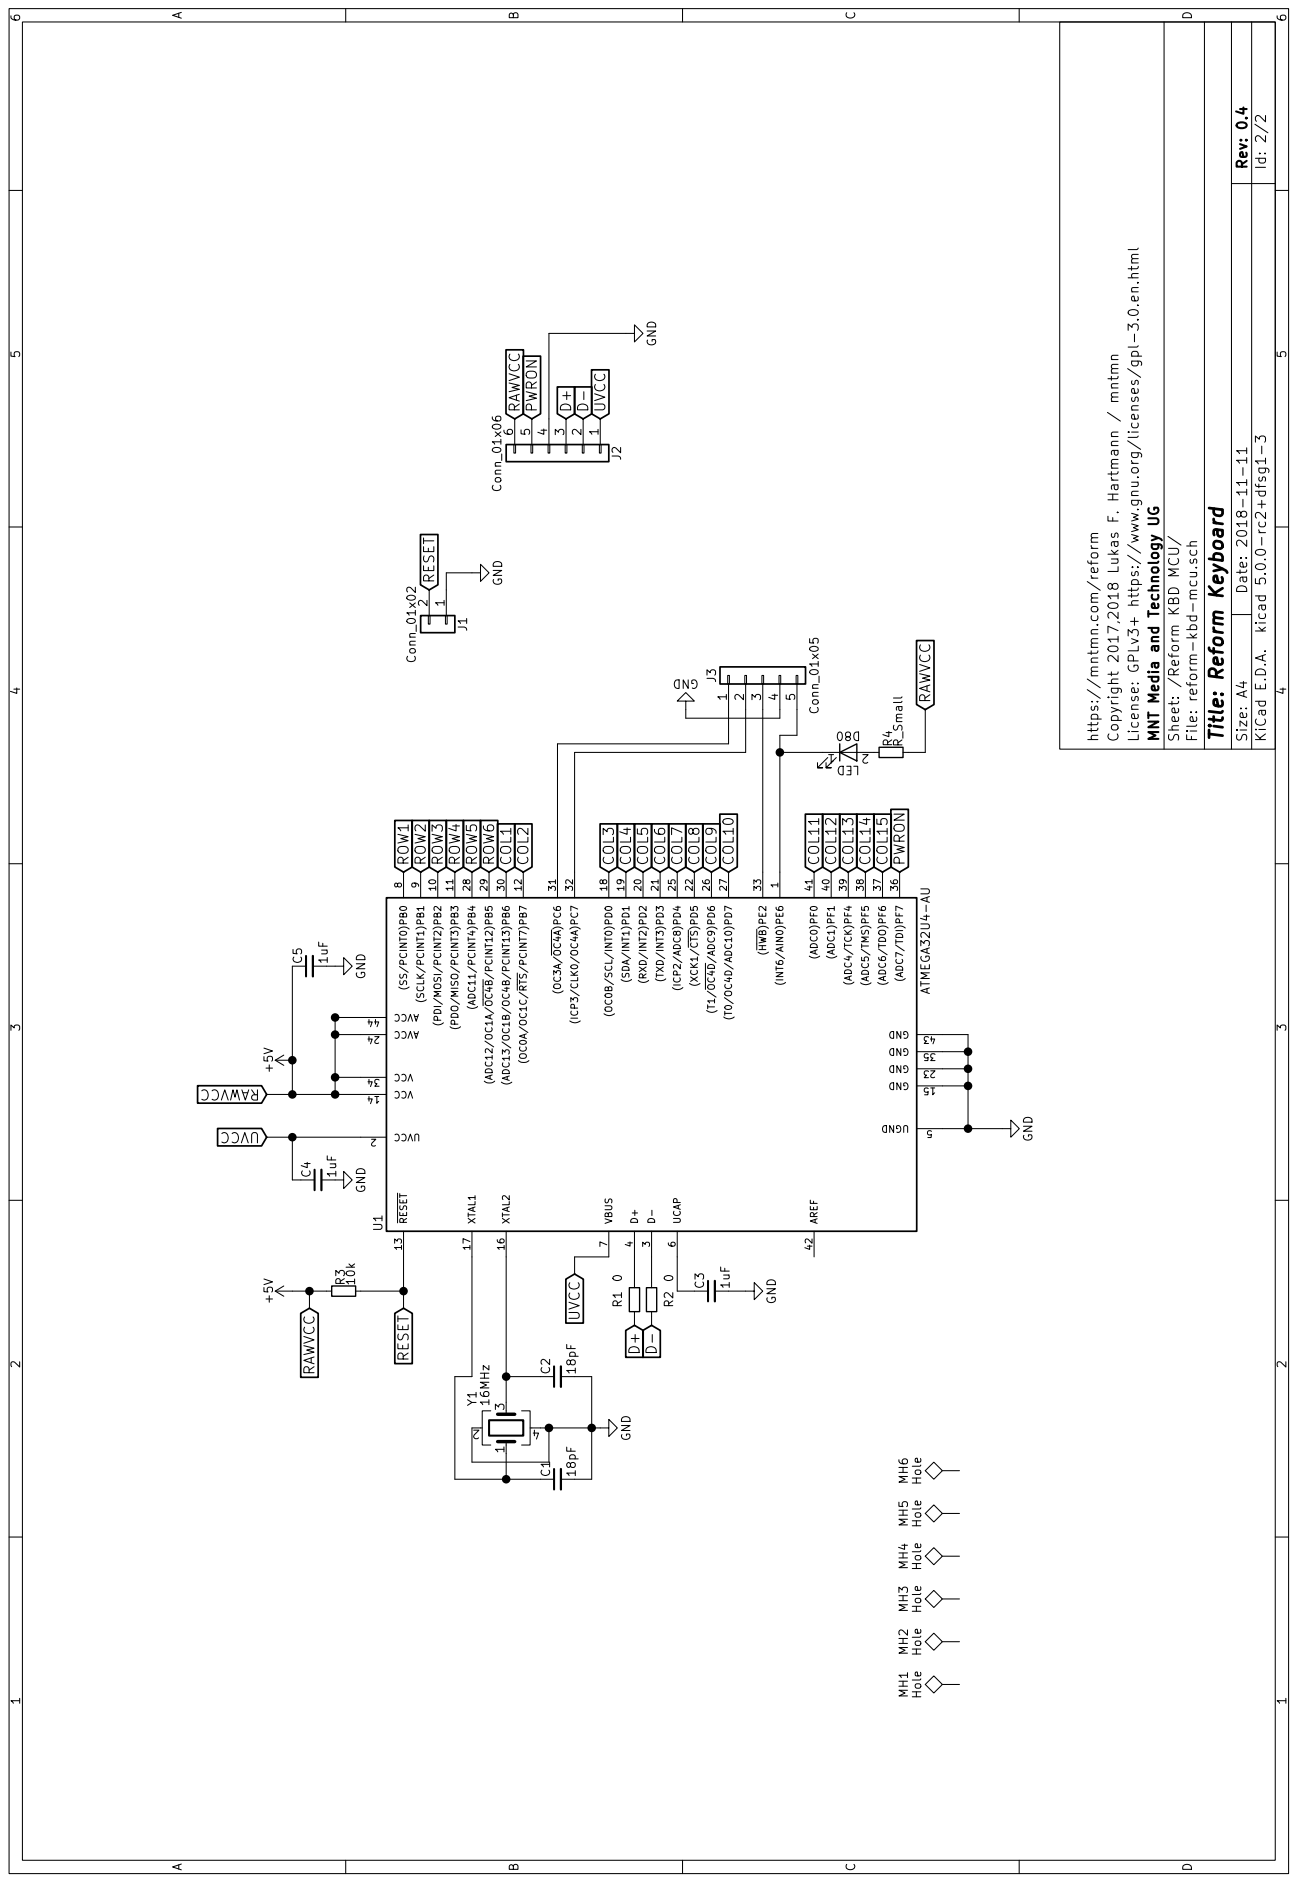
[picture p148: page 1]
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

License: GPLv3+ https://www.gnu.org/licenses/gpl-3.0.en.html

Copyright 2017,2018 Lukas F. Hartmann / mntmn

MNT Media and Technology UG

Sheet: /Reform KBD MCU/ File: reform-kbd-mcu.sch Title: Reform Keyboard

https://mntmn.com/reform

33 GND 43 VCC 14 AVCC 24 VCC 34 AVCC 44 GND 15

1uF GND GND MH1 Hole MH2 Hole MH3 Hole MH4 Hole
