milestogo/reform/historic-reform1/handbook/source/motherboard/reform-motherboard-page-1.pdf

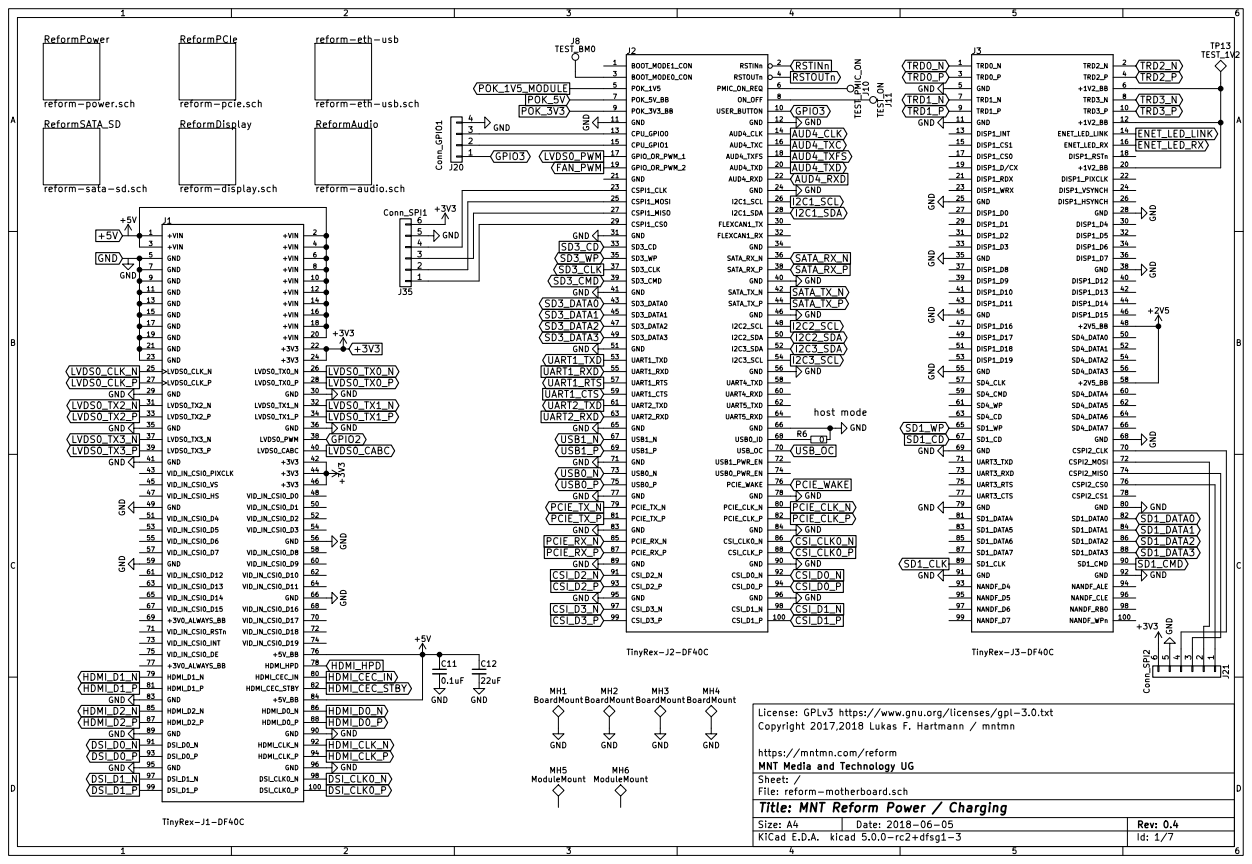
[picture p149: page 1]

reform-eth-usb.sch ReformDisplay

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

https://mntmn.com/reform
File: reform-motherboard.sch Sheet: / MNT Media and Technology UG

Id: 1/7 Title: MNT Reform Power / Charging
