milestogo/reform/historic-reform1/handbook/source/motherboard/reform-motherboard-page-2.pdf

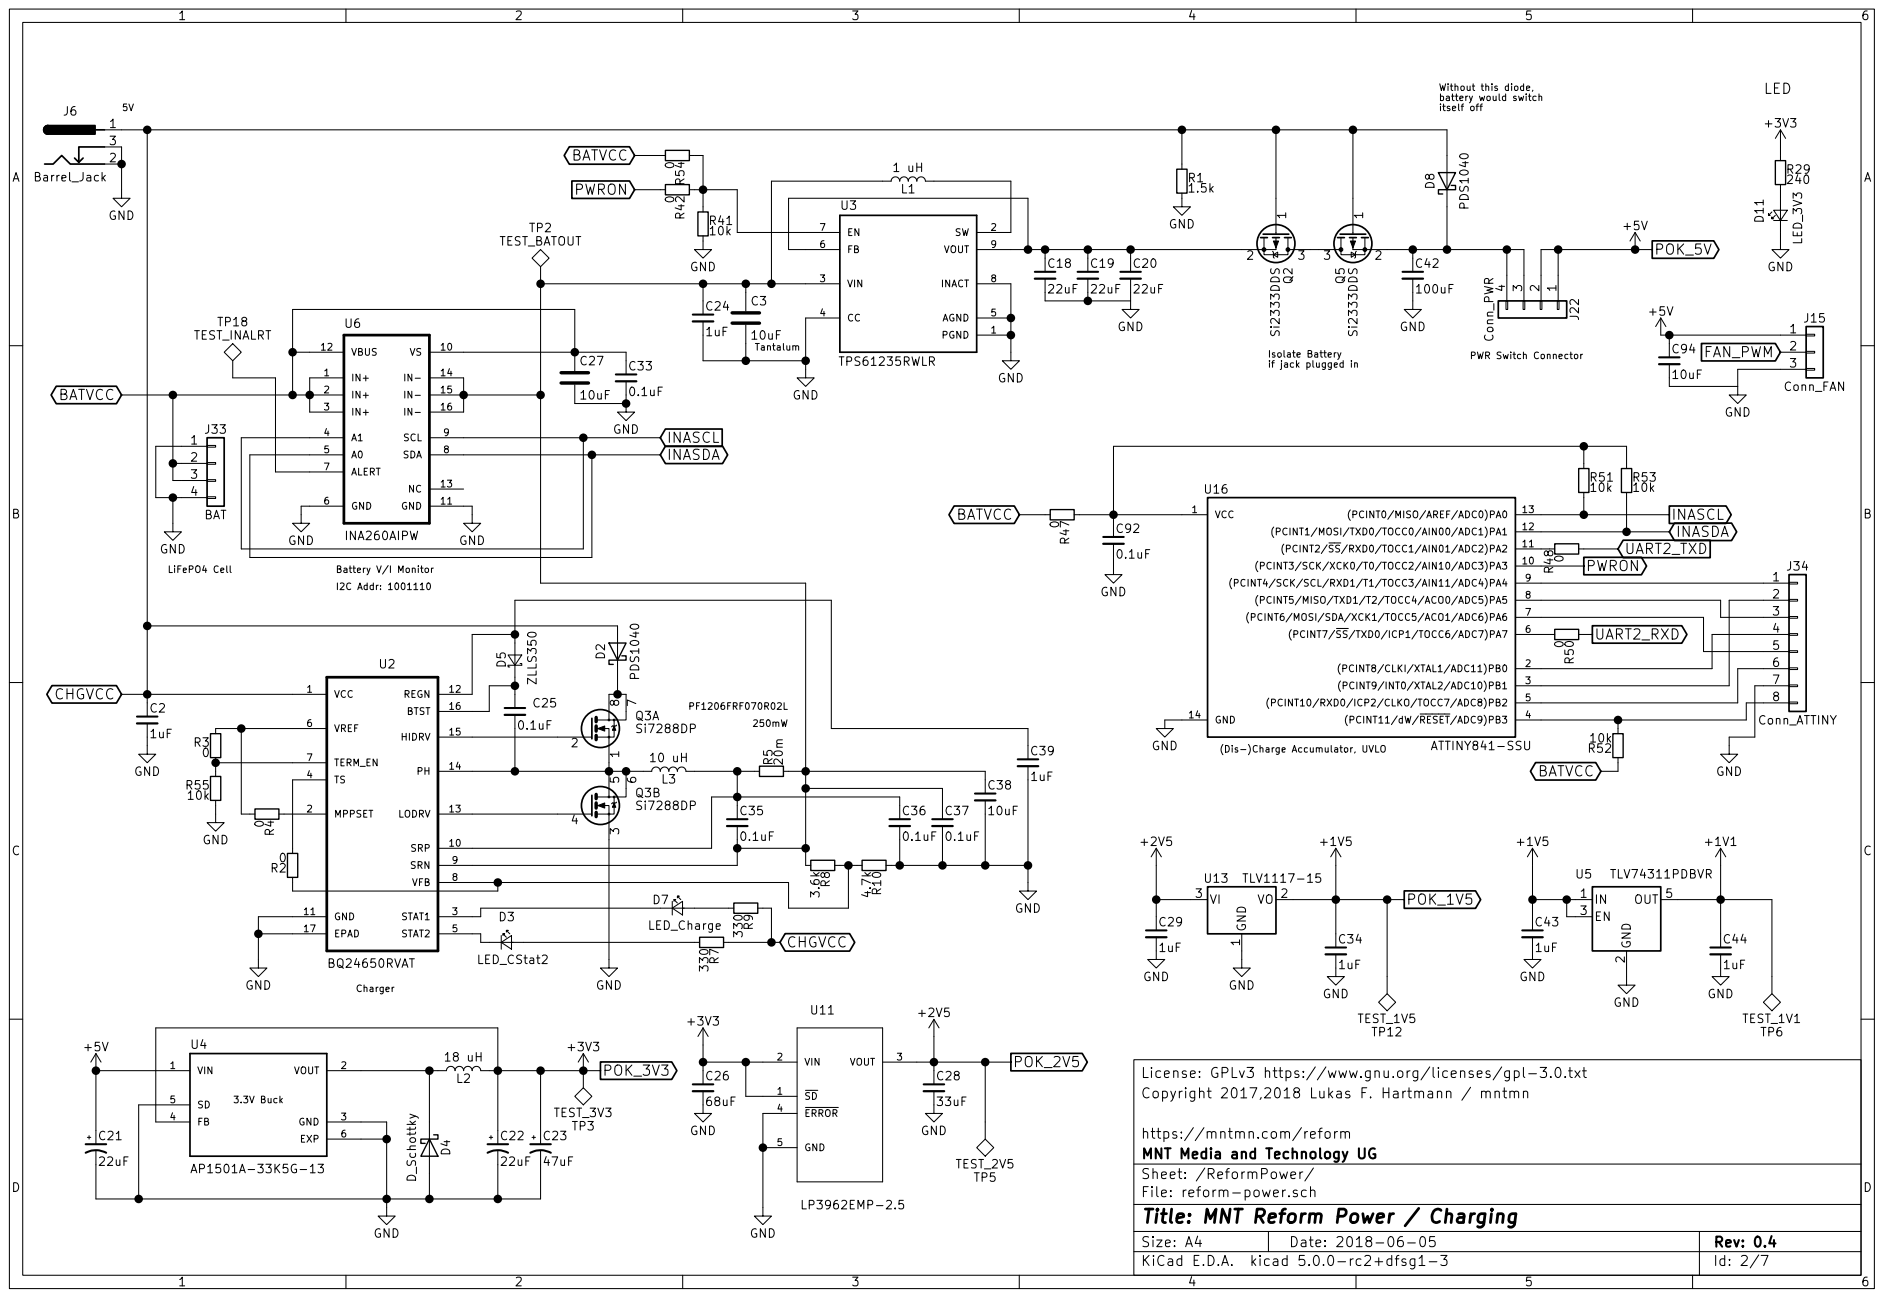
[picture p150: page 1]

LED
PWR Switch Connector Without this diode, battery would switch

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

https://mntmn.com/reform
File: reform-power.sch Sheet: /ReformPower/ MNT Media and Technology UG

Id: 2/7 Title: MNT Reform Power / Charging
