milestogo/reform/historic-reform1/handbook/source/motherboard/reform-motherboard-page-3.pdf

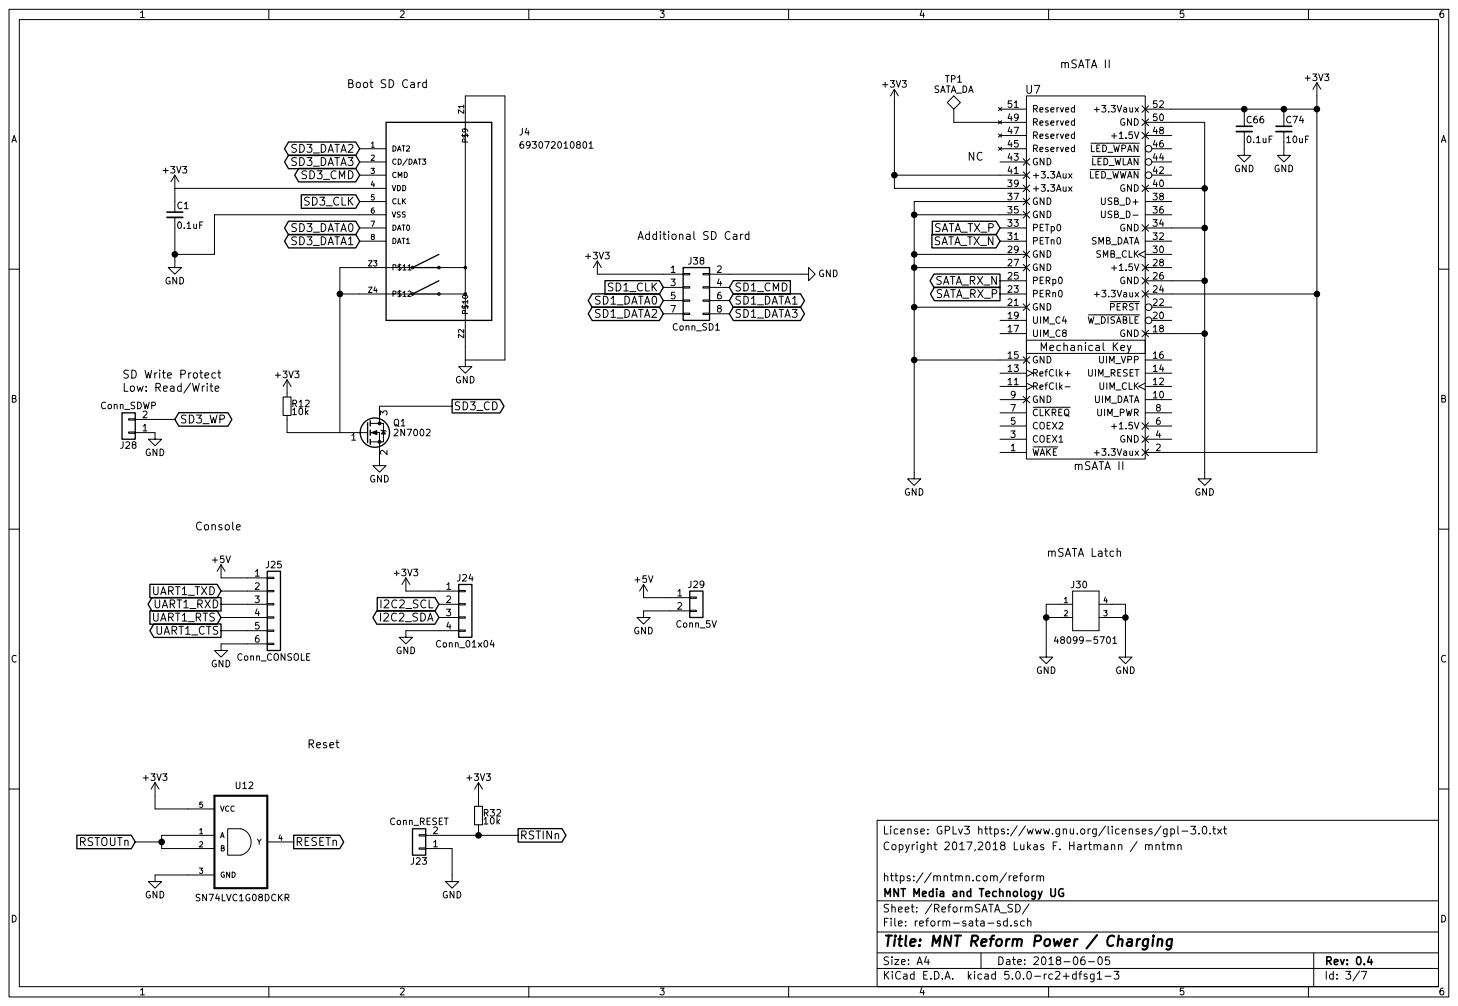
[picture p151: page 1]
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

https://mntmn.com/reform
MNT Media and Technology UG
File: reform-sata-sd.sch Sheet: /ReformSATA_SD/
Id: 3/7 Title: MNT Reform Power / Charging
