milestogo/reform/historic-reform1/handbook/source/motherboard/reform-motherboard-page-4.pdf

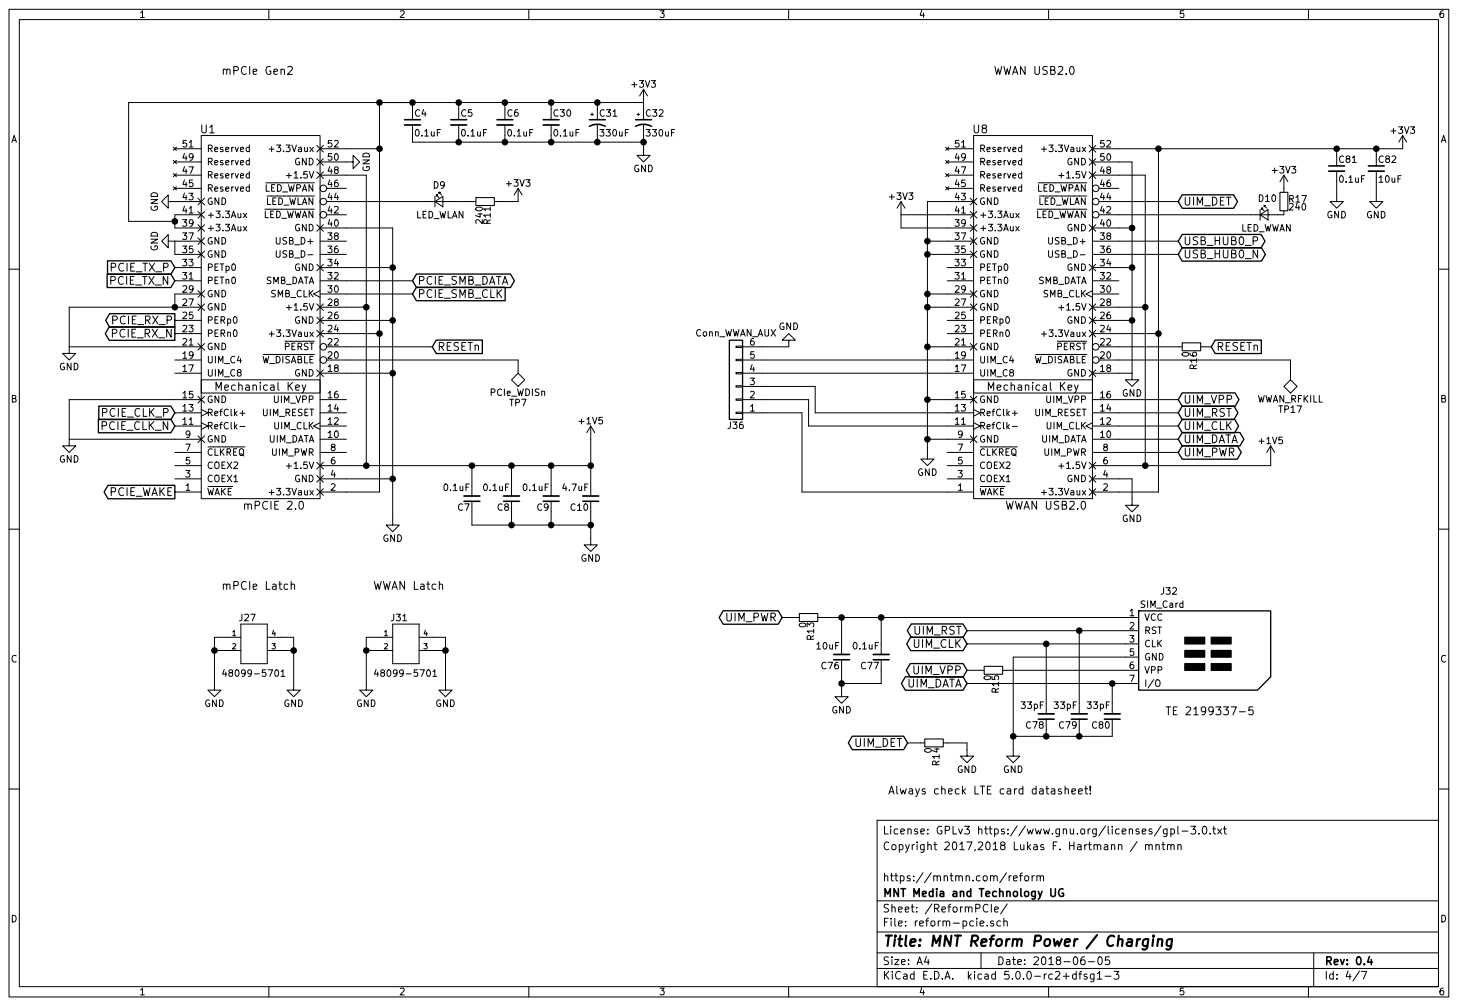
[picture p152: page 1]

VCC 1 RST 2 CLK 3 GND 5 VPP 6

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

https://mntmn.com/reform
File: reform-pcie.sch Sheet: /ReformPCIe/ MNT Media and Technology UG

Id: 4/7 Title: MNT Reform Power / Charging
