milestogo/reform/historic-reform1/handbook/source/motherboard/reform-motherboard-page-5.pdf

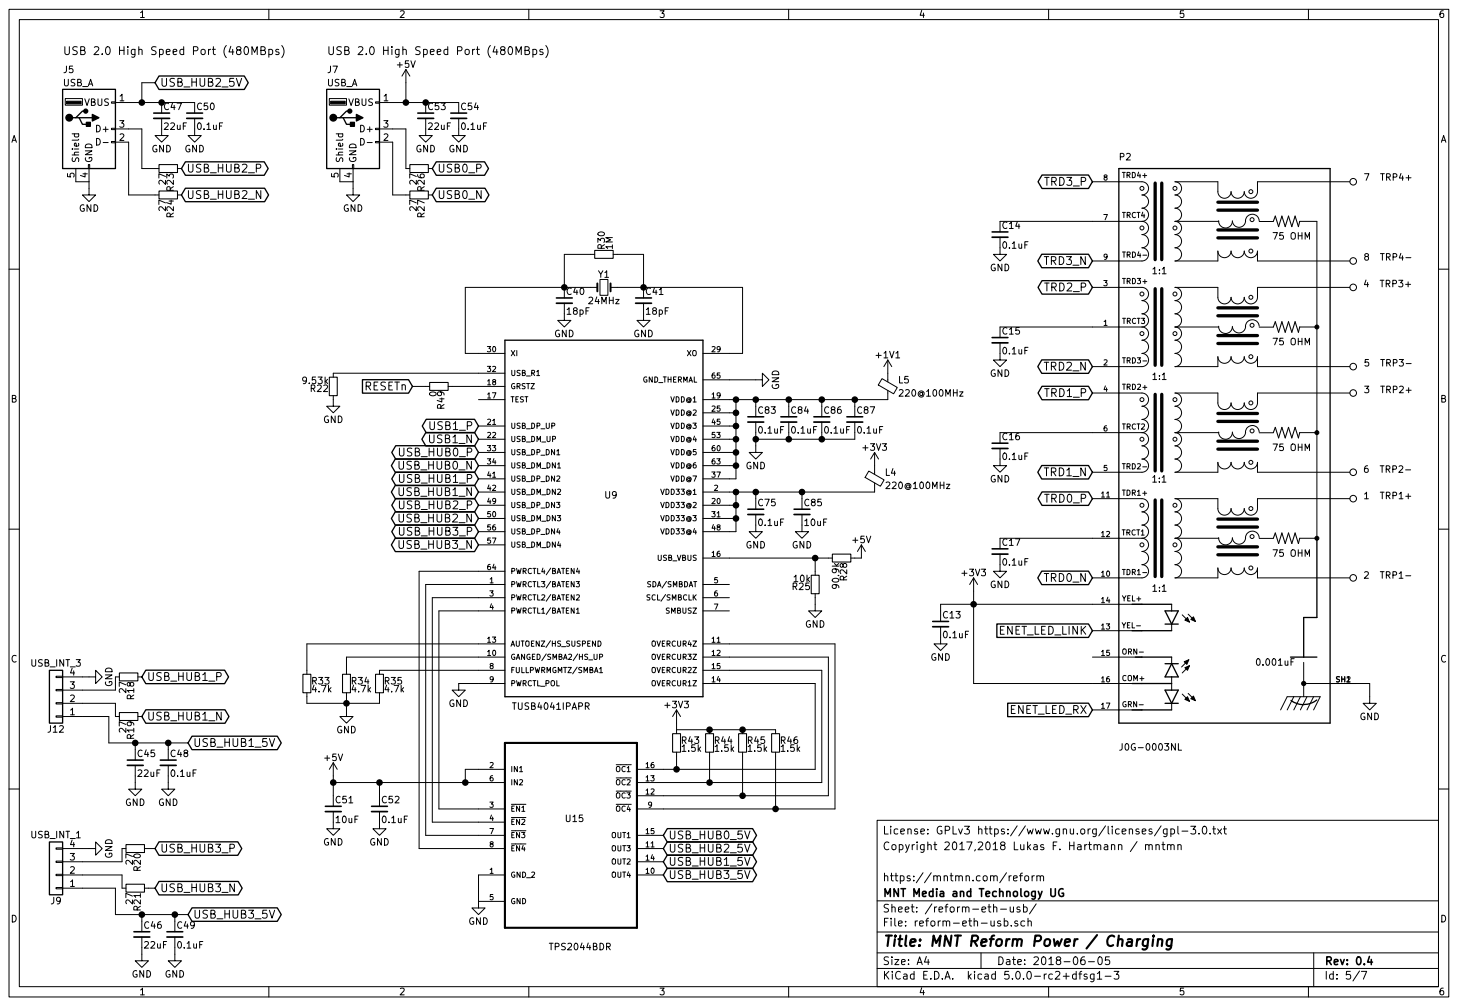
[picture p153: page 1]

USB 2.0 High Speed Port (480MBps)
J7USB_A

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

https://mntmn.com/reform
File: reform-eth-usb.sch Sheet: /reform-eth-usb/ MNT Media and Technology UG

Id: 5/7 Title: MNT Reform Power / Charging
