milestogo/reform/historic-reform1/handbook/source/motherboard/reform-motherboard-page-7.pdf

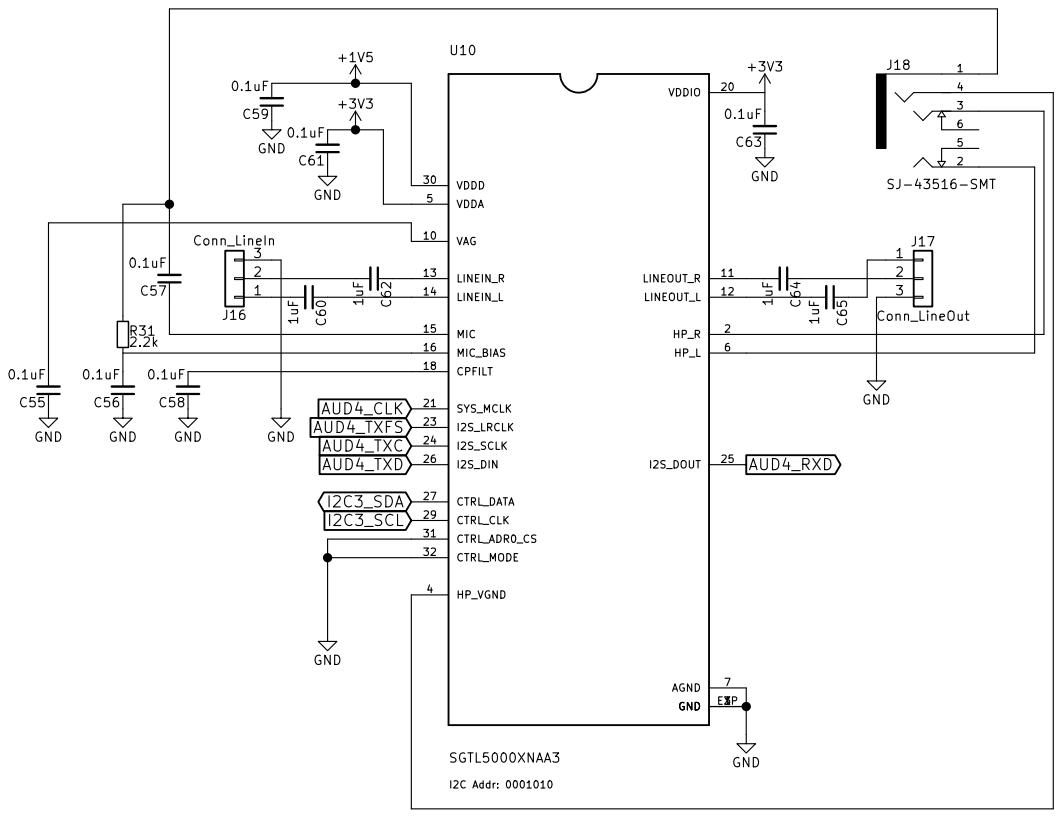
[picture p154: page 1]

Copyright 2017,2018 Lukas F. Hartmann / mntmn

https://mntmn.com/reform
File: reform-audio.sch Sheet: /ReformAudio/ MNT Media and Technology UG

Id: 7/7 Title: MNT Reform Power / Charging
