milestogo/reform/historic-reform1/handbook/source/case/bottom_plate.pdf

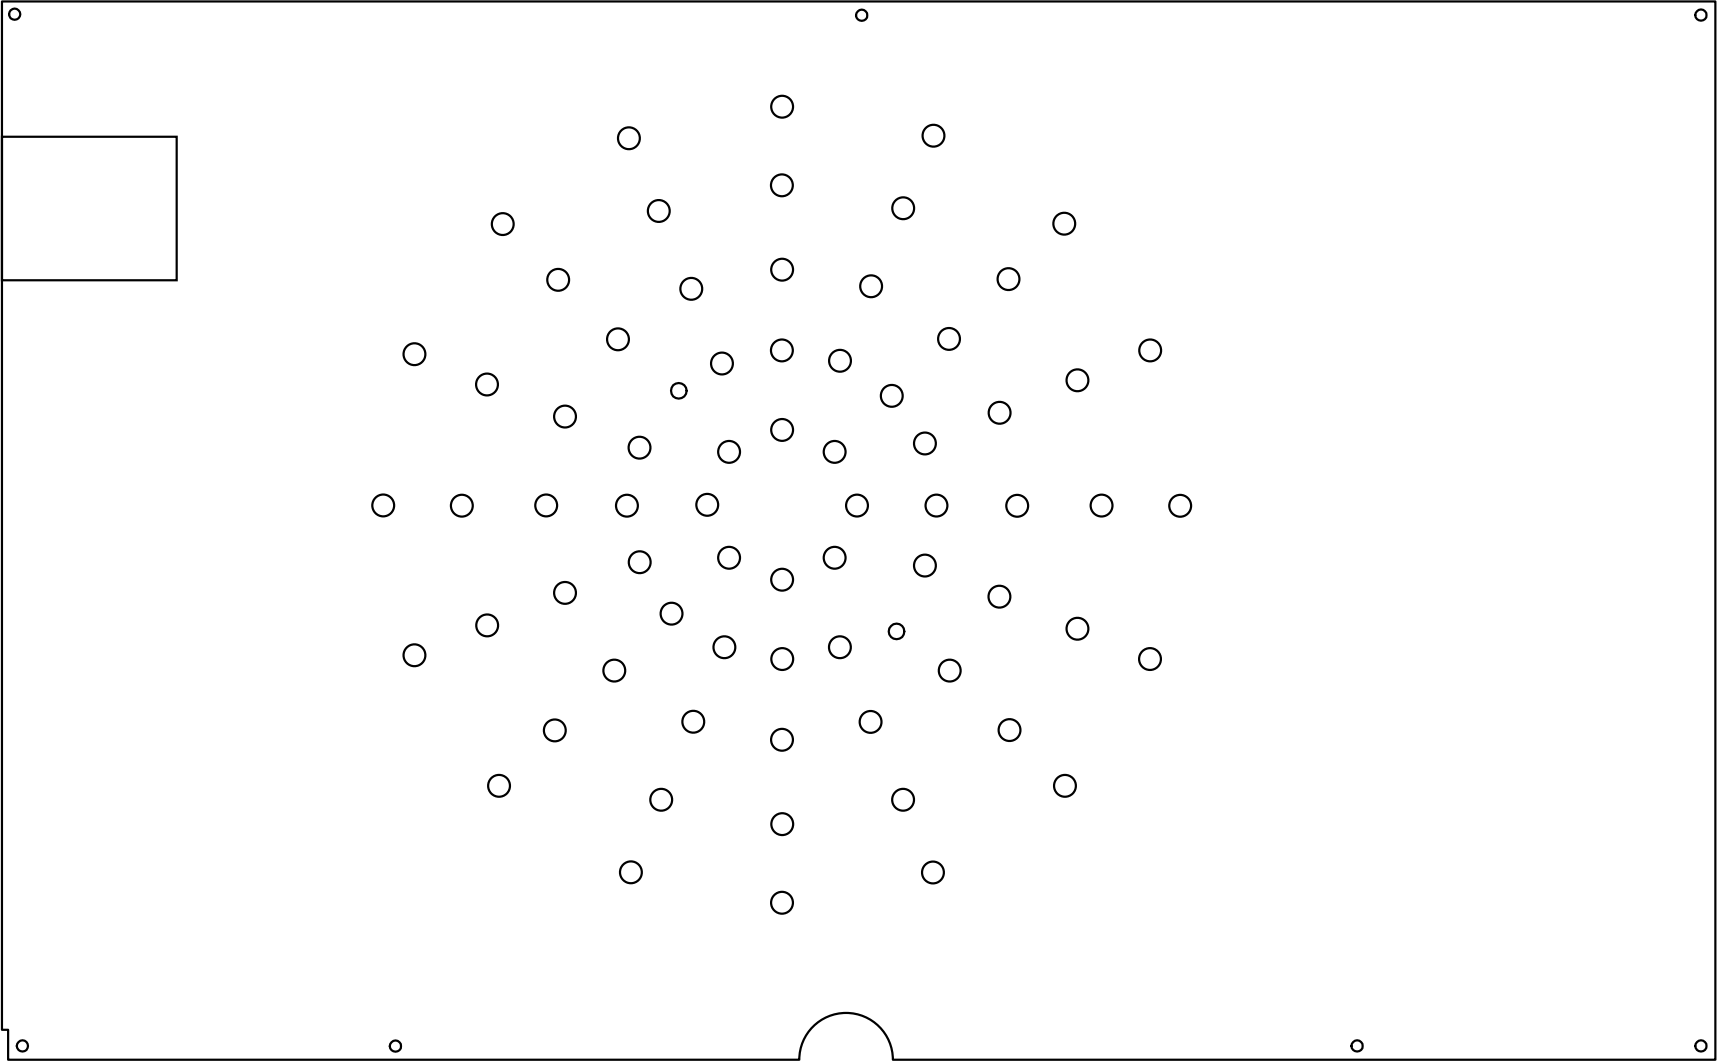
[picture p158: page 1]
