milestogo/reform/historic-reform1/handbook/source/case/ports.pdf

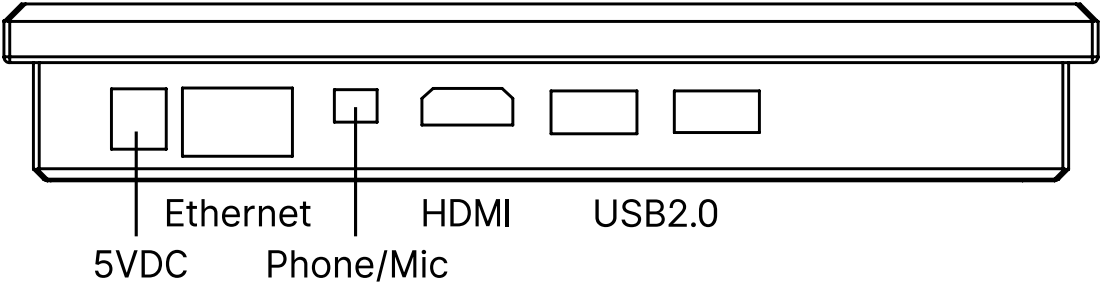
[picture p159: page 1]
