milestogo/reform/historic-reform1/handbook/source/case/screen_front.pdf

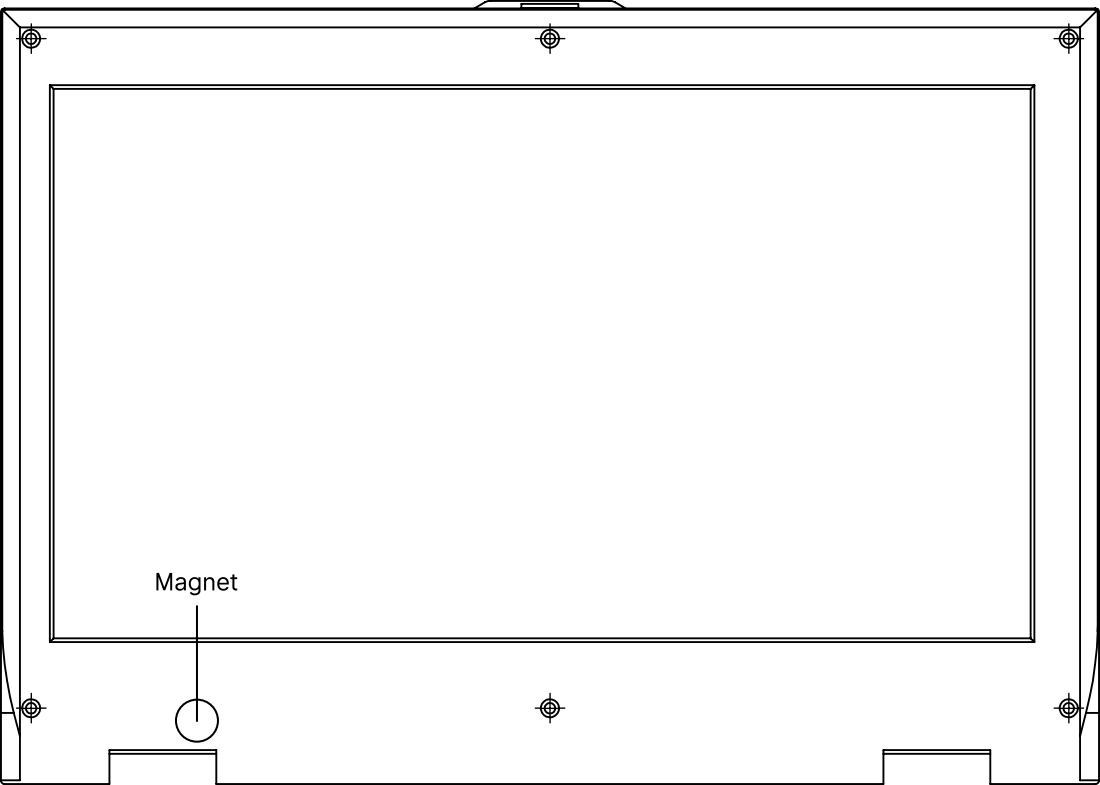
[picture p160: page 1]
