milestogo/reform/historic-reform1/handbook/source/case/screen_support.pdf

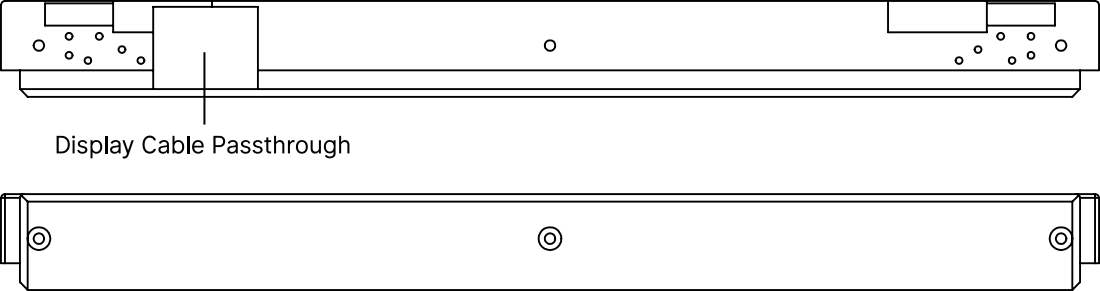
[picture p161: page 1]
