milestogo/reform/historic-reform1/handbook/source/keyboard/keyboard.pdf

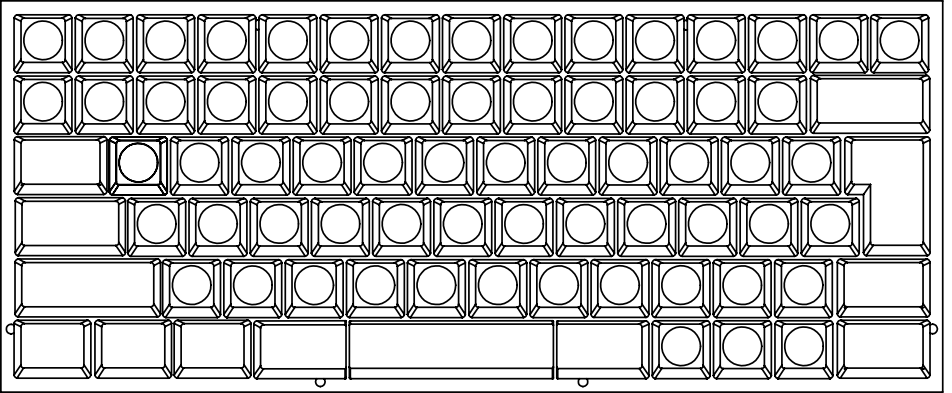
[picture p162: page 1]
