milestogo/reform/historic-reform1/handbook/source/keyboard/reform-keyboard-page-1.pdf

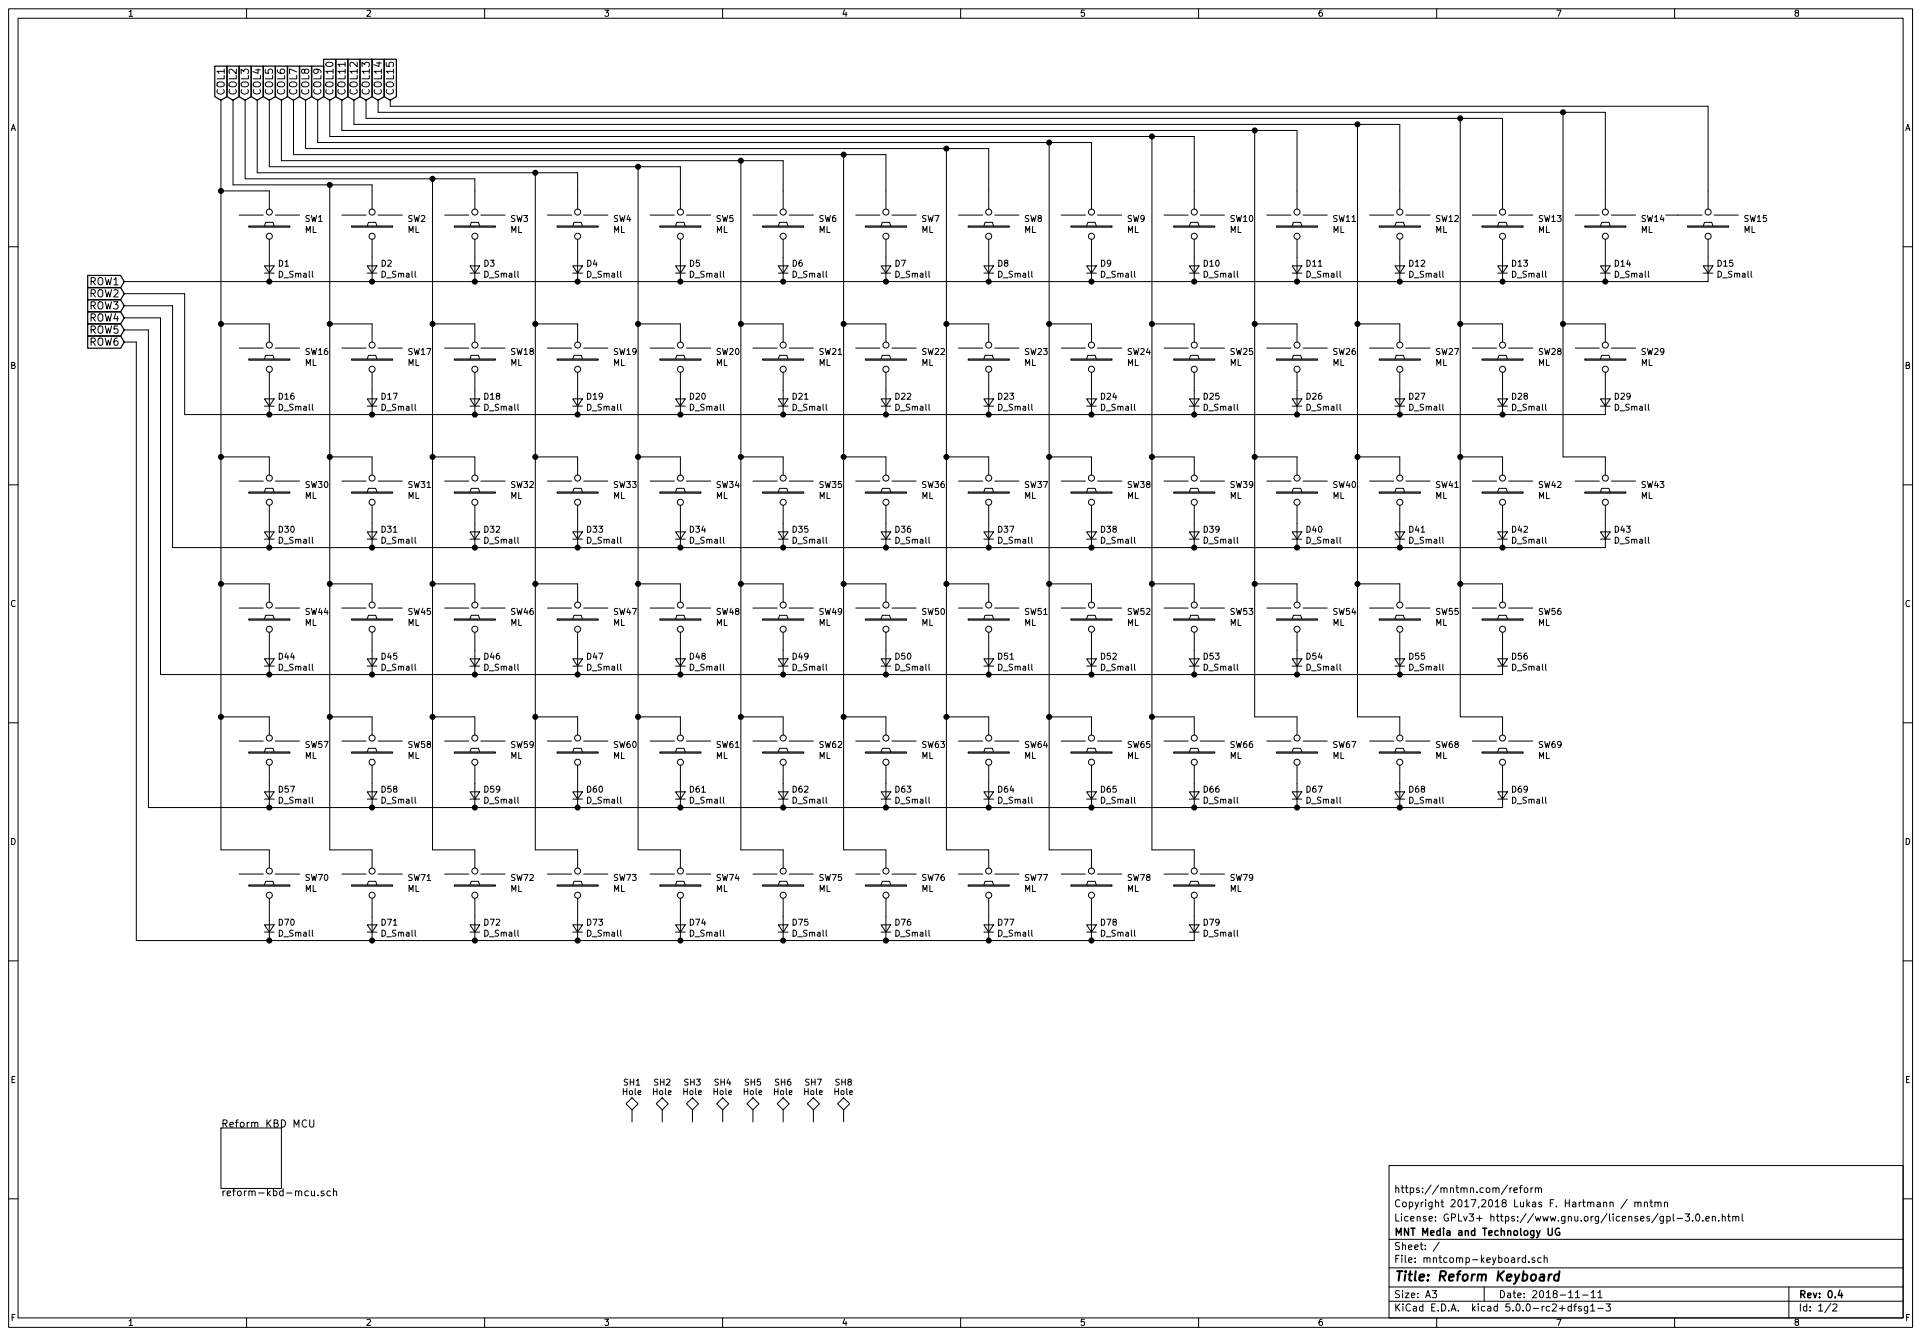
[picture p163: page 1]

reform-kbd-mcu.sch

https://mntmn.com/reform
Copyright 2017,2018 Lukas F. Hartmann / mntmn
License: GPLv3+ https://www.gnu.org/licenses/gpl-3.0.en.html
File: mntcomp-keyboard.sch Sheet: / MNT Media and Technology UG

Id: 1/2 Title: Reform Keyboard
