milestogo/reform/historic-reform1/handbook/source/keyboard/reform-keyboard-page-2.pdf

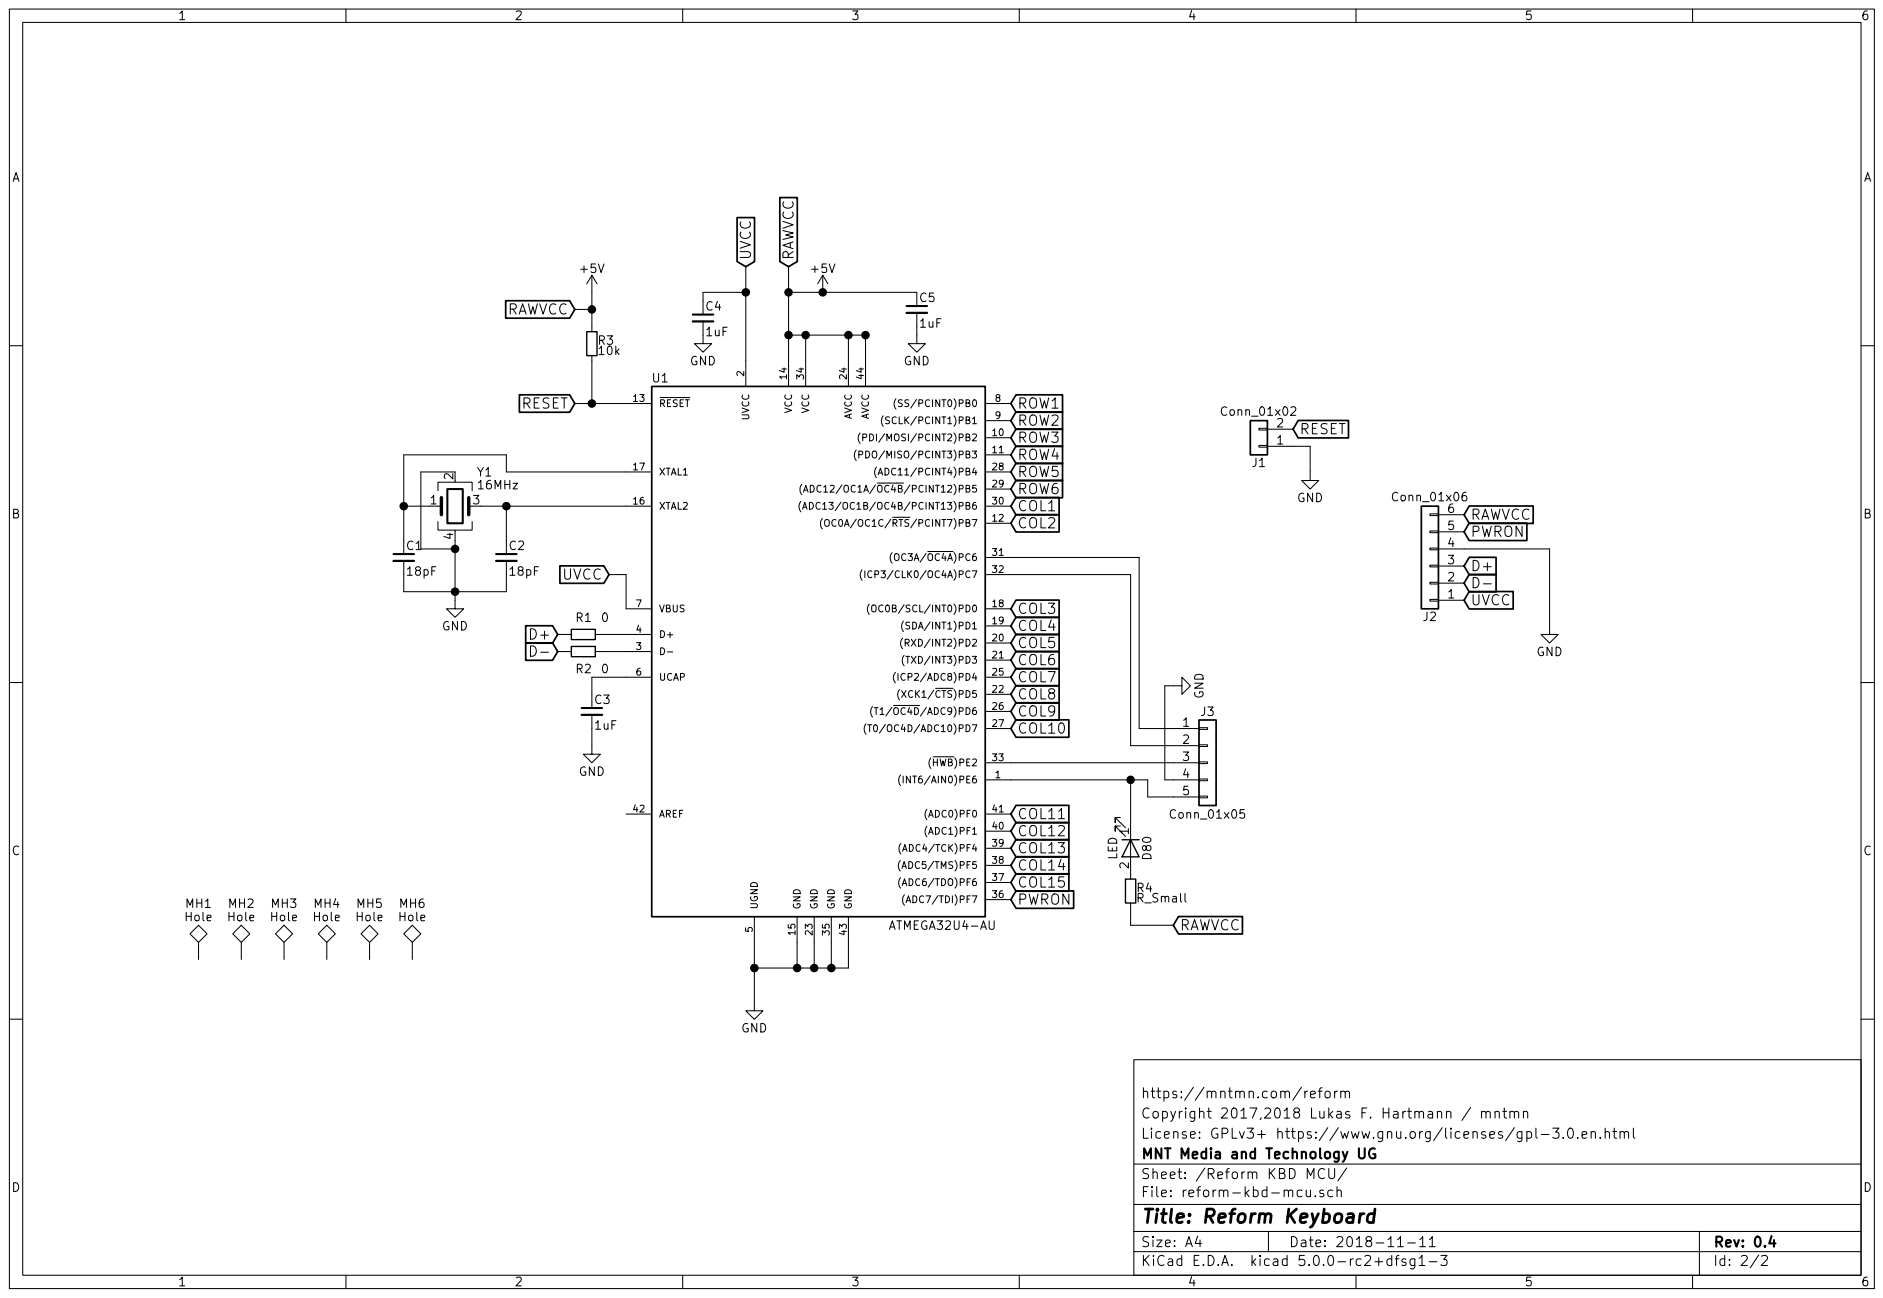
[picture p164: page 1]

https://mntmn.com/reform
Copyright 2017,2018 Lukas F. Hartmann / mntmn
License: GPLv3+ https://www.gnu.org/licenses/gpl-3.0.en.html
File: reform-kbd-mcu.sch Sheet: /Reform KBD MCU/ MNT Media and Technology UG

Id: 2/2 Title: Reform Keyboard
