milestogo/reform/historic-reform1/handbook/source/motherboard/reform-motherboard-markup.pdf

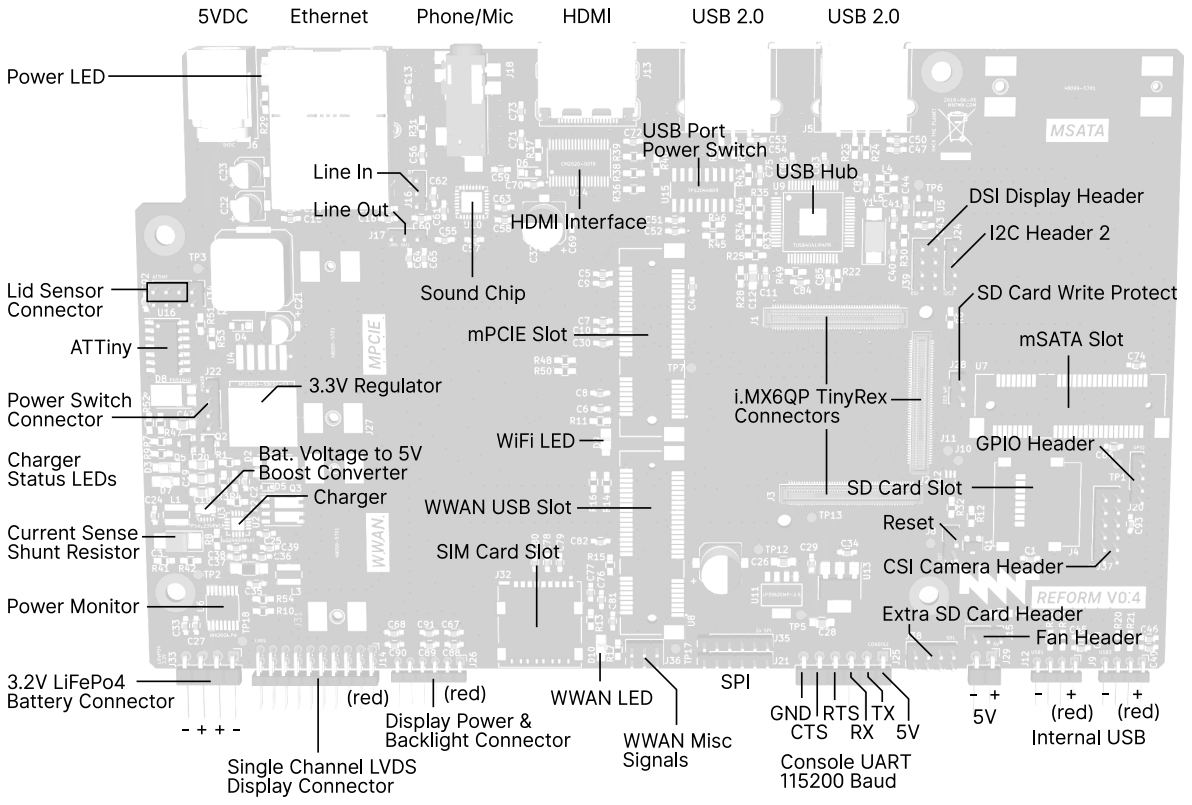
[picture p165: page 1]
