milestogo/reform/historic-reform1/handbook/source/motherboard/reform-motherboard-markupb.pdf

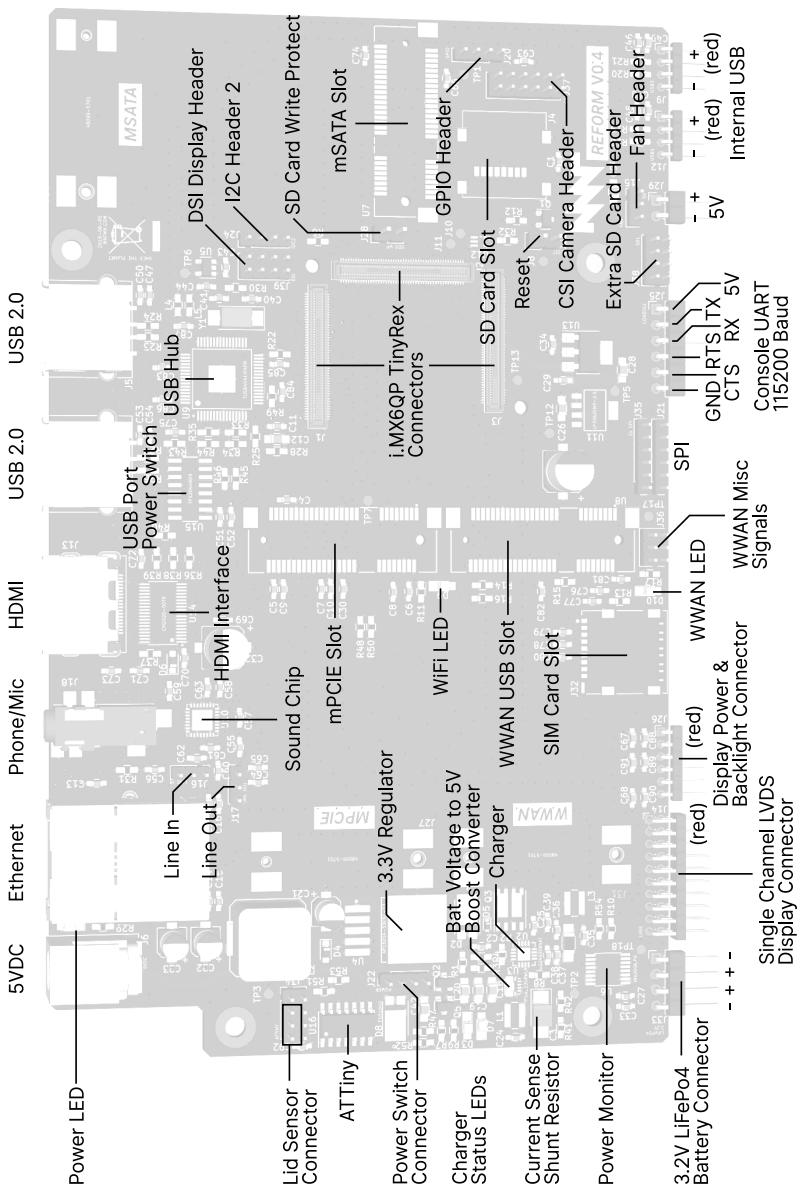
[picture p166: page 1]
