milestogo/reform/historic-reform1/handbook/source/trackball/reform-trackball.pdf

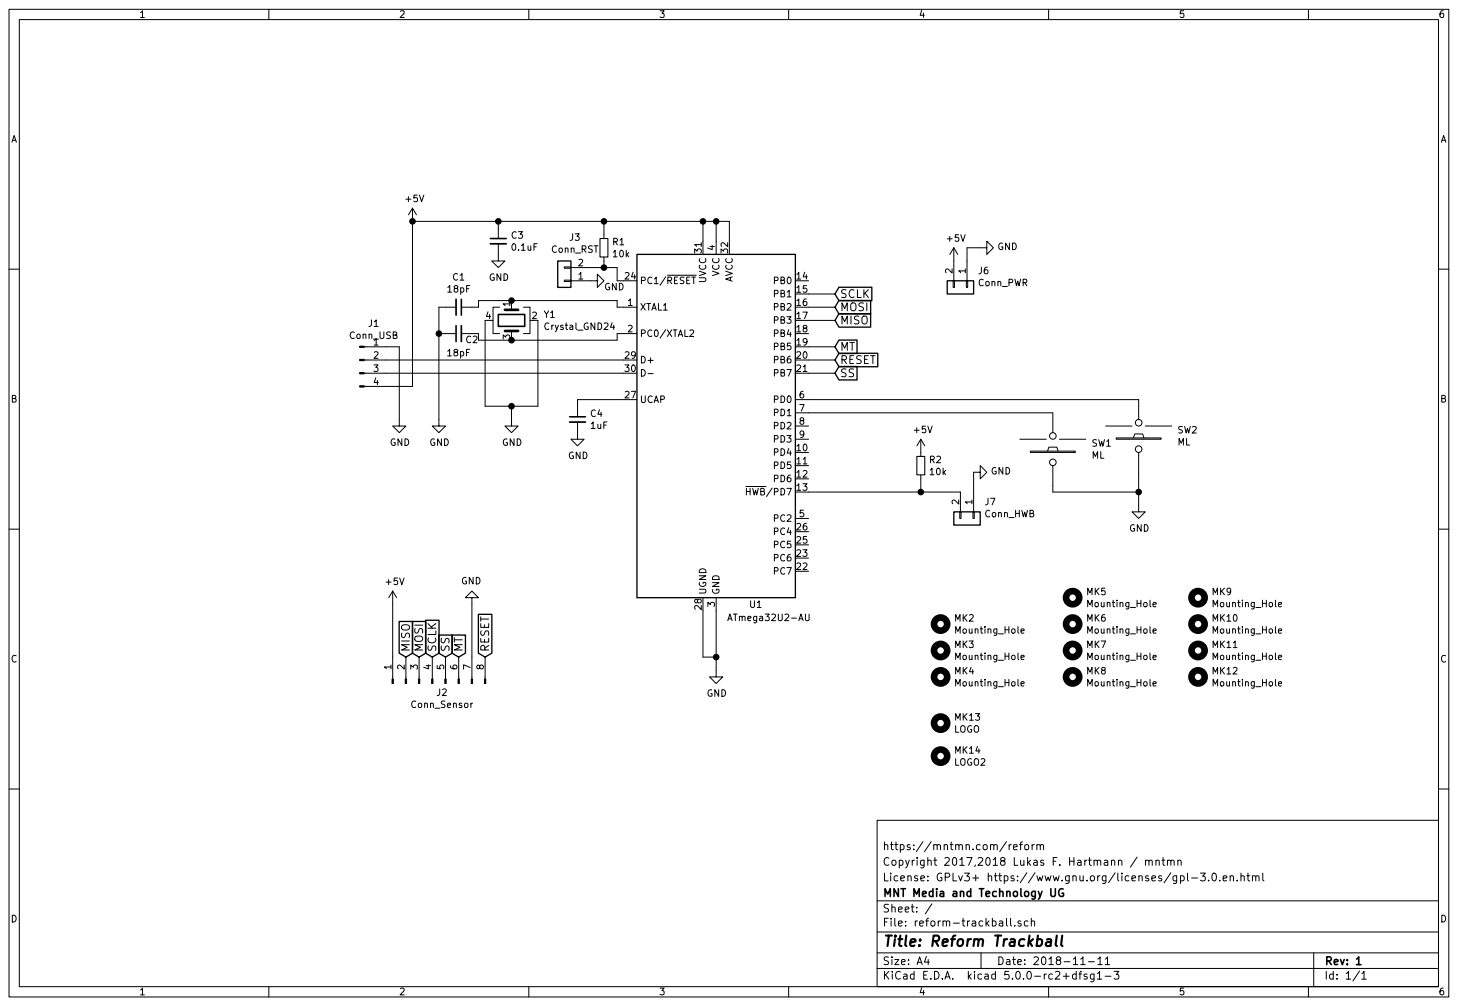
[picture p167: page 1]

https://mntmn.com/reform
Copyright 2017,2018 Lukas F. Hartmann / mntmn
License: GPLv3+ https://www.gnu.org/licenses/gpl-3.0.en.html
Id: 1/1 Title: Reform Trackball File: reform-trackball.sch Sheet: / MNT Media and Technology UG
