milestogo/reform/historic-reform1/handbook/source/trackball/trackball.pdf

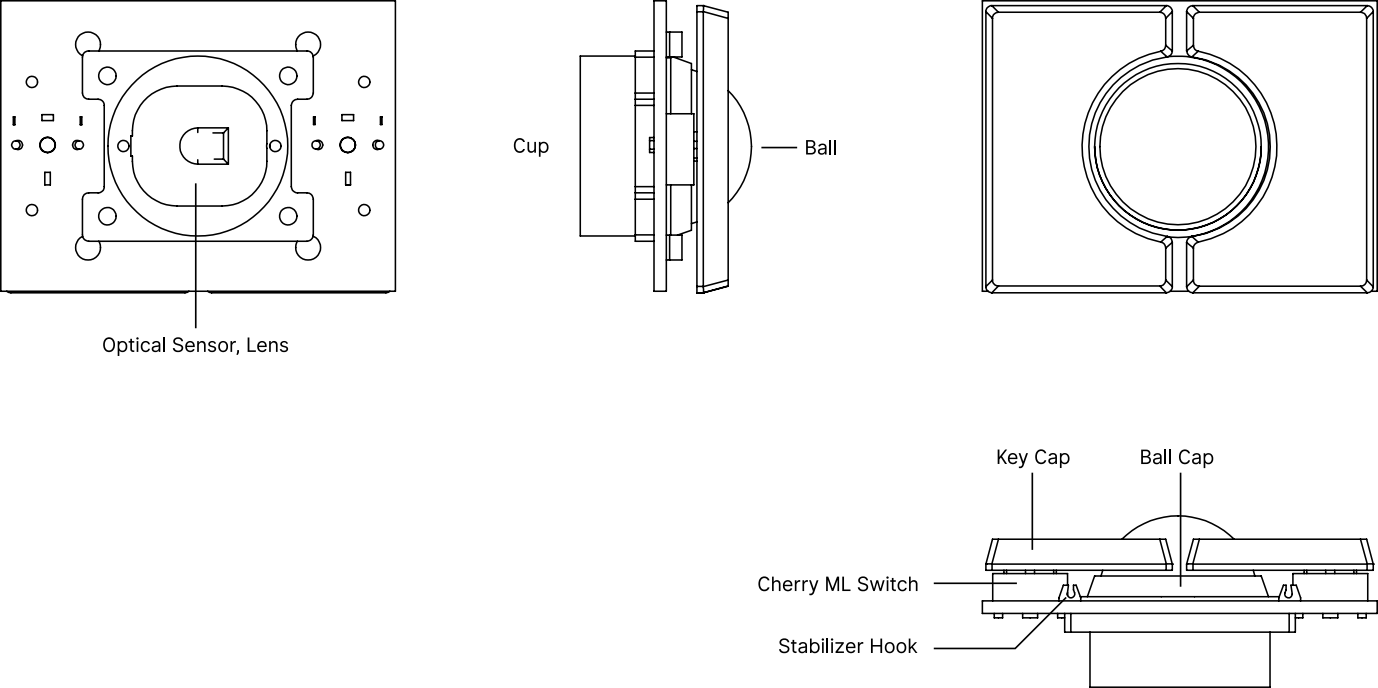
[picture p168: page 1]
